ageppert/Core-64-Interactive-Core-Memory-Badge/Electronic Design/Core64 CB v0.4/Core64 CB V0.4 PCB Back.pdf

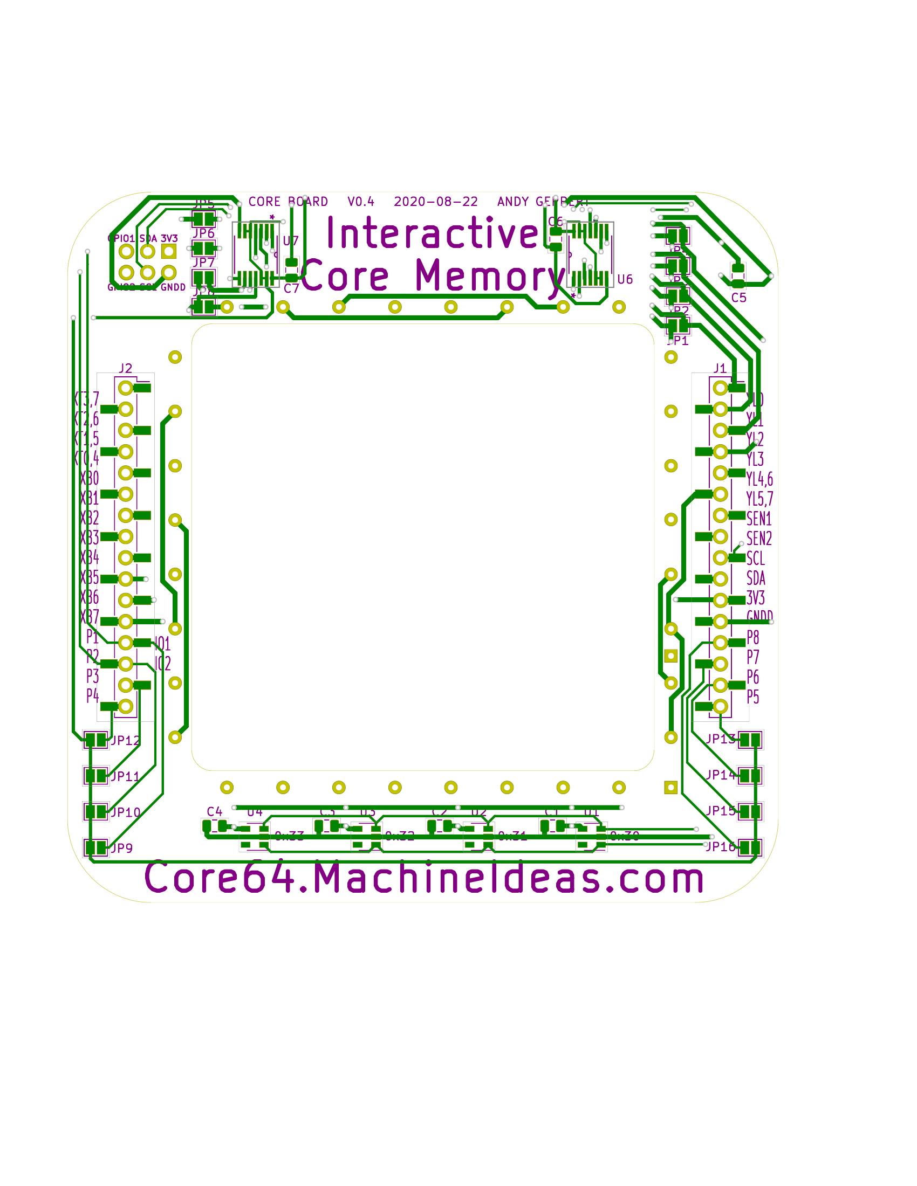
[picture p16: page 1]
