ageppert/Core-64-Interactive-Core-Memory-Badge/Datasheets/NPN to N-Channel pin compatible.png

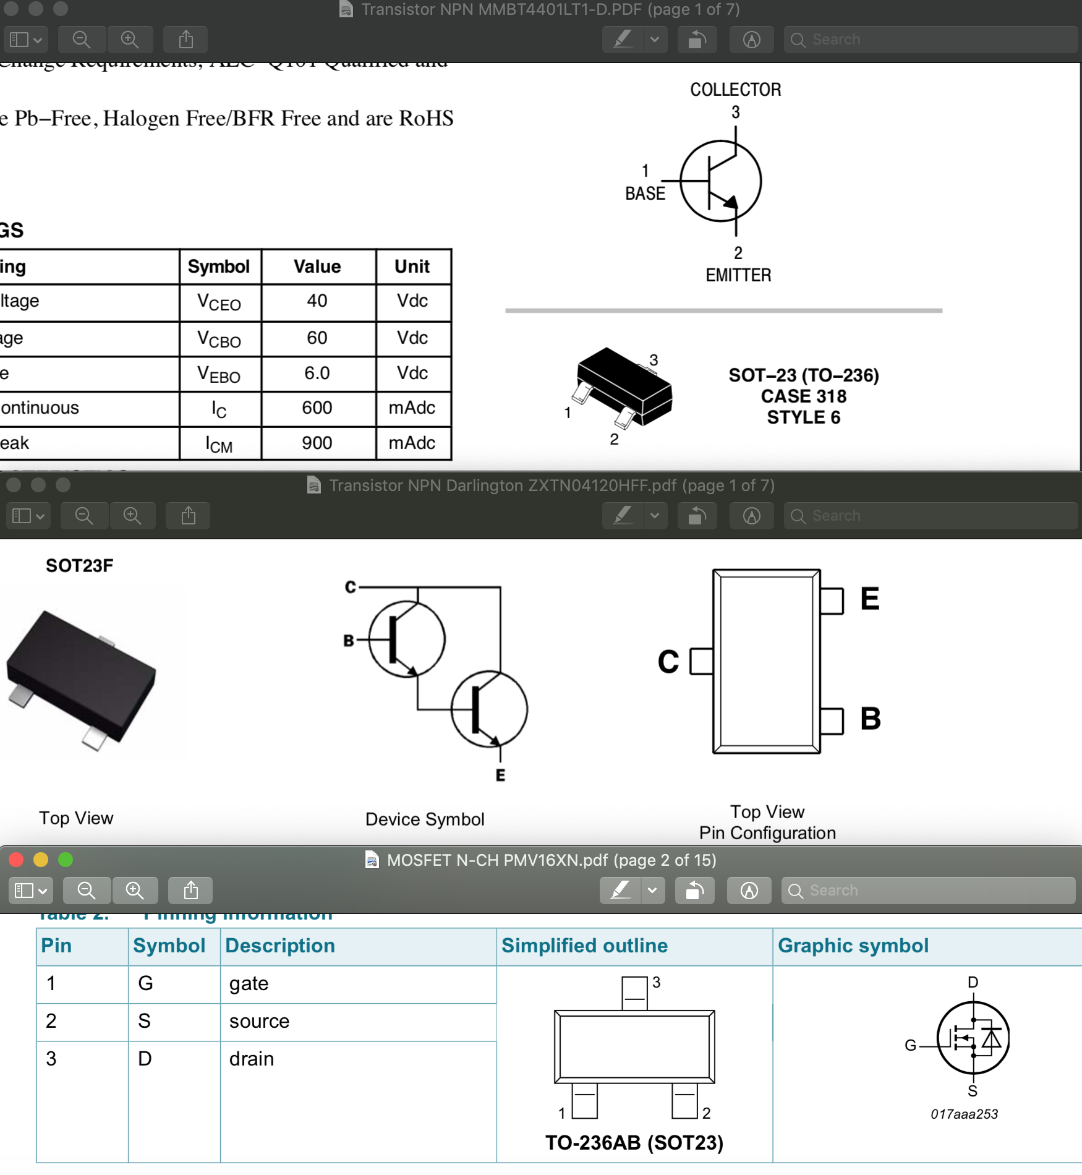
Datasheets/NPN to N-Channel pin compatible.png
