ageppert/Core-64-Interactive-Core-Memory-Badge/Datasheets/Pimoroni Board Layout Top View.png

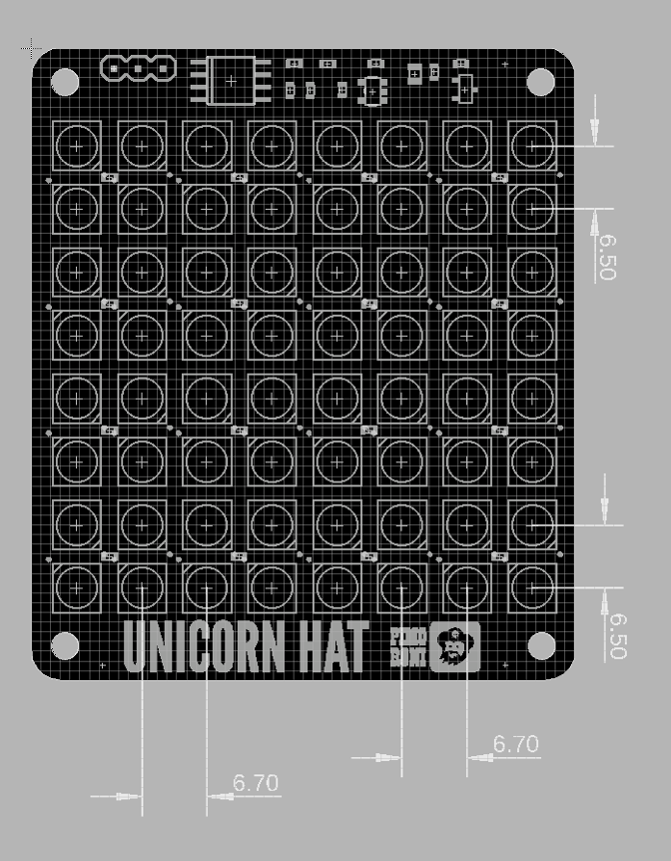
Datasheets/Pimoroni Board Layout Top View.png
