ageppert/Core-64-Interactive-Core-Memory-Badge/Datasheets/PNP to P-Channel pin compatible.png

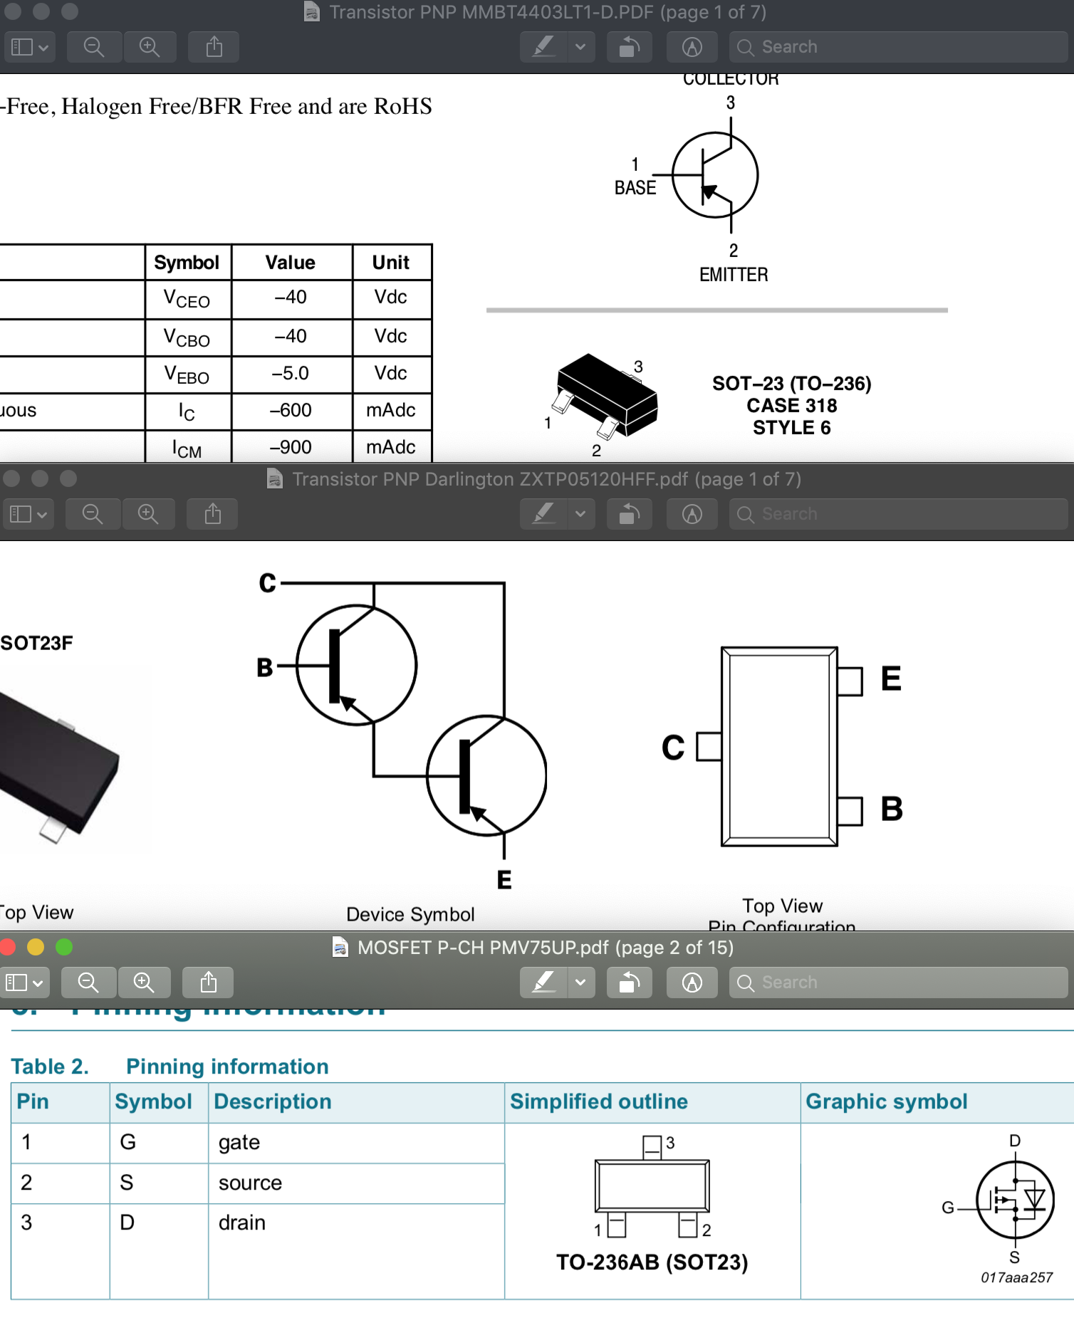
Datasheets/PNP to P-Channel pin compatible.png
