ageppert/Core-64-Interactive-Core-Memory-Badge/Datasheets/Reverse Voltage Protection with MOSFET.png

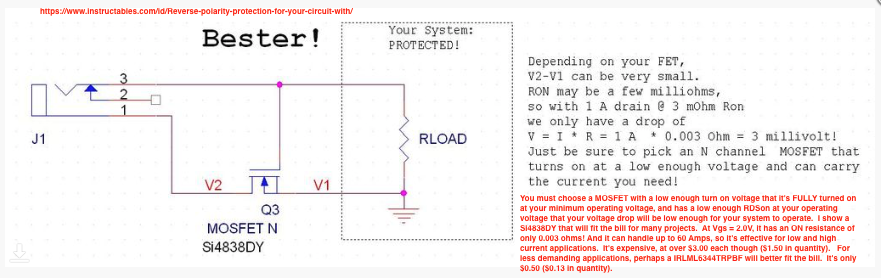
Datasheets/Reverse Voltage Protection with MOSFET.png
