ageppert/Core-64-Interactive-Core-Memory-Badge/Datasheets/Teensy 3.2 schematic.gif

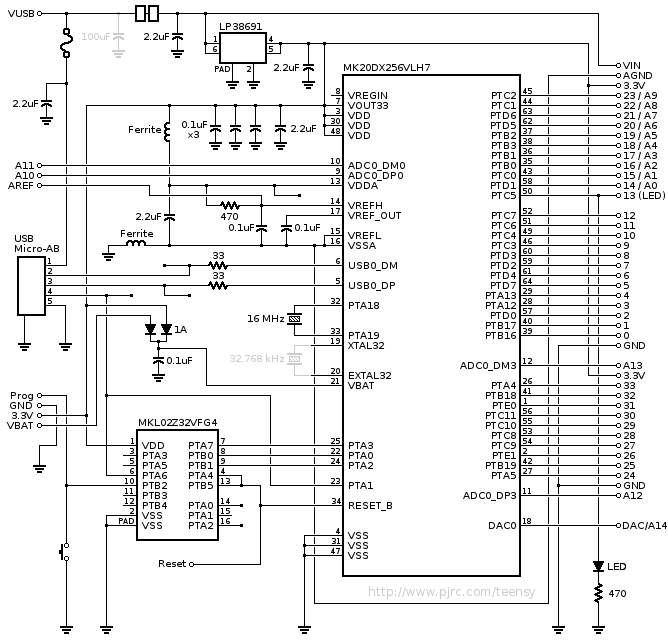
Datasheets/Teensy 3.2 schematic.gif
