ageppert/Core-64-Interactive-Core-Memory-Badge/Datasheets/Teensy LC Schematic.gif

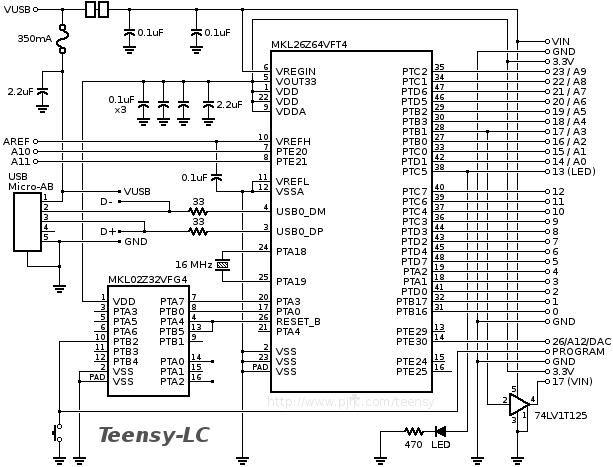
Datasheets/Teensy LC Schematic.gif
