ageppert/Core-64-Interactive-Core-Memory-Badge/Electronic Design/Core64 CB v0.4-NP/Core64 CB v0.4-NP render back.png

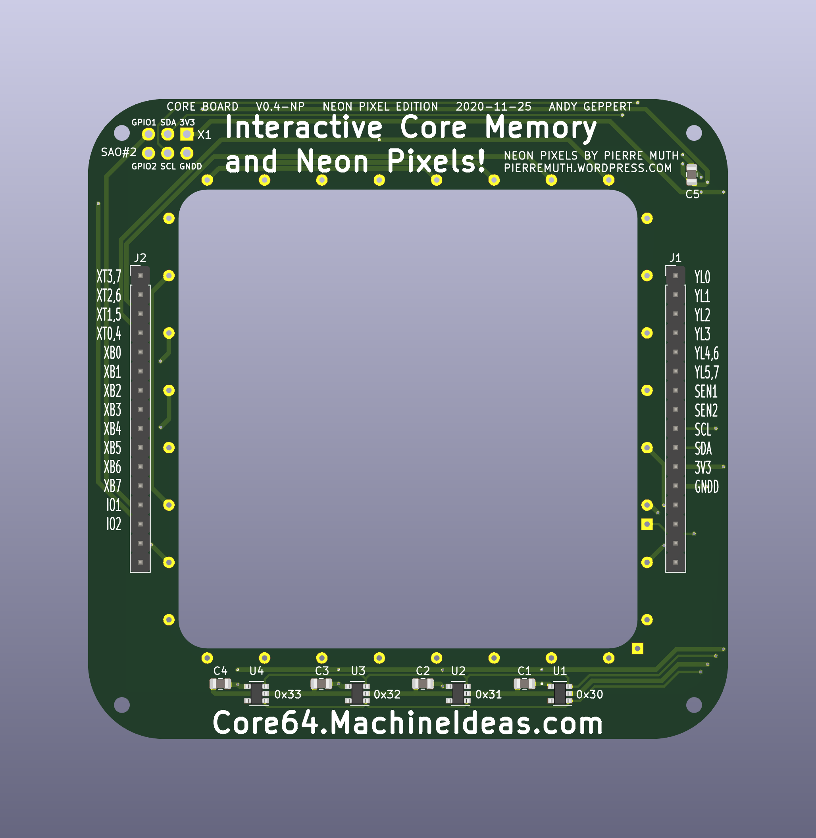
Electronic Design/Core64 CB v0.4-NP/Core64 CB v0.4-NP render back.png
