ageppert/Core-64-Interactive-Core-Memory-Badge/Electronic Design/Core64 HB v0.1/Core64_HB_Outputs/Hacker board V0.1 render front.png

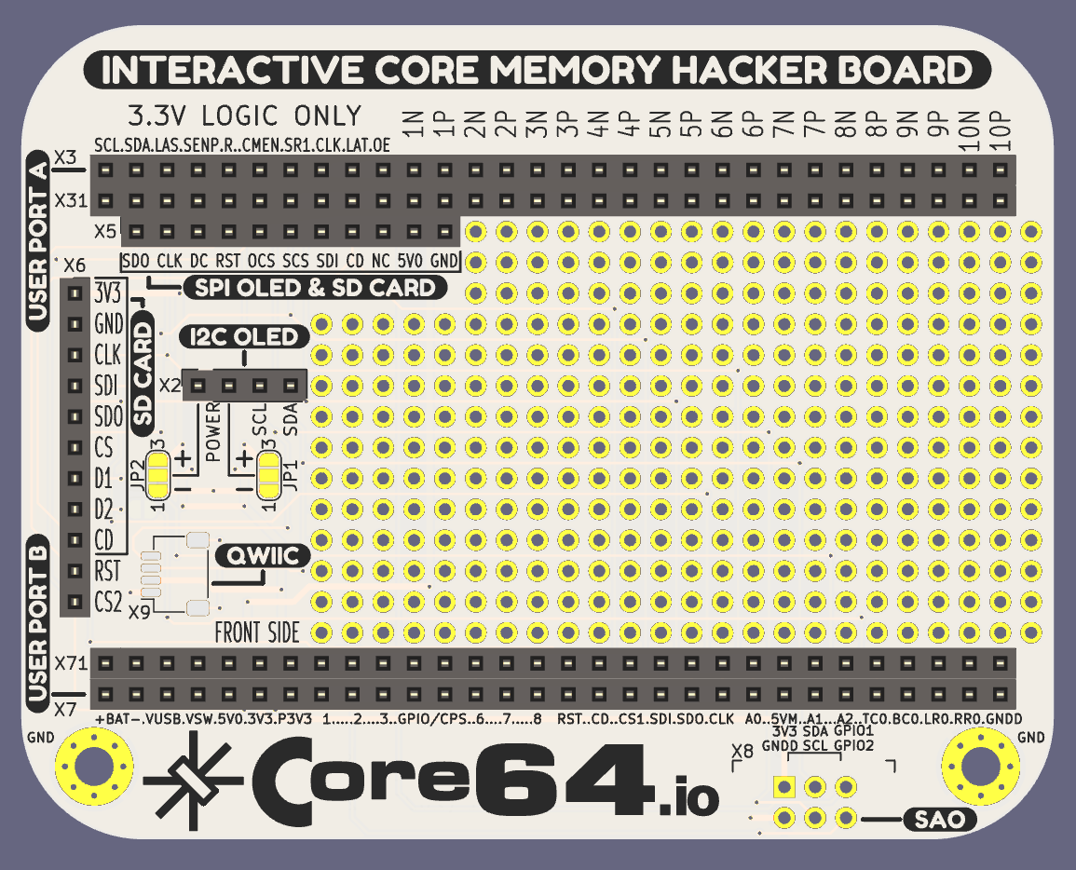
Electronic Design/Core64 HB v0.1/Core64_HB_Outputs/Hacker board V0.1 render front.png
