ageppert/Core-64-Interactive-Core-Memory-Badge/Electronic Design/Core64 LA v1.3 KiCAD 6/C64_LA_V1.3 Schematic and Renders/Core64 LED Array v1.3 Render Front.png

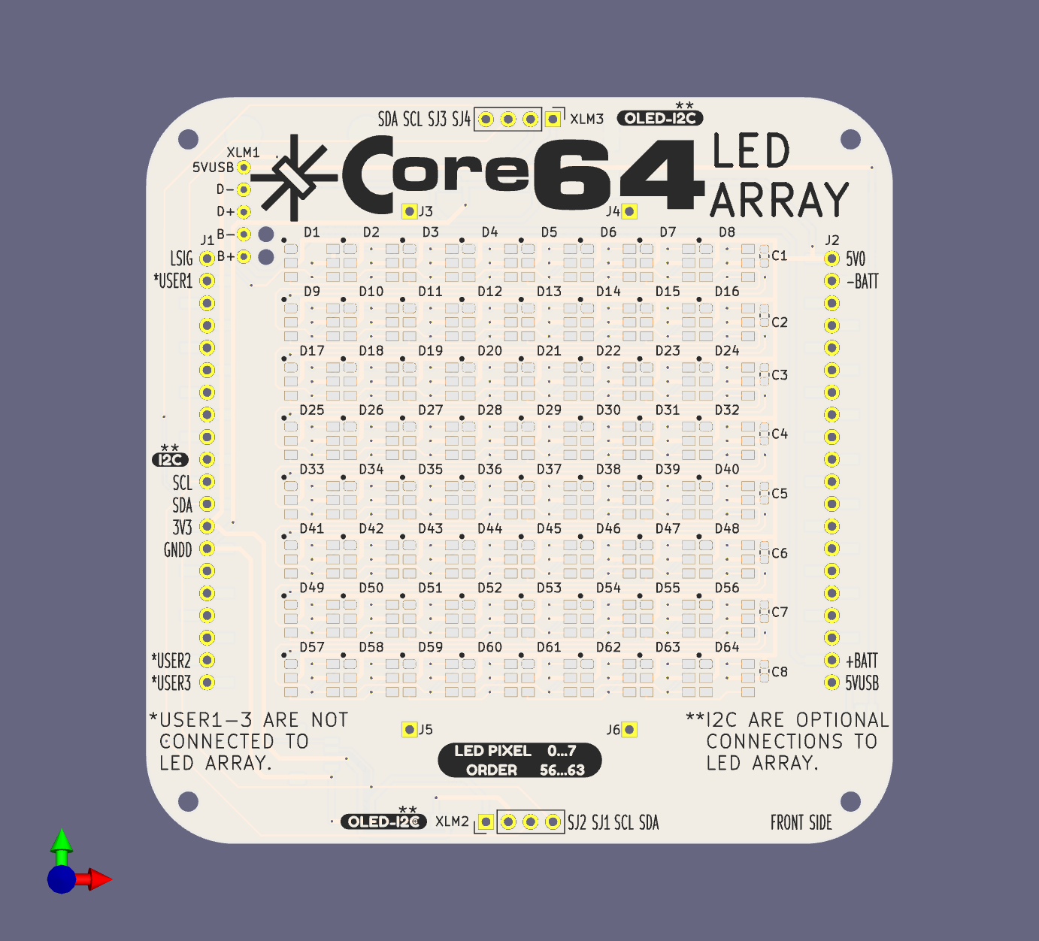
Electronic Design/Core64 LA v1.3 KiCAD 6/C64_LA_V1.3 Schematic and Renders/Core64 LED Array v1.3 Render Front.png
