ageppert/Core-64-Interactive-Core-Memory-Badge/Electronic Design/Core64 LB v0.6/Core64 LB v0.6 Render Top.png

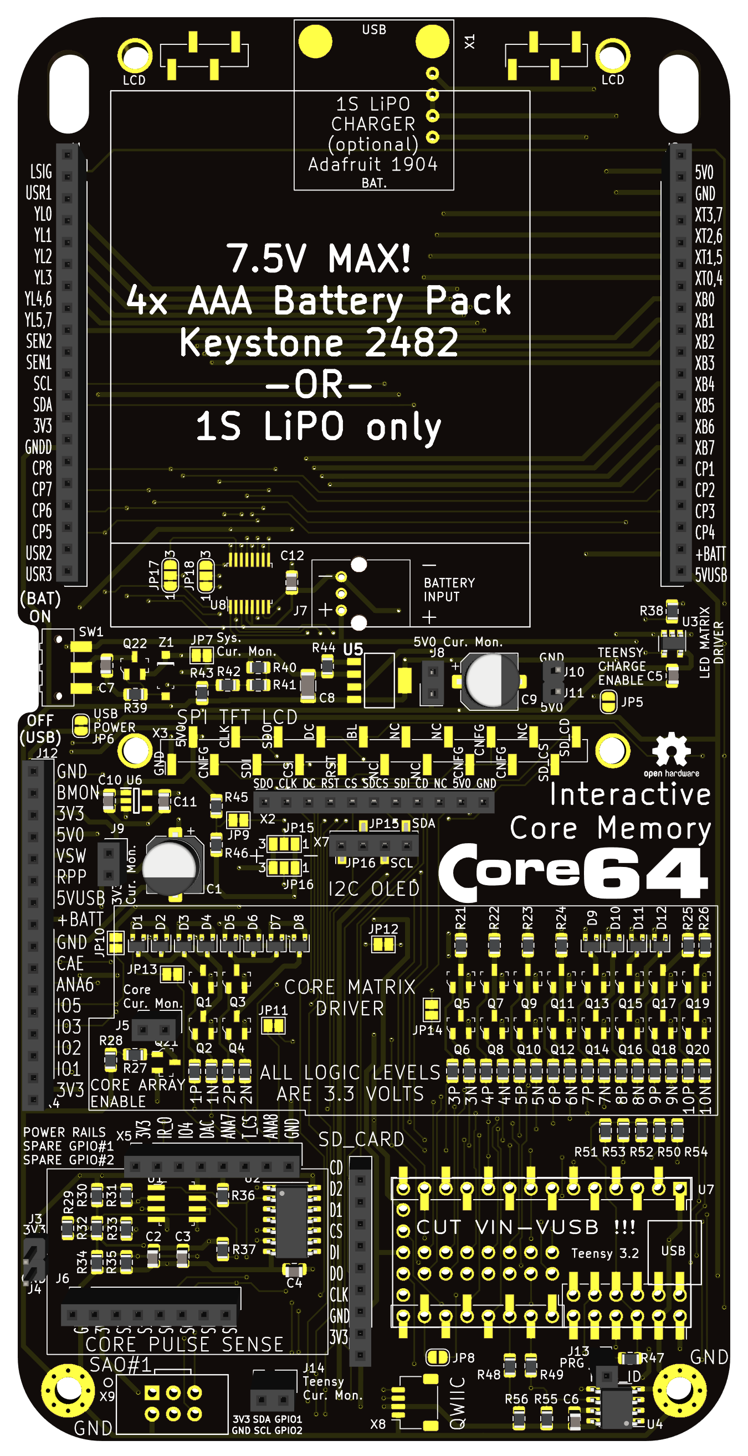
Electronic Design/Core64 LB v0.6/Core64 LB v0.6 Render Top.png
