ageppert/Core-64-Interactive-Core-Memory-Badge/Electronic Design/Core64 LB v0.8 KiCAD 6/Core64_LB_V0.8.5 2025-04-24 Qty 30/904882295554048-Produce_DanZhi.SMT_Snapshot.Top.2721632A_Y74.SMT025042462656.png

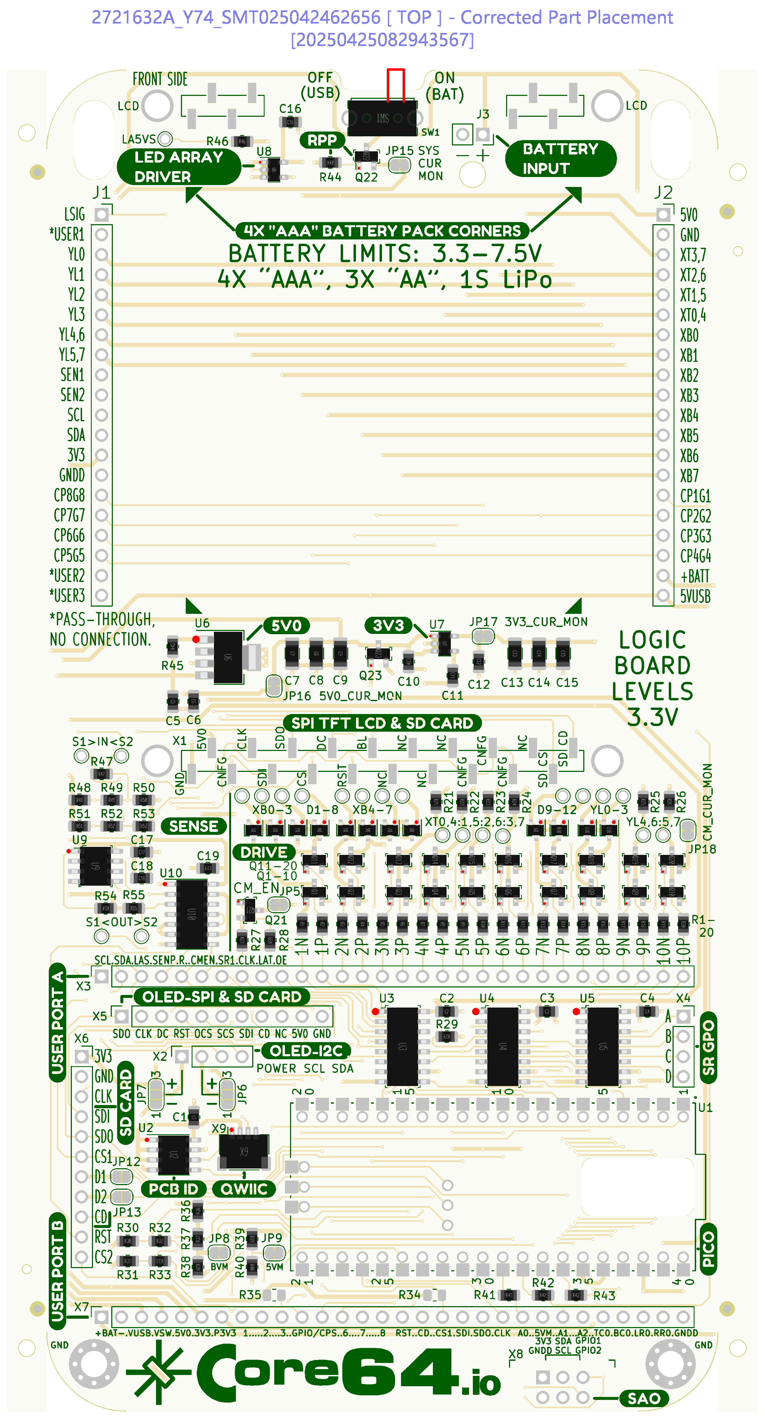
Electronic Design/Core64 LB v0.8 KiCAD 6/Core64_LB_V0.8.5 2025-04-24 Qty 30/904882295554048-Produce_DanZhi.SMT_Snapshot.Top.2721632A_Y74.SMT025042462656.png
