ageppert/Core-64-Interactive-Core-Memory-Badge/Electronic Design/Core64 LM v1.0/Core64 LM v1.0 Render Back.png

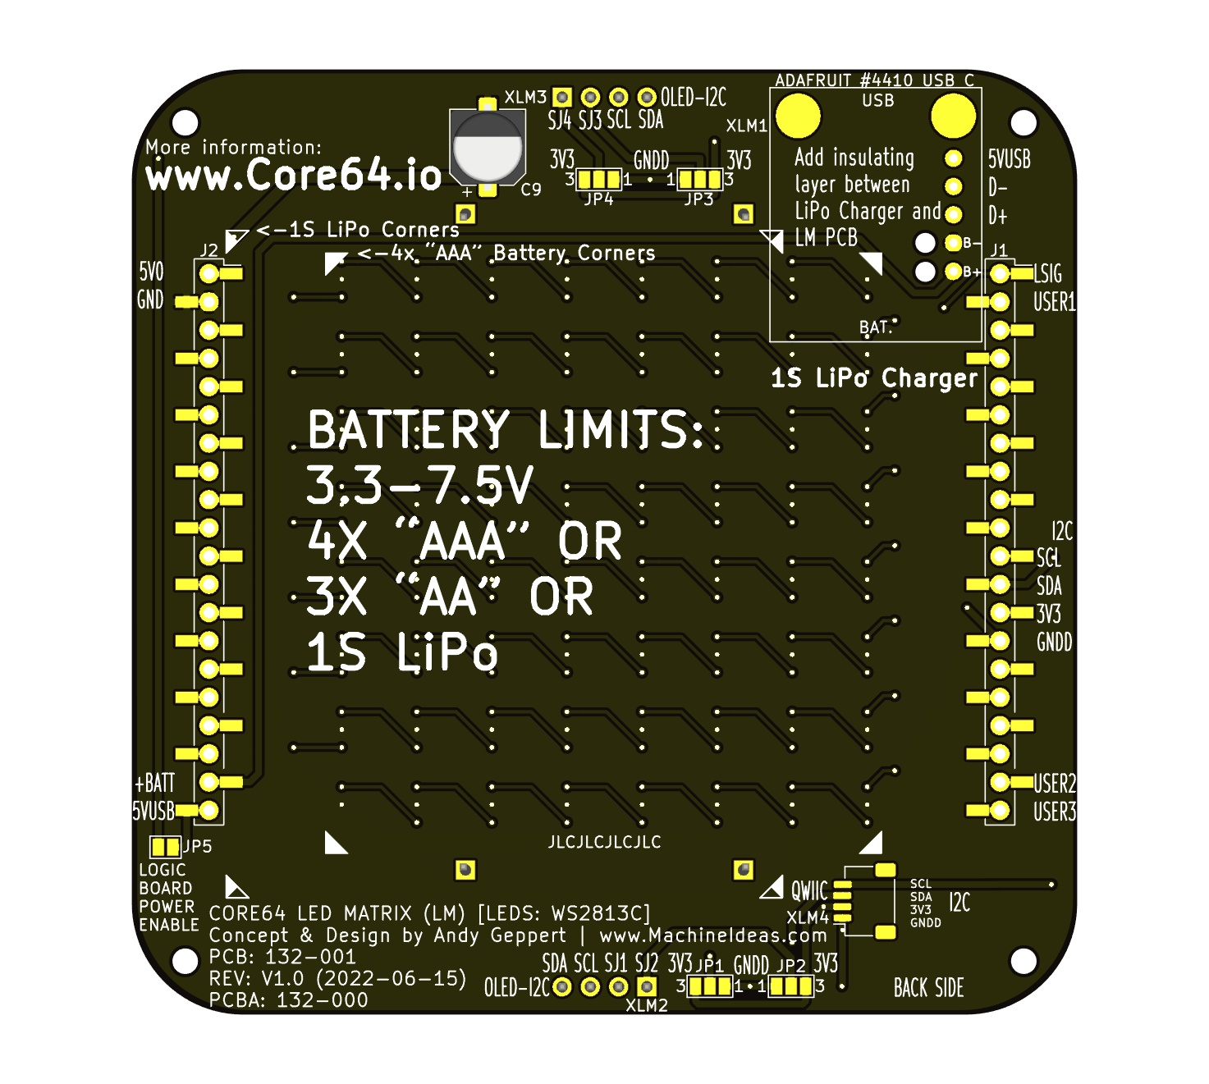
Electronic Design/Core64 LM v1.0/Core64 LM v1.0 Render Back.png
