ageppert/Core-64-Interactive-Core-Memory-Badge/Electronic Design/Core64 Stylus v0.5/Core64 Stylus Render Front.png

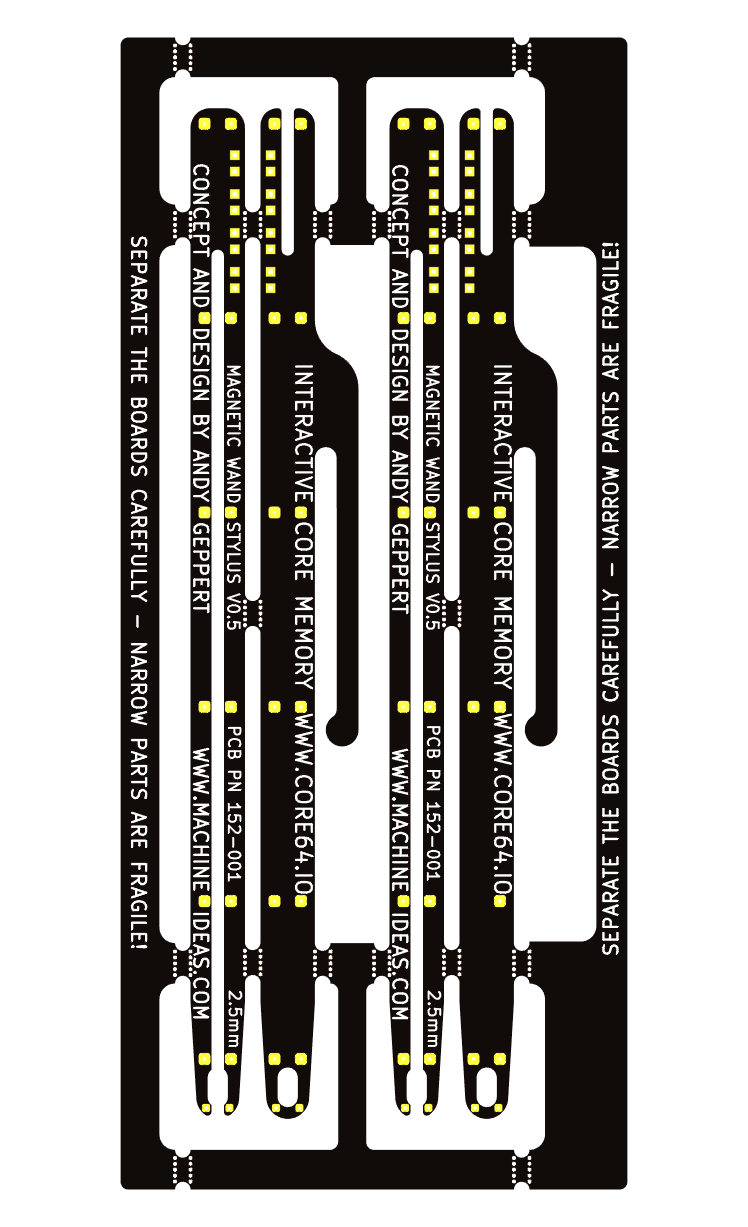
Electronic Design/Core64 Stylus v0.5/Core64 Stylus Render Front.png
