ageppert/Core-64-Interactive-Core-Memory-Badge/Electronic Design/Core64 Stylus v0.6 KiCAD 7/Outputs/Core64 Stylus v0.6 Render Front.png

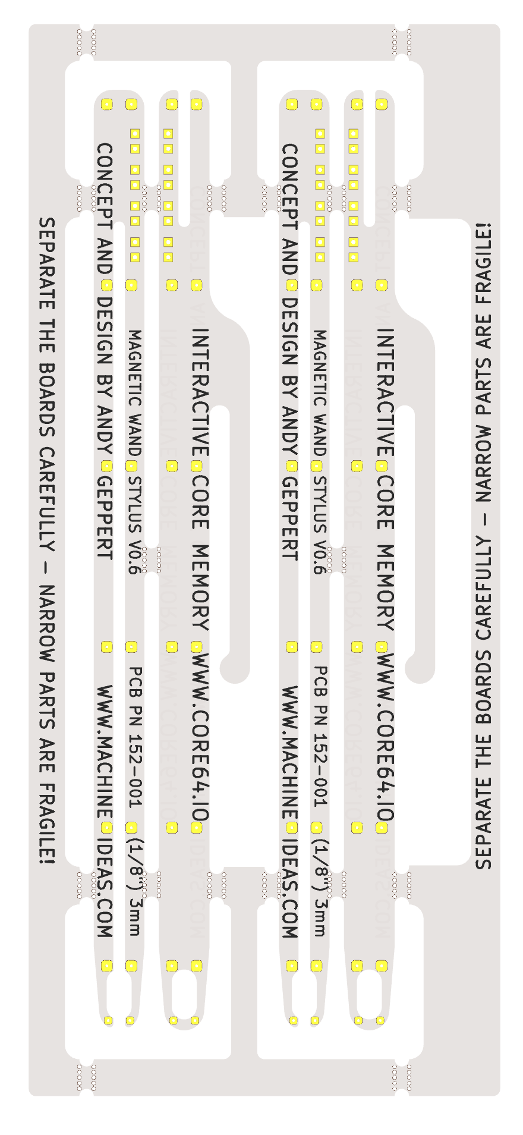
Electronic Design/Core64 Stylus v0.6 KiCAD 7/Outputs/Core64 Stylus v0.6 Render Front.png
