ageppert/Core-64-Interactive-Core-Memory-Badge/Electronic Design/Core64 Stylus v0.6 KiCAD 7/Photos/IMG_6821.jpeg

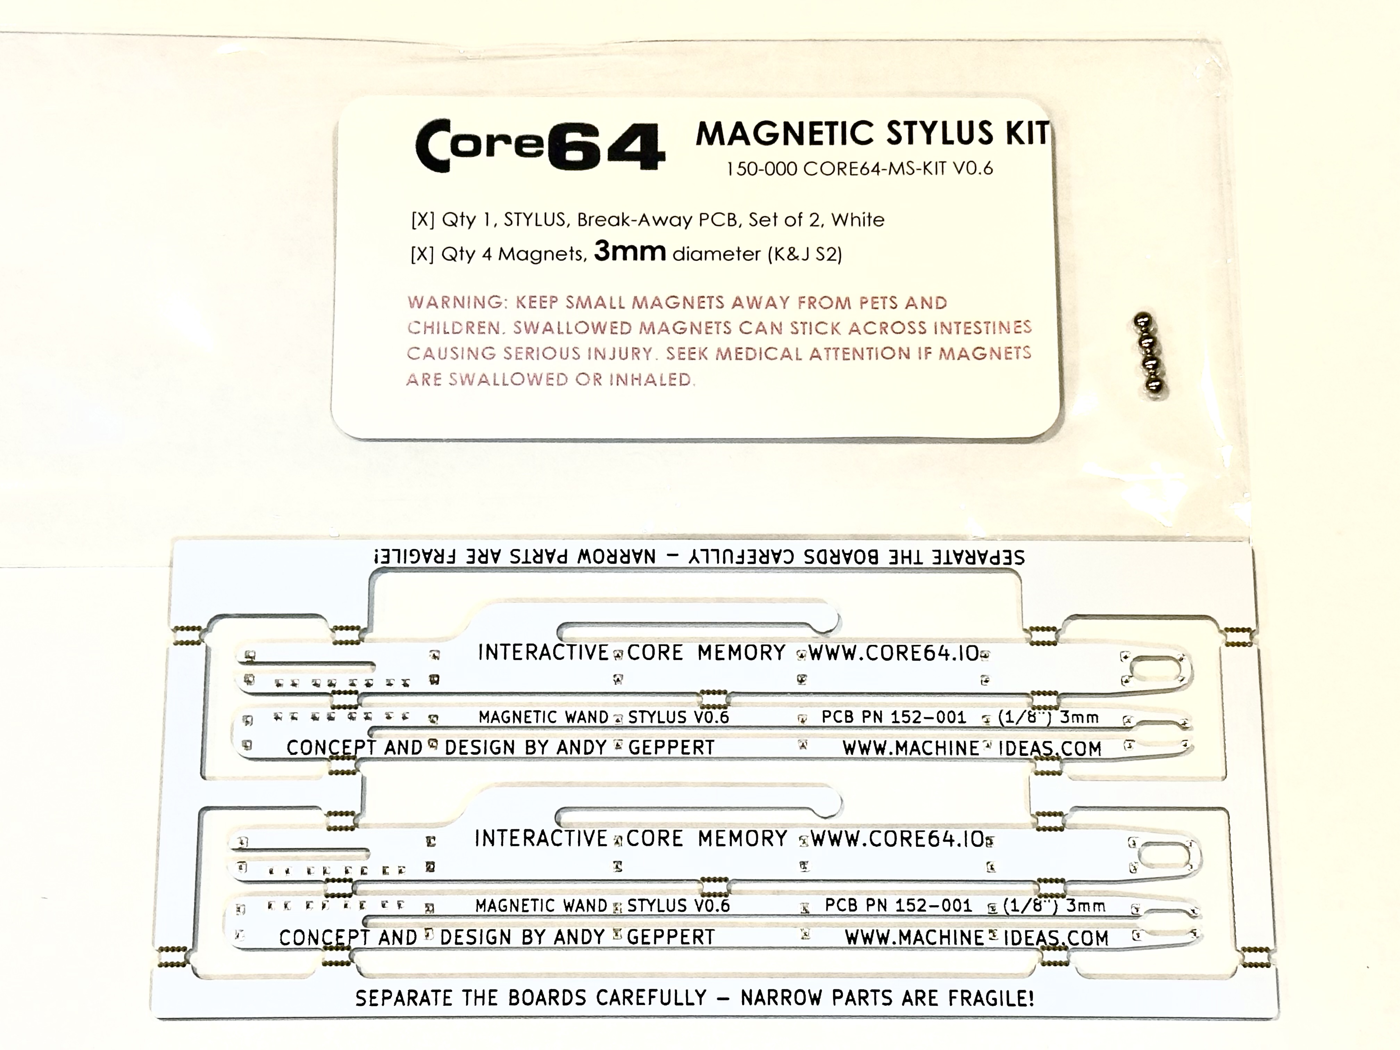
Electronic Design/Core64 Stylus v0.6 KiCAD 7/Photos/IMG_6821.jpeg
