ageppert/Core-64-Interactive-Core-Memory-Badge/Electronic Design/Neon PIxels/Backplane board dimensions.png

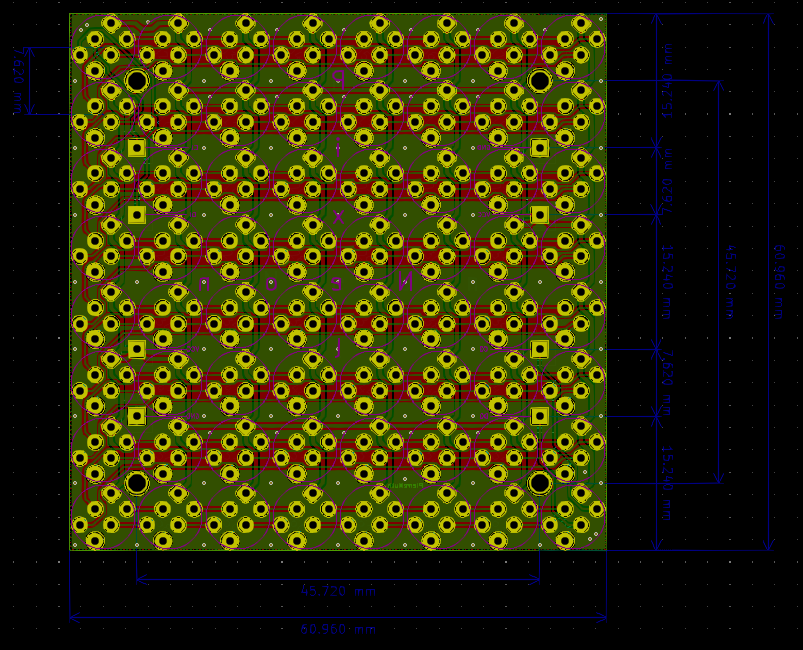
Electronic Design/Neon PIxels/Backplane board dimensions.png
