ageppert/Core-64-Interactive-Core-Memory-Badge/Images/Core64_v0.3_Dual_Red_Board_CAD.png

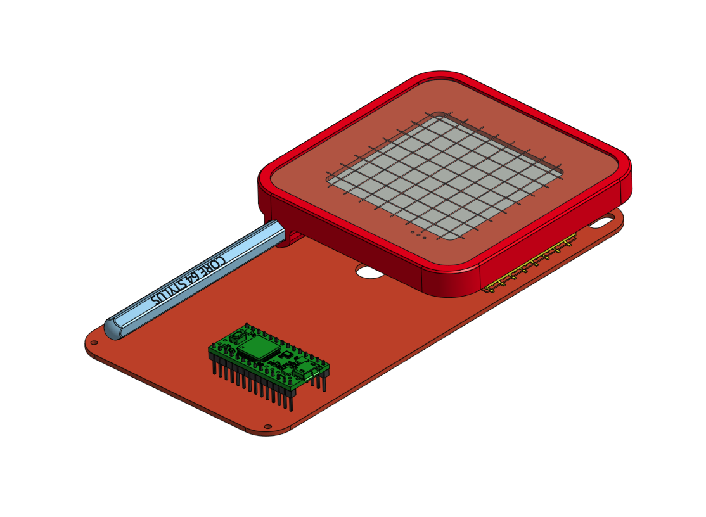
Images/Core64_v0.3_Dual_Red_Board_CAD.png
