ageppert/Core-64-Interactive-Core-Memory-Badge/Electronic Design/Core64 LA v1.3 KiCAD 6/C64_LA_V1.3 Manufacturing by ELECROW/Core64 LED Array Manufacturing Instructions (B).pdf

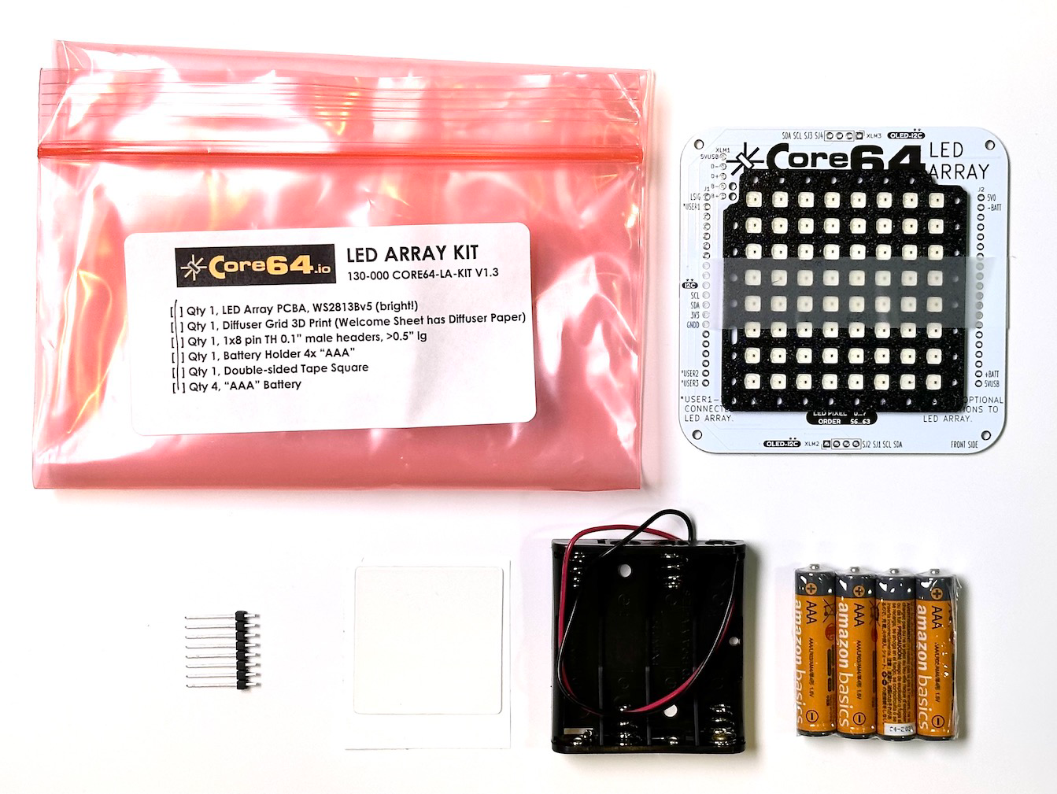
[picture p56: figure]

### Core64 LED Array Kit Instructions – Machine Ideas, LLC

# Core64 LED ARRAY KIT V1.3 Manufacturing Instruc?ons

Doc. Ver. | Descrip-on | Date | Author
A | First dra6. | 2023-05-22 | Andrew Geppert
B | Update details and add complete sub-kiDng details. | 2025-01-01 | Andrew Geppert

## TABLE OF CONTENTS

TABLE OF CONTENTS

TABLE OF CONTENTS | 2
INTRODUCTION | 3
MANUFACTURING FILES | 3
PCB FABRICATION | 4
PCBA SMD AUTOMATICALLY ASSEMBLED COMPONENTS | 5
PCBA TEST | 6
PCBA MARKING | 8
PCBA KIT COMPONENTS | 9
PCBA KIT ASSEMBLY | 10
APPENDIX A: EXAMPLES OF GOOD LEDS | 11
APPENDIX B: EXAMPLES OF BAD LEDS | 11
APPENDIX C: LED REFERENCE NOTES | 12

## INTRODUCTION

This document explains the informa-on required to:
- Manufacture the PCB
- Assemble the SMD components
- Test the PCB Assembly
- Create the sub-kit by adding the user assembled items into a labeled bag

## MANUFACTURING FILES

Available in the sub-folders here:
hQps://github.com/ageppert/Core-64-Interac-ve-Core-Memory-Badge/tree/master/Electronic%20Design/Core64%20LA%20v1.3%20KiCAD%206/C64_LA_V1.3%20Man ufacturing%20by%20ELECROW

This Instruc-on document: Core64 LED Array Manufacturing Instruc-ons (B).pdf

PCB Gerber and drill files: Core64_LA_v1.3_Gerbers (removed JLC text).zip

PCBA BOM file: Core64 LA v1.3_BOM_SMD_Assembly.xlsx

Placement CPL file: Core64 LA v1.3_CPL_SMD_Assembly.xlsx

PCBA S-cker file: Core64 LA v1.3_PCBA_S-cker.docx

Sub-Kit BOM file: Core64 LA v1.3_BOM_sub-kit_Assembly.xlsx

Sub-Kit Label file: Core64 LED Array V1.3 Sub-Kit Label.docx

Diffuser Grid file: Core64 LA Diffuser Grid V11 Square 6.75mm centers.zip

## PCB FABRICATION

Standard materials:
Material: FR4
Board Thickness: 1/16” inch Copper Weight: 1 oz.
Solder Mask: White
Silkscreen: Black
Finish: HASL
Leadfree: Not required
Rails and paneliza-on: manufacture’s choice, but please do not add tooling holes to the main PCB.
Remove manufacturing ID number.

## PCBA SMD AUTOMATICALLY ASSEMBLED COMPONENTS

Serially Addressable RGB LED World Semi P/N WS2813C

1. The most challenging part of this assembly process is ensuring high quality LEDs are used to avoid rework a6er assembly and tes-ng is completed. See Appendix A and B to iden-fy GOOD and BAD LED types which have been observed. As of this wri-ng, the quality seems to vary from different suppliers.
2. Observe moisture and component manufacturer baking recommenda-ons for the LEDs in this assembly.
3. As of this wri-ng, the only component allowed is WS2813C. A possible subs-tu-on may be WS2913B (much brighter with increased current draw) but must be approved by the author of this document.
4. LED orienta-on. Pin 1 in upper le6 with DOT on silkscreen and NOTCH on LED.

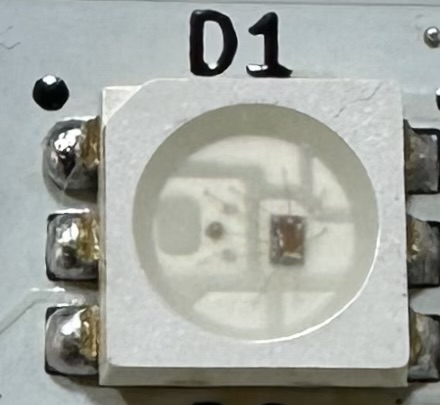
[picture p57: figure]

Capacitors
Subs-tu-ons are allowed. Please inform the author of this document prior to procurement to confirm the subs-tu-on details are acceptable.

Cleaning
If flux is not visible to the unaided eye around the solder joints, cleaning is not required. If there is flux visible, cleaning is necessary.

## PCBA TEST

Ensure all LEDs are func-onal with similar brightness. Each color (Red, Green, Blue) shall be tested in each LED.

Connec-ons to the board for tes-ng:

Label | DescripFon
-BATT | Ground
5V0 | 3.3 or 5 VDC (must match the logic signal)
LSIG | LED Serial Data Signal (3.3 or 5 logic signal)

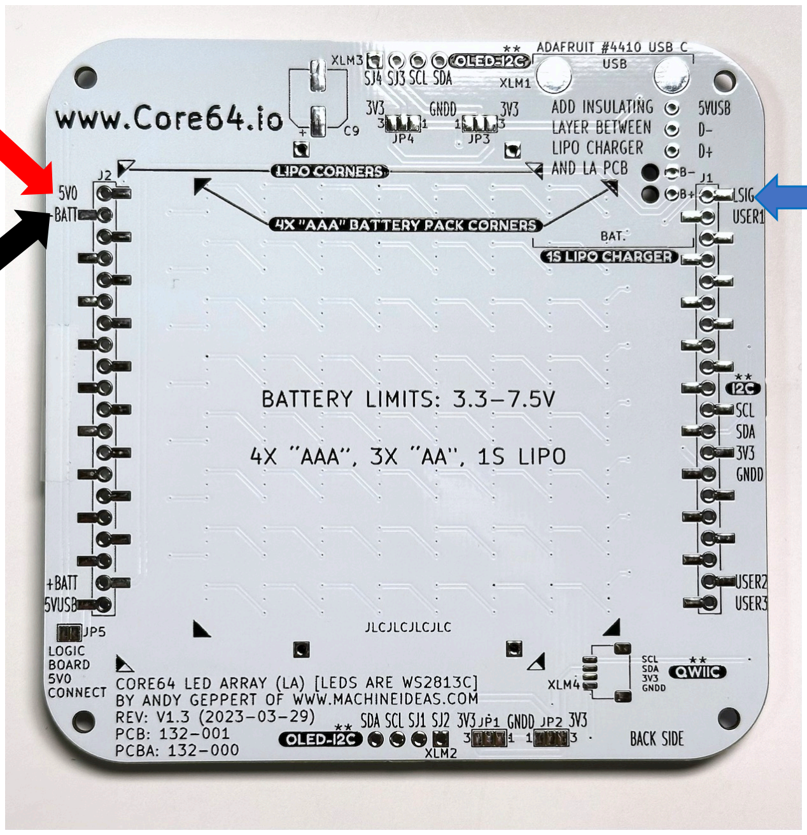
[picture p58: figure]

Tes-ng may be accomplished with any Arduino compa-ble MCU board, or similar. The serially addressable LEDs require a library such as: hQps://github.com/adafruit/Adafruit_NeoPixel

All of the Core64 / Core64c / Core16 kits use a Raspberry Pi Pico W so that is a good choice for the test fixtures. This helps standardize all of the test firmware onto a common MCU planorm.

A sample program is “Core64_LED_ARRAY_Test_RP2040_V1.ino.uf2”
Located: hQps://github.com/ageppert/Core-64-Interac-ve-Core-Memory-Badge/tree/master/Firmware%20Source%20Code/Core64_LED_ARRAY_Test

The file can be installed directly on the Pico by drag-n-drop with a USB cable connec-on. No IDE is needed. Boot the Pico with the boot buQon held down, and the Pico will show up on the desktop as a USB drive. Drag and drop the file “Core64_LED_ARRAY_Test_RP2040_V1.ino.uf2” onto the USB drive.

IMPORTANT: Make the power and signal wire connec-ons to the LED Array PCBA without power ON. A6er the connec-ons are made, power on the test fixture. A6er the test is completed, power OFF. Then remove the electrical connec-ons from the PCBA.

When the Pico is powered on, the test program begins automa-cally. It cycles through these steps repeatedly with a 50% brightness level.
1) All LEDS RED
2) All LEDS GREEN
3) All LEDS BLUE

If each LED shows every color, then the test is passed.

If the test does not pass, rework the PCBA to replace all failed LEDs. Then retest.

## PCBA MARKING

A6er the test is successfully completed, a s-cker or laser etching is applied to the boQom side of the LED ARRAY Board.

Size: 1-3mm tall leQering
S-cker Zone Loca-on: near the boQom, above the “PCBA: 132-000” field

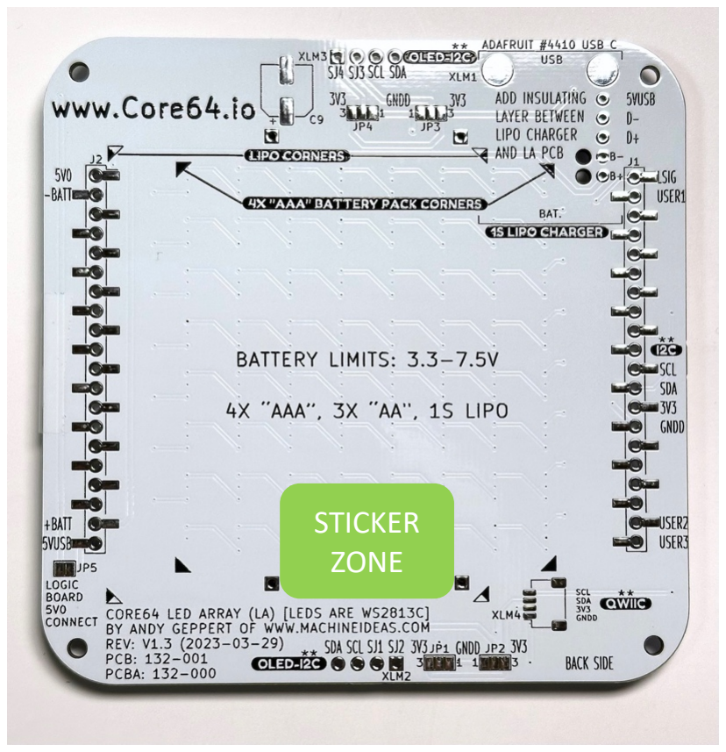
[picture p59: figure]
STICKER ZONE

Suggested Contents from “Core64 LA v1.3_PCBA_S-cker.docx”

QC: Passed
MFR: Elecrow YYWW
PCBA VER: 1.3
LED: WS2813C

QC is Quality Check
Elecrow is manufacturer
YY is the last two digits of the year of assembly.
WW is the week number of assembly.
V1.3 denotes the version of the PCB Assembly. It will be updated if alternate components are used.
LED WS2813C is the LED used. If an alternate LED is used, the associated P/N will be subs-tuted on the s-cker.

## PCBA KIT COMPONENTS

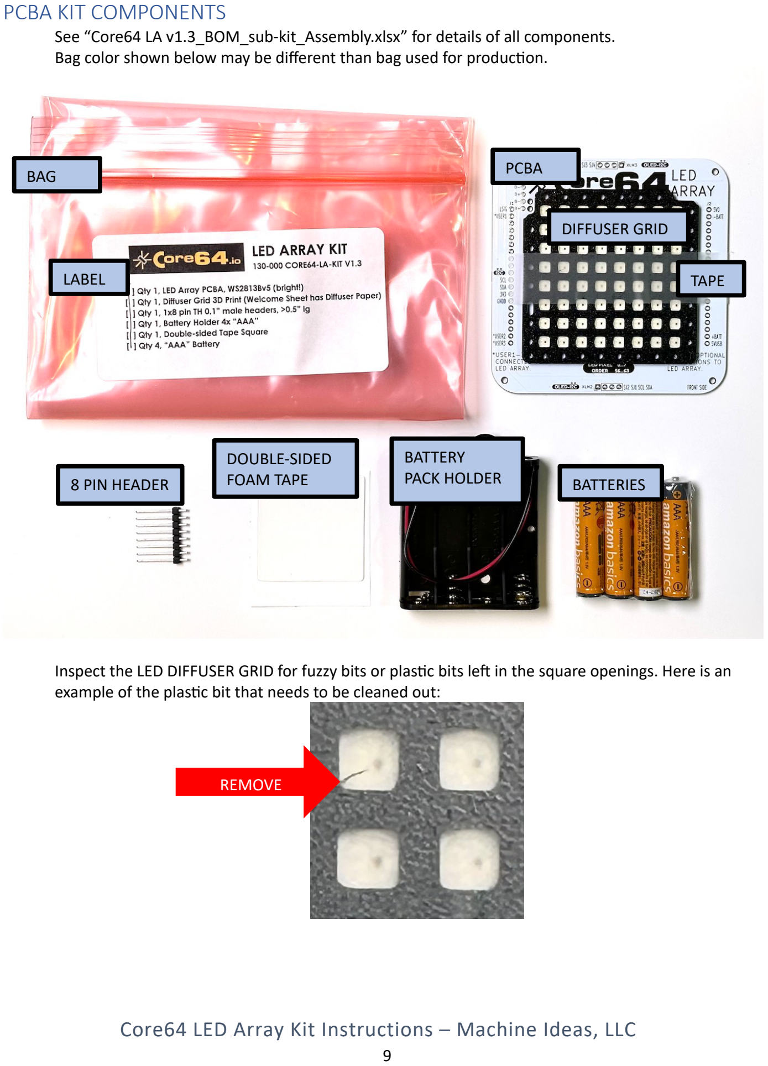
[picture p60: page 9]

See “Core64 LA v1.3_BOM_sub-kit_Assembly.xlsx” for details of all components. Bag color shown below may be different than bag used for produc-on.

Inspect the LED DIFFUSER GRID for fuzzy bits or plas-c bits le6 in the square openings. Here is an example of the plas-c bit that needs to be cleaned out:

BAG

LABEL

PCBA

DIFFUSER GRID

TAPE

BATTERIES

BATTERY
PACK HOLDER

DOUBLE-SIDED
FOAM TAPE 8 PIN HEADER

REMOVE

## PCBA KIT ASSEMBLY

1. Gather the components.
2. Place sub-kit label on the bag.
3. Place LED diffuser over the LEDs and secure it in place with tape. This protects the LEDs during shipping. Place the tape in the green boxed zone:

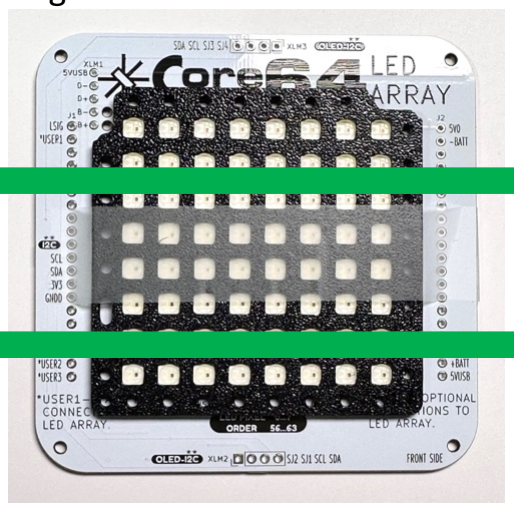
[picture p61: figure]

4. Insert all components into the bag.

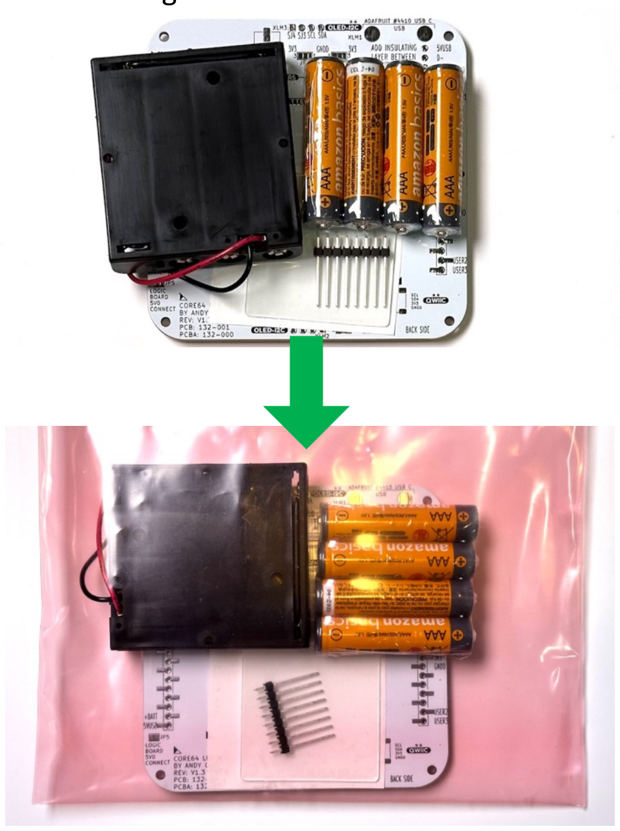
[picture p62: figure]

5. Ensure the loose components are placed behind the LED board, on the side with the LEDs.

## APPENDIX A: EXAMPLES OF GOOD LEDS

This LED package resulted in LED Arrays with 100% yield. Ini-ally purchased as LCSC P/N ________ in 2022.

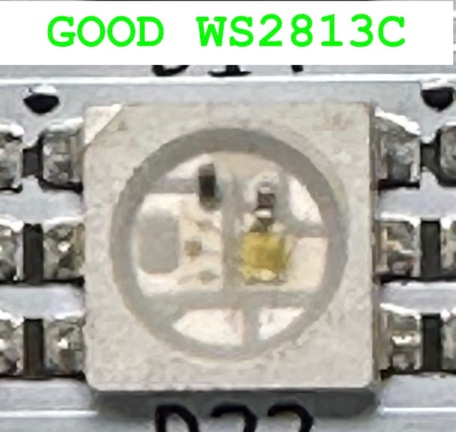
[picture p63: figure]

This LED sampled May 2023 and test assembled by the author, 64 of 64 worked first -me.
DIGIKEY P/N 1597-1594
hQps://www.digikey.com/en/products/detail/seeed-technology-co-ltd/601000200/8120706 Supplied from SEEED Technology Co., Ltd
U-lizing Worldsemi WS2813B (5050) Ver. No. 5

## APPENDIX B: EXAMPLES OF BAD LEDS

This version of the WS2813C provided low yields.

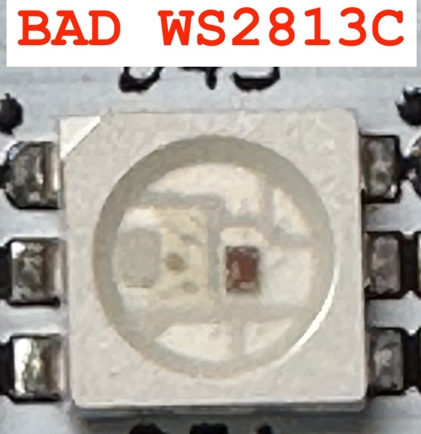
[picture p64: figure]

## APPENDIX C: LED REFERENCE NOTES

Firmware Libraries for LED Control (WS2812 and WS2813 libraries are compa-ble): hQps://github.com/adafruit/Adafruit_NeoPixel hQps://learn.adafruit.com/adafruit-neopixel-uberguide

QUALITY CONCERNS
A test method for LED epoxy poDng quality:
hQps://youtu.be/SWh7Watb_LE
from
hQps://wp.josh.com/2016/10/29/a-quick-test-for-crappy-ws2812b-neopixels/

Alterna-ve to WS2812 is SK6812 hQps://cpldcpu.wordpress.com/2016/03/09/the-sk6812-another-intelligent-rgb-led/

More stories:
hQps://talk.vanhack.ca/t/psa-ws2812b-leds-may-not-be-what-you-think-they-are/5626
