ageppert/Core-64-Interactive-Core-Memory-Badge/Electronic Design/Core64 LB v0.8 KiCAD 6/Core64_LB_V0.8 2023-03 Build of 25/Produce_DanZhi.SMT_Snapshot.Top.2721632A_Y38.SMT02303201172832.png

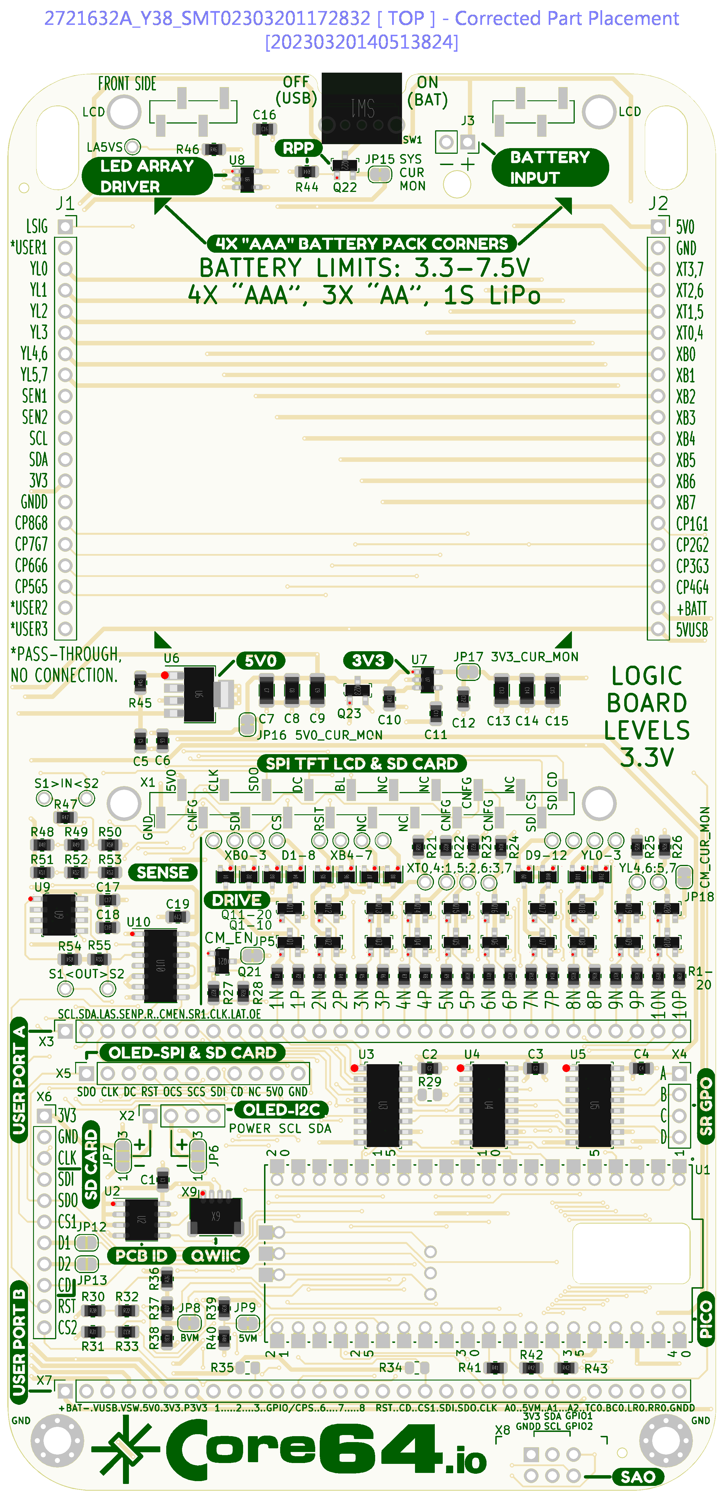
Electronic Design/Core64 LB v0.8 KiCAD 6/Core64_LB_V0.8 2023-03 Build of 25/Produce_DanZhi.SMT_Snapshot.Top.2721632A_Y38.SMT02303201172832.png
