ageppert/Core-64-Interactive-Core-Memory-Badge/Electronic Design/Core64 LB v0.8 KiCAD 6/Core64_LB_V0.8 2024-03 Build of 25/Screenshot 2024-03-10 at 10.28.37 PM.png

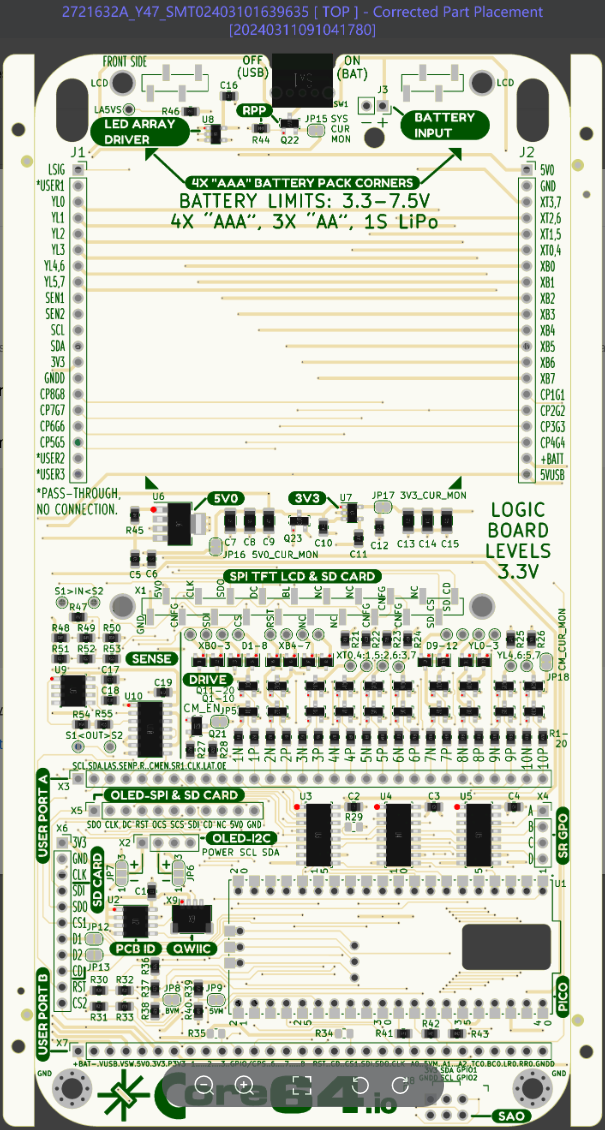
Electronic Design/Core64 LB v0.8 KiCAD 6/Core64_LB_V0.8 2024-03 Build of 25/Screenshot 2024-03-10 at 10.28.37 PM.png
