ageppert/Core-64-Interactive-Core-Memory-Badge/Manufacturing/Elecrow Led Array Boards/DHL Shipping size and weight.png

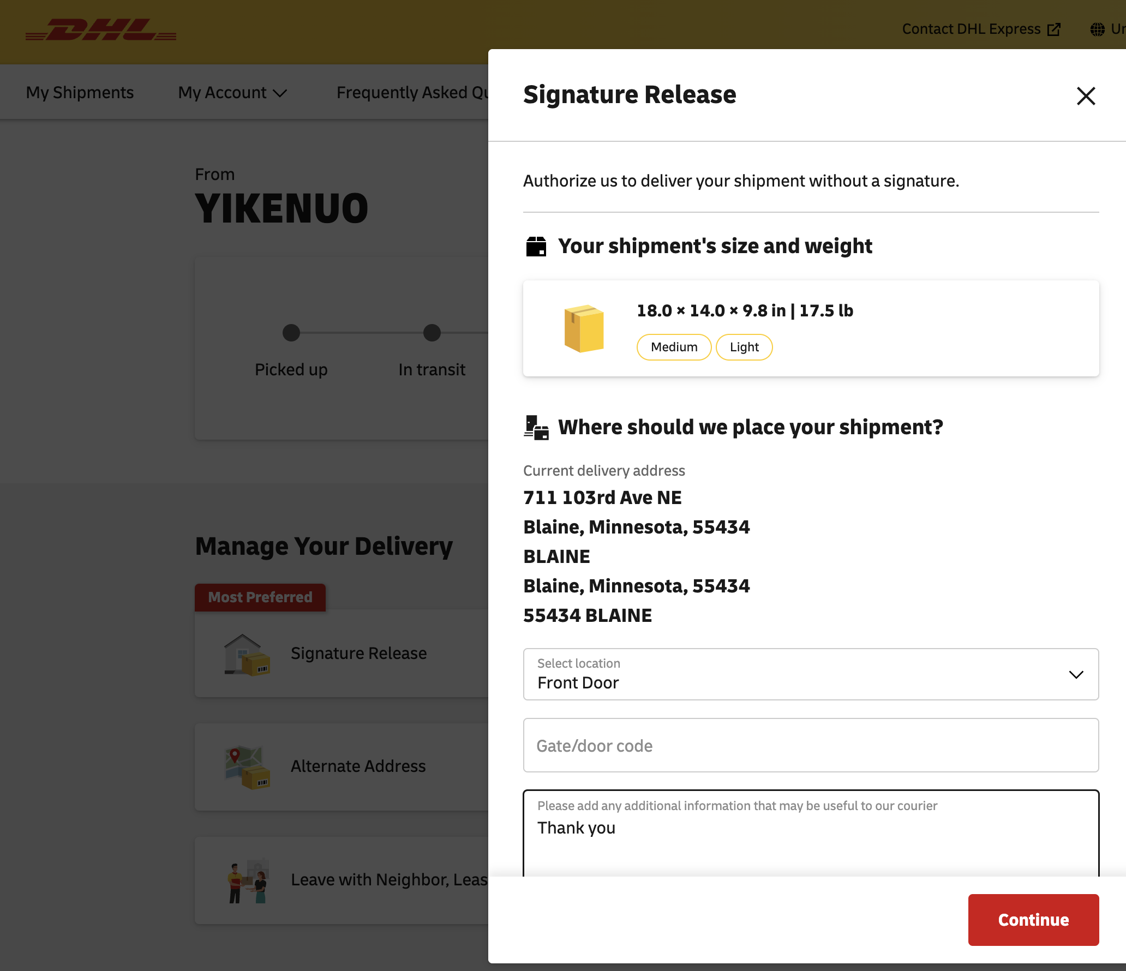
Manufacturing/Elecrow Led Array Boards/DHL Shipping size and weight.png
