ageppert/Core-64-Interactive-Core-Memory-Badge/Testing/V0.4 Battery Calibration and Runtime Test.xlsx

Sheet: Summary
V0.4 Battery Calibration and Runtime Test.xlsx
future date
TEST LOADING | Core Refresh Rate | LED Brightness
 | Hz | 0-255
Mode 0, Scrolling Text , SD Card logging | 30 | 55 | Dark
Mode 0, Scrolling Text | 30 | 155 | Indoor
Mode 0, Scrolling Text | 30 | 255 | Outside
Battery Pack Config: direct to battery header on board.
Current, scanning cores, LEDs off |  | 0.165 A | Minimum +BATT 2.9 V shows 0.13 A
Current, scanning cores, LEDs on, low brightness |  | 0.215 A | Minimum +BATT 2.9 V shows 0.15 A. 5V0 is at 2.85 and 3V3 is at 2.81.
Current, scanning cores, LEDs on, high brightness |  | 0.900 A | Minimum +BATT 2.9 V shows 0.33 A
RUN TIME |  | Battery |  |  | RPP FET |  | 5V0 REG LP3875 |  | 3V3 REG NCP176AMX330TCG
 | RUNTIME | OPEN CIRCUIT | STARTING w/load | END w/load | STARTING w/load | END w/load | STARTING w/load | END w/load | STARTING w/load | END w/load
 | Hours | V | V | V | V | V | V | V | V | V
1S 3.7 700mAh LiPo - Tenergy 2.35 (cut-off)
1S 3.7 1200 mAh LiPo - Adafruit
1S 3.7 2500 mAh LiPo - Adafruit
1S 18650 LiPo
1S 22650 LiPo
1S LiFe
ALKALINE 3x "AA" - cheap |  | 4.5
ALKALINE 4x "AAA" - cheap |  | 6.0
ALKALINE 4x "AAA" - Amazon Basics |  | 6.0
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
