ageppert/Core-64-Interactive-Core-Memory-Badge/Testing/core flip sense voltage threshold.xlsx

Calculating core sense wire threshold voltage for comparators to sense a core polarity flip.
 | Jussi Kilpelainen's shield design values |  |  |  | Andy's design values |  |  |  |  |  |  |  | Rolfe Bozier's shield design values
 |  | Ohms | Volts |  |  | Ohms | Volts |  | Volts |  | Volts |  |  | Ohms | Volts
 | V+ |  | 3.300 |  | V+ |  | 3.300 |  | 4.500 |  | 5.000 |  | V+ |  | 5.000
 | R top | 1800 |  |  | R top | 1800 |  |  |  |  |  |  | R top | 3300
 |  |  | 1.512 |  |  |  | 1.506 |  | 2.062 |  | 2.291 |  |  |  | 1.646
 | R mid | 22 | 0.022 | <- Delta V | R mid | 11 | 0.011 | <- Delta V | 0.030 | <- Delta V | 0.033 | <- Delta V | R mid | 20 | 0.020 | <- Delta V
 |  |  | 1.490 |  |  |  | 1.495 |  | 2.032 |  | 2.258 |  |  |  | 1.626
 | R bot | 1500 |  |  | R bot | 1500 |  |  |  |  |  |  | R bot | 1600
 | Gnd |  | 0.000 |  | Gnd |  | 0.000 |  | 0.000 |  | 0.000 |  | Gnd |  | 0.000
 | R total | 3322 |  |  | R total | 3311 |  |  |  |  |  |  | R total | 4920
