ageppert/Core-64-Interactive-Core-Memory-Badge/Testing/V0.2 Battery Calibration and Runtime Test.xlsx

Sheet: Summary
V0.2 Battery Calibration and Runtime Test.xlsx
2020-03-09
Mode 0, Scrolling Text, OLED on, heartbeat LED on 90%
Battery Pack Config: Long wires, spring clip case, ammeter in series
Current is 95-110 mA
MAX VOLTAGE | 4.13
MIN VOLTAGE | 3
ALKALINE 3x "AAA"
RUN TIME (hrs) | 6
MAX | 4.2 | First few minutes shows misbehaving pixels, but it quickly settles to 4.125 V and works well from there.
MIN | 3.2
ALKALINE 3x "AA"
RUN TIME (hrs) | 14
MAX | 4.16
MIN | 3.08
1S LiPo 700 mAh Tenergy
RUN TIME (hrs) | 4.5
MAX | 4.09
MIN | 3 | Falls off the bottom voltage QUICKLY

Sheet: Calibration
Calibration
2020-03-09
During Mode 0, scrolling text
Firmware: 200331 (this was entered wrong in the firmware, should have been 20020303)
Radio Shack Multimeter across Bat- and VSW
Adjustable Power Supply
Actual (V) | OLED Displayed (V) | Error Delta | Error % | Notes
4.130 | 4.309 | 0.179 | 4.3% | Highest operating voltage before pixels get spastic
4.000 | 4.142 | 0.142 | 3.6%
4.010 | 4.209 | 0.199 | 5.0%
3.990 | 4.162 | 0.172 | 4.3%
3.715 |  |  |  | Half way between max voltage and minimum accurate voltage
3.600 | 3.763 | 0.163 | 4.5%
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
