ageppert/Core-64-Interactive-Core-Memory-Badge/Testing/V0.3 Battery Calibration and Runtime Test.xlsx

Sheet: Summary
V0.3 Battery Calibration and Runtime Test.xlsx
2020-08-13
Mode 0, Scrolling Text (SLOWLY! Because I2C IO Expanders are slow), OLED on, heartbeat LED, logging voltage to SD Card every ~3s, auto brightness relatively low
Battery Pack Config: direct to battery header on board.
Current is probably ABOUT 95-110 mA
MAX VOLTAGE | 4.13
MIN VOLTAGE | 3
ALKALINE 3x "AAA"
RUN TIME (hrs)
MAX
MIN
ALKALINE 3x "AA"
RUN TIME (hrs)
MAX
MIN
1S LiPo 700 mAh Tenergy
RUN TIME (hrs) | 5
MAX | 4
MIN | 2.35 | Falls off the bottom voltage QUICKLY, and cut-off is at 2.35 V internal to the cell.

Sheet: Calibration
Calibration
USING SAME SCALAR FROM V0.2 | 6.366 | New scalar to be. CONFIRMED.
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
