ageppert/Core-64-Interactive-Core-Memory-Badge/Documentation/Software Block Diagram.pdf

# Core 64: Software Block Diagram

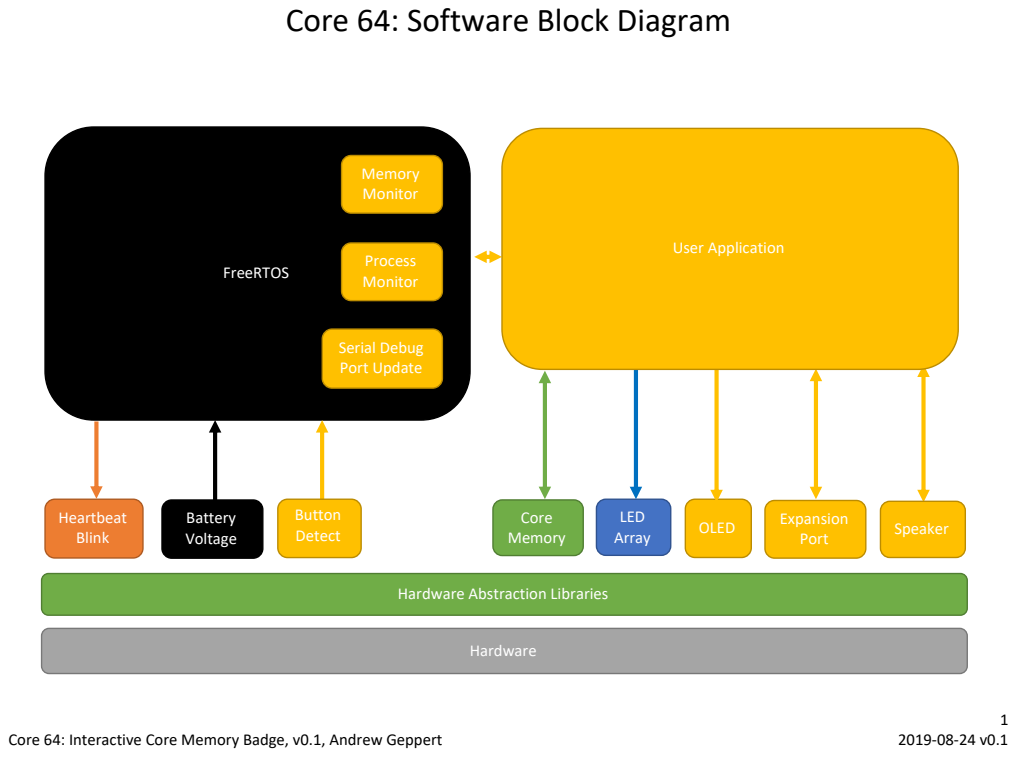
[picture p75: page 1]
Core 64: Interactive Core Memory Badge, v0.1, Andrew Geppert; LED Array; FreeRTOS; Core; Memory; OLED; Expansion; Port; Heartbeat Blink; Serial Debug Port Update; Hardware; Process Monitor; Memory Monitor; Speaker Battery Voltage; Button Detect; User Application

Hardware Abstraction Libraries
