ageppert/Core-64-Interactive-Core-Memory-Badge/Documentation/Electrical Block Diagram.pdf

# Electrical Block Diagram

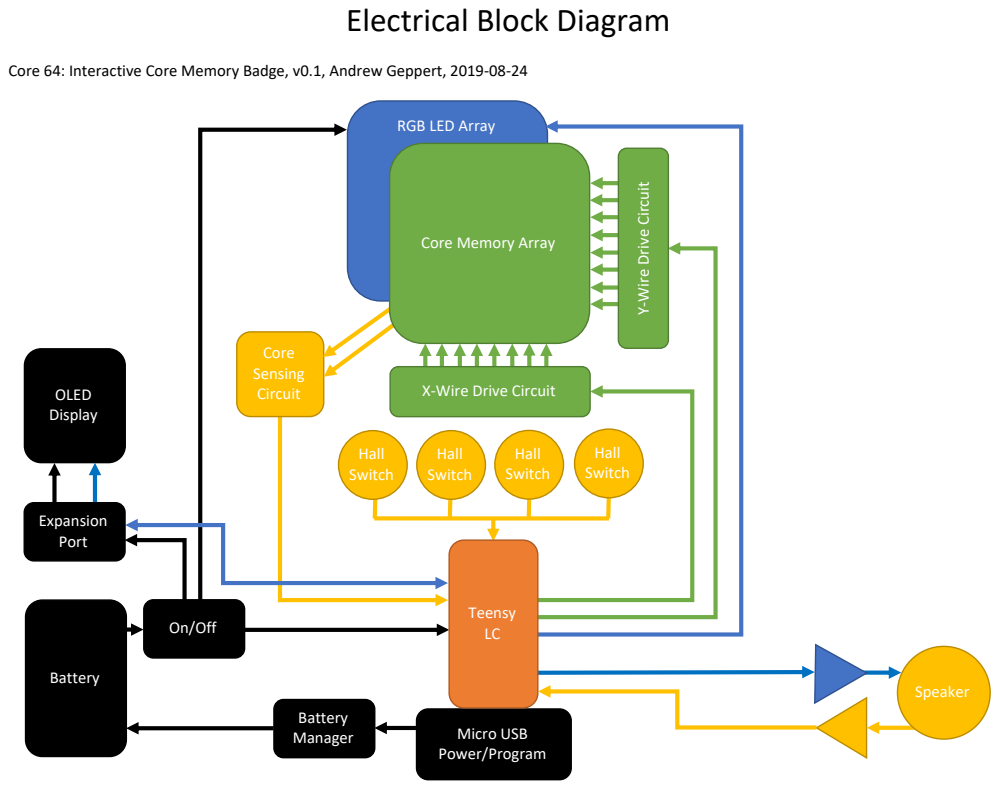
[picture p76: page 1]
Hall Switch; Battery; Manager; Micro USB; Power/Program; Core Sensing Circuit; OLED Display; Expansion Port; Speaker; Teensy; On/Off

Core 64: Interactive Core Memory Badge, v0.1, Andrew Geppert, 2019-08-24

RGB LED Array

Y-Wire Drive Circuit

Core Memory Array

X-Wire Drive Circuit
