ageppert/Core-64-Interactive-Core-Memory-Badge/Electronic Design/Interactive Core Memory Badge (Logic) v0.3/Core 64 v0.3 Logic PCB Front.pdf

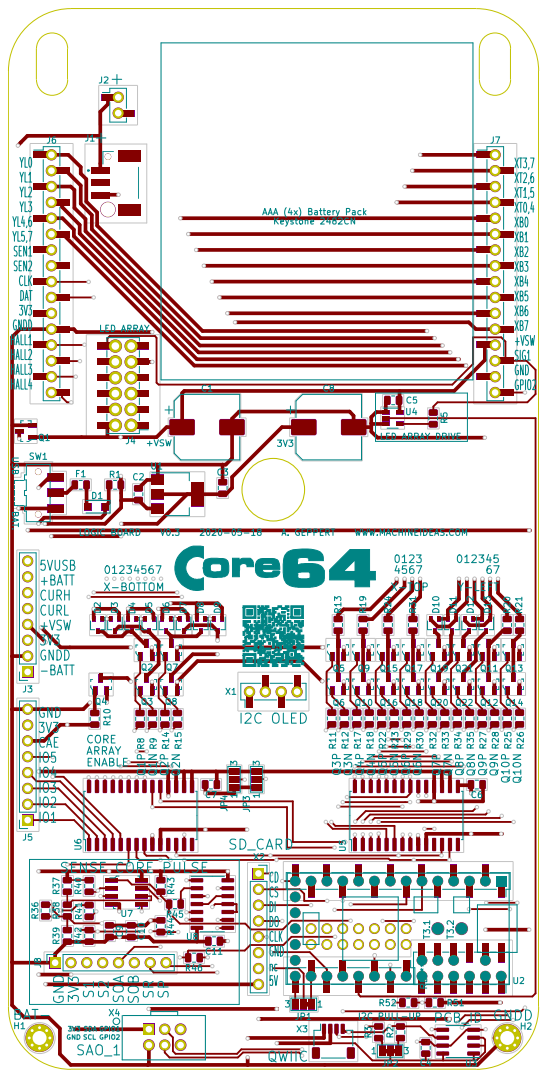
[picture p93: page 1]
