ageppert/Core-64-Interactive-Core-Memory-Badge/Electronic Design/Interactive Core Memory Badge (Cores) v0.3/Core 64 v0.3 Core PCB FRONT.pdf

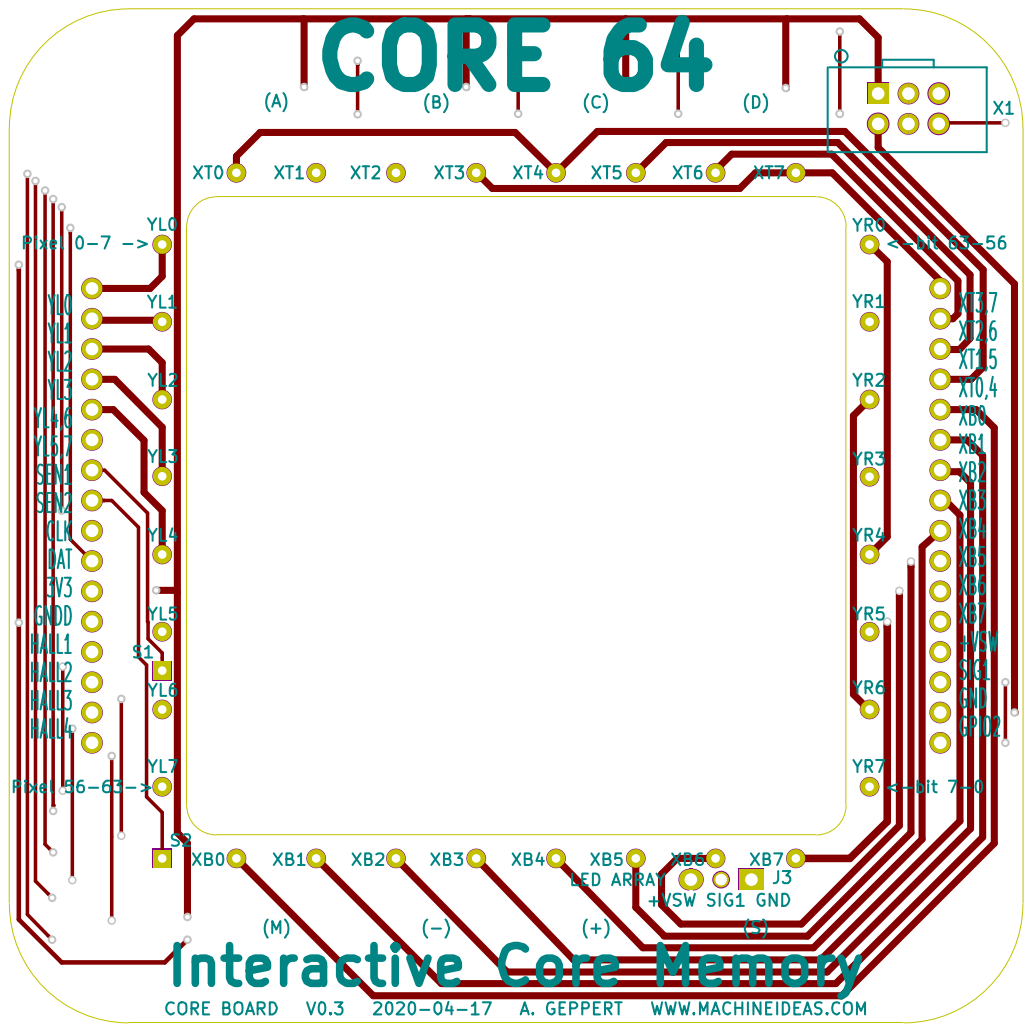
[picture p95: page 1]
