ageppert/Core-64-Interactive-Core-Memory-Badge/Electronic Design/Interactive Core Memory Badge (Cores) v0.3/Core Board V0.3 Schematic as prototyped.pdf

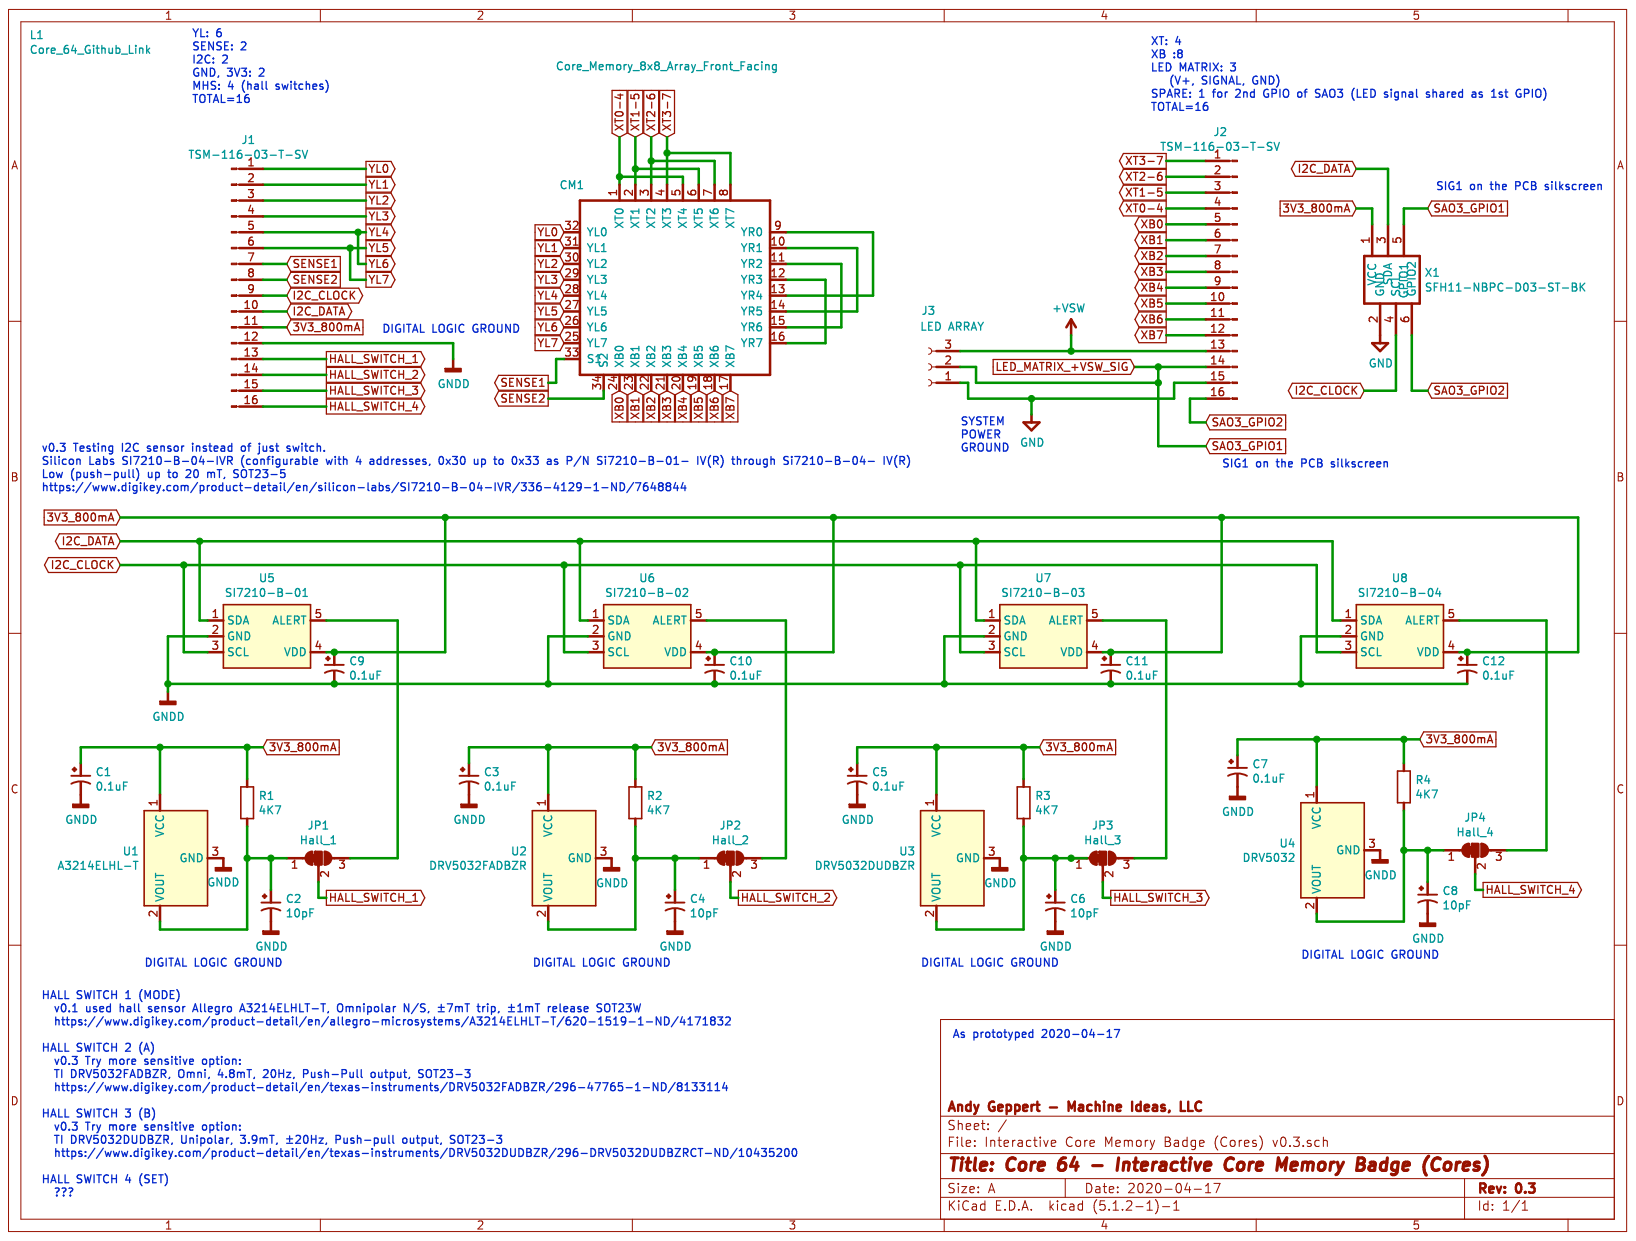
[picture p96: page 1]
