ageppert/Core-64-Interactive-Core-Memory-Badge/Electronic Design/Interactive Core Memory Badge (Cores) v0.3/Interactive Core Memory Badge (Cores) v0.3 PCB.pdf

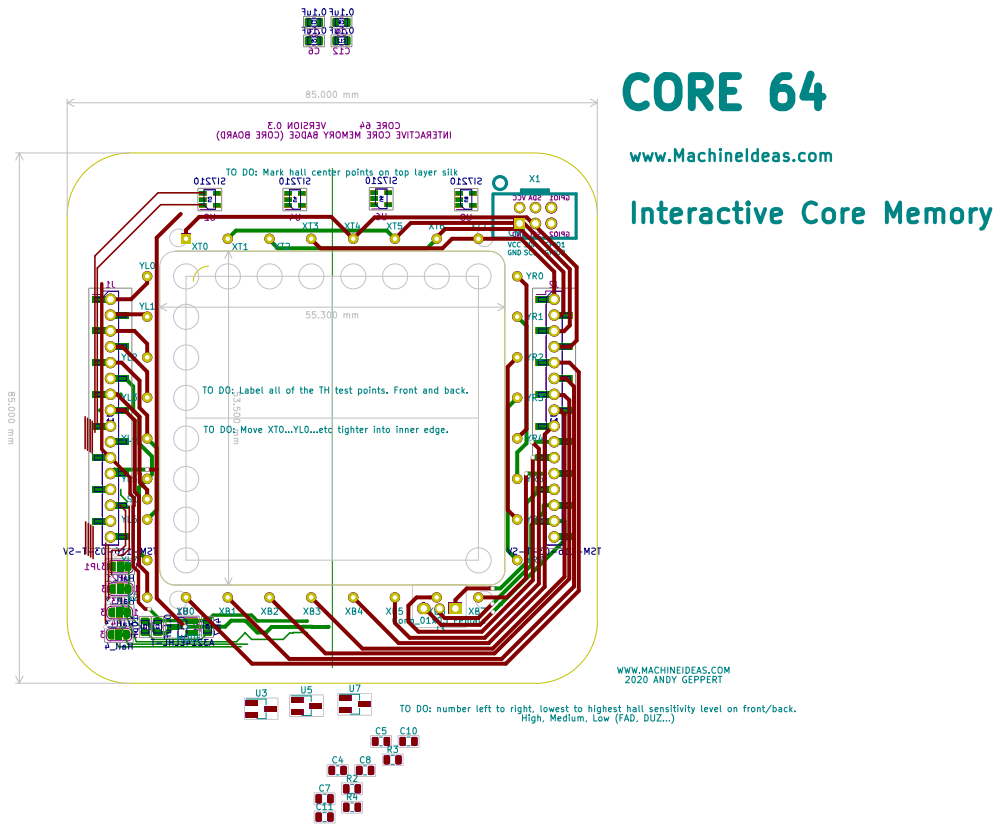
[picture p97: page 1]
