ageppert/Core-64-Interactive-Core-Memory-Badge/Electronic Design/Core64 CB v1.0/Core64 CB V1.0 Schematic Production Release 2022-06-02.pdf

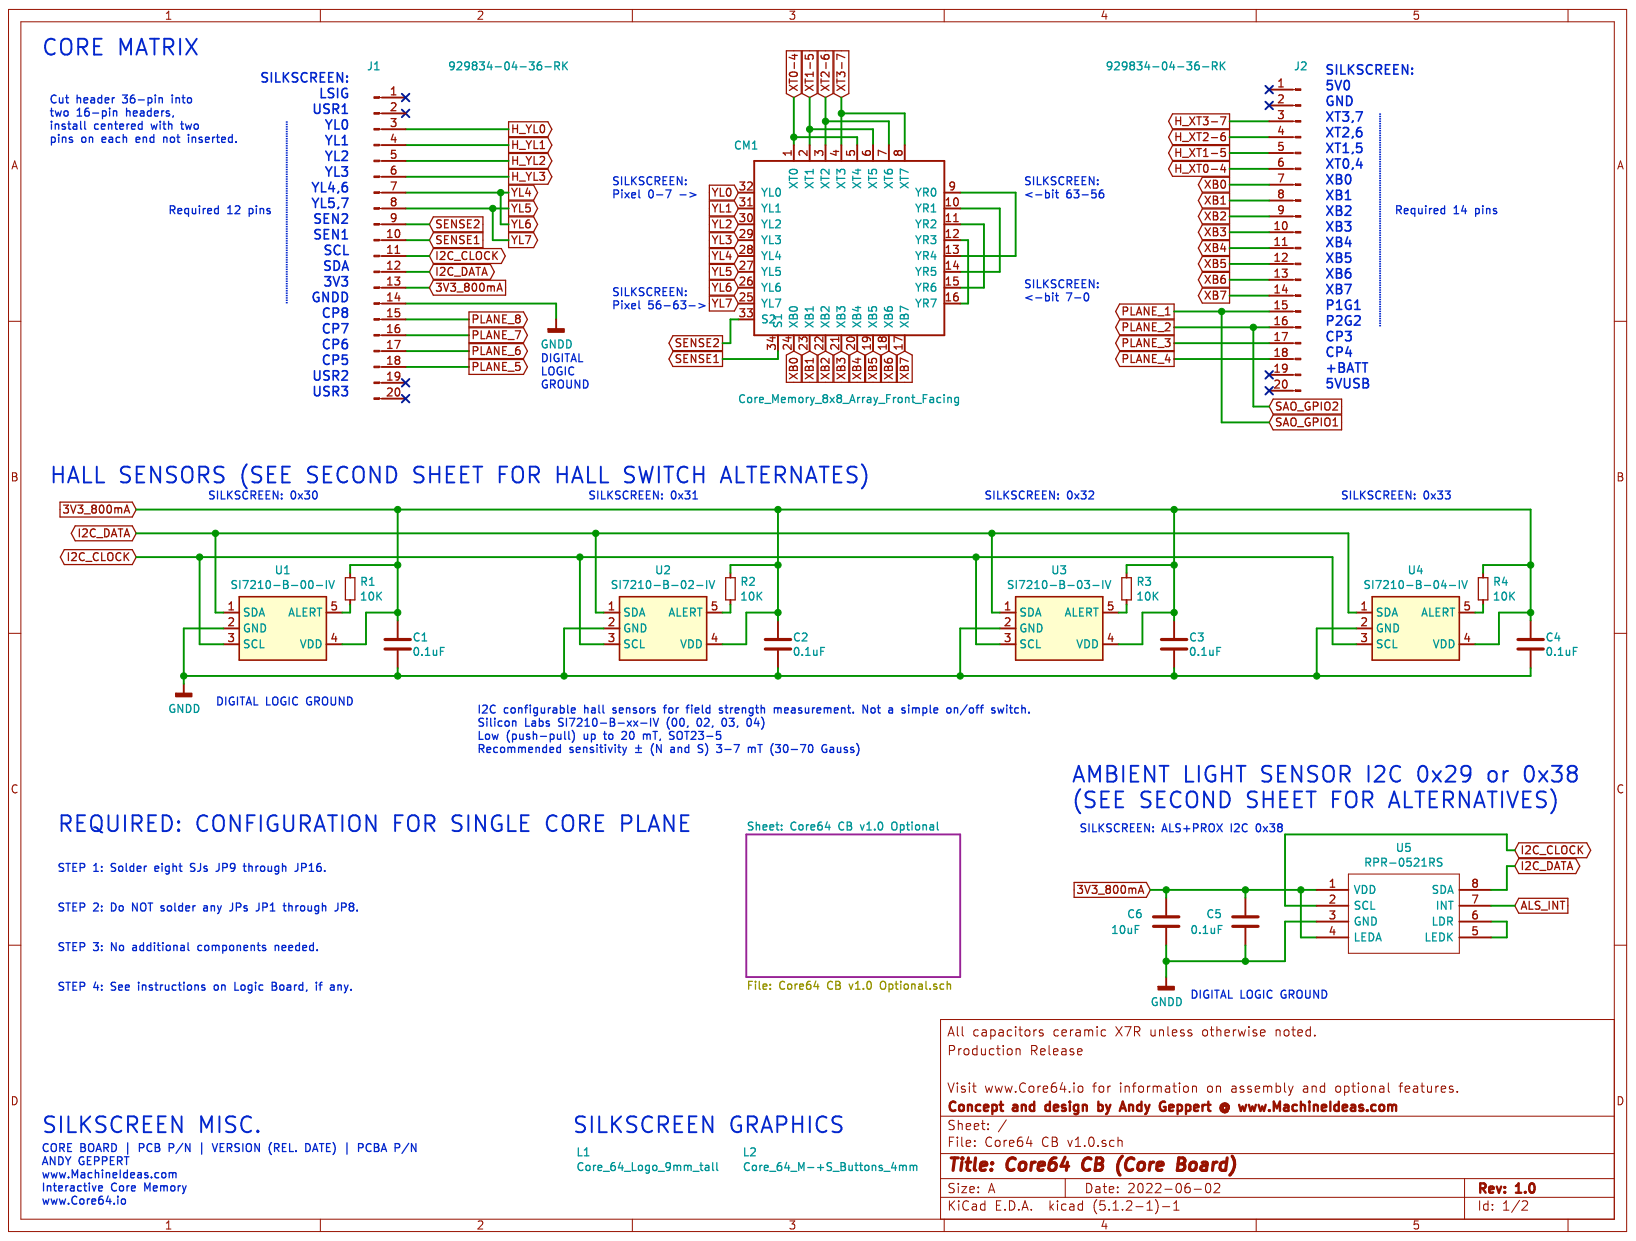
[picture p99: page 1]

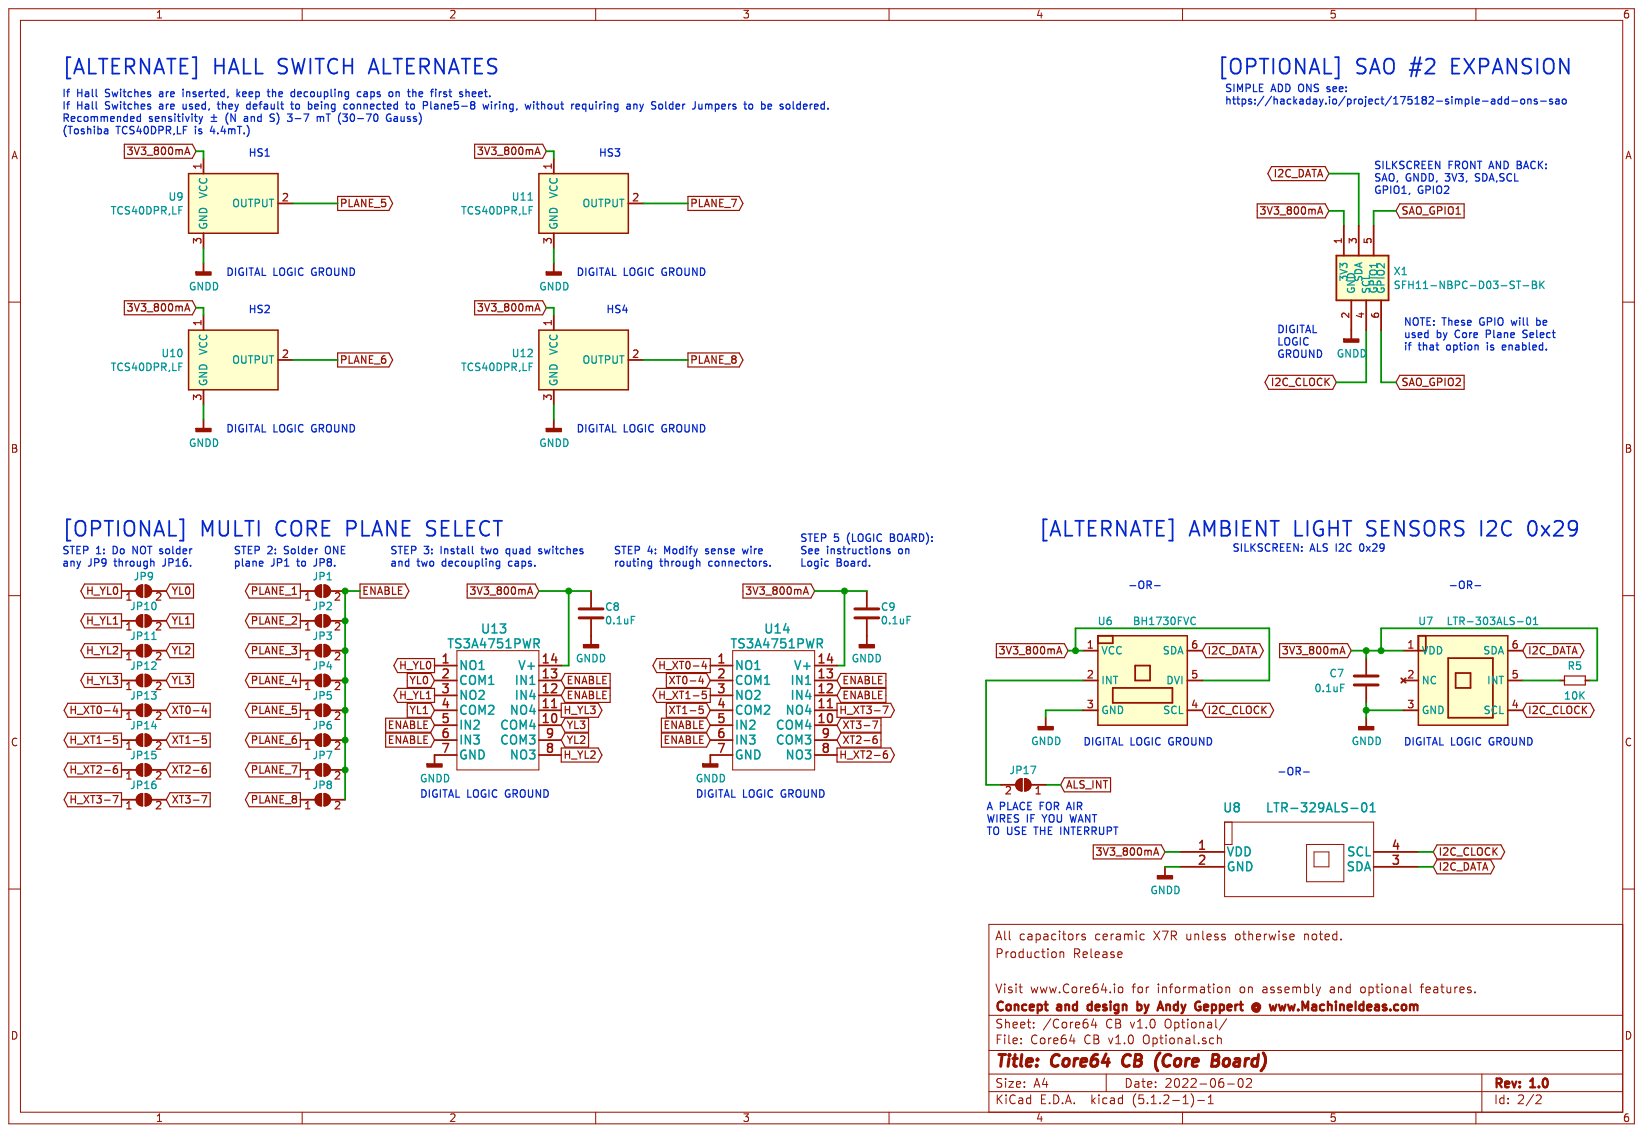
[picture p100: page 2]
