ageppert/Core-64-Interactive-Core-Memory-Badge/Electronic Design/Core64 CB v0.6/Core64 CB v0.6 Schematic.pdf

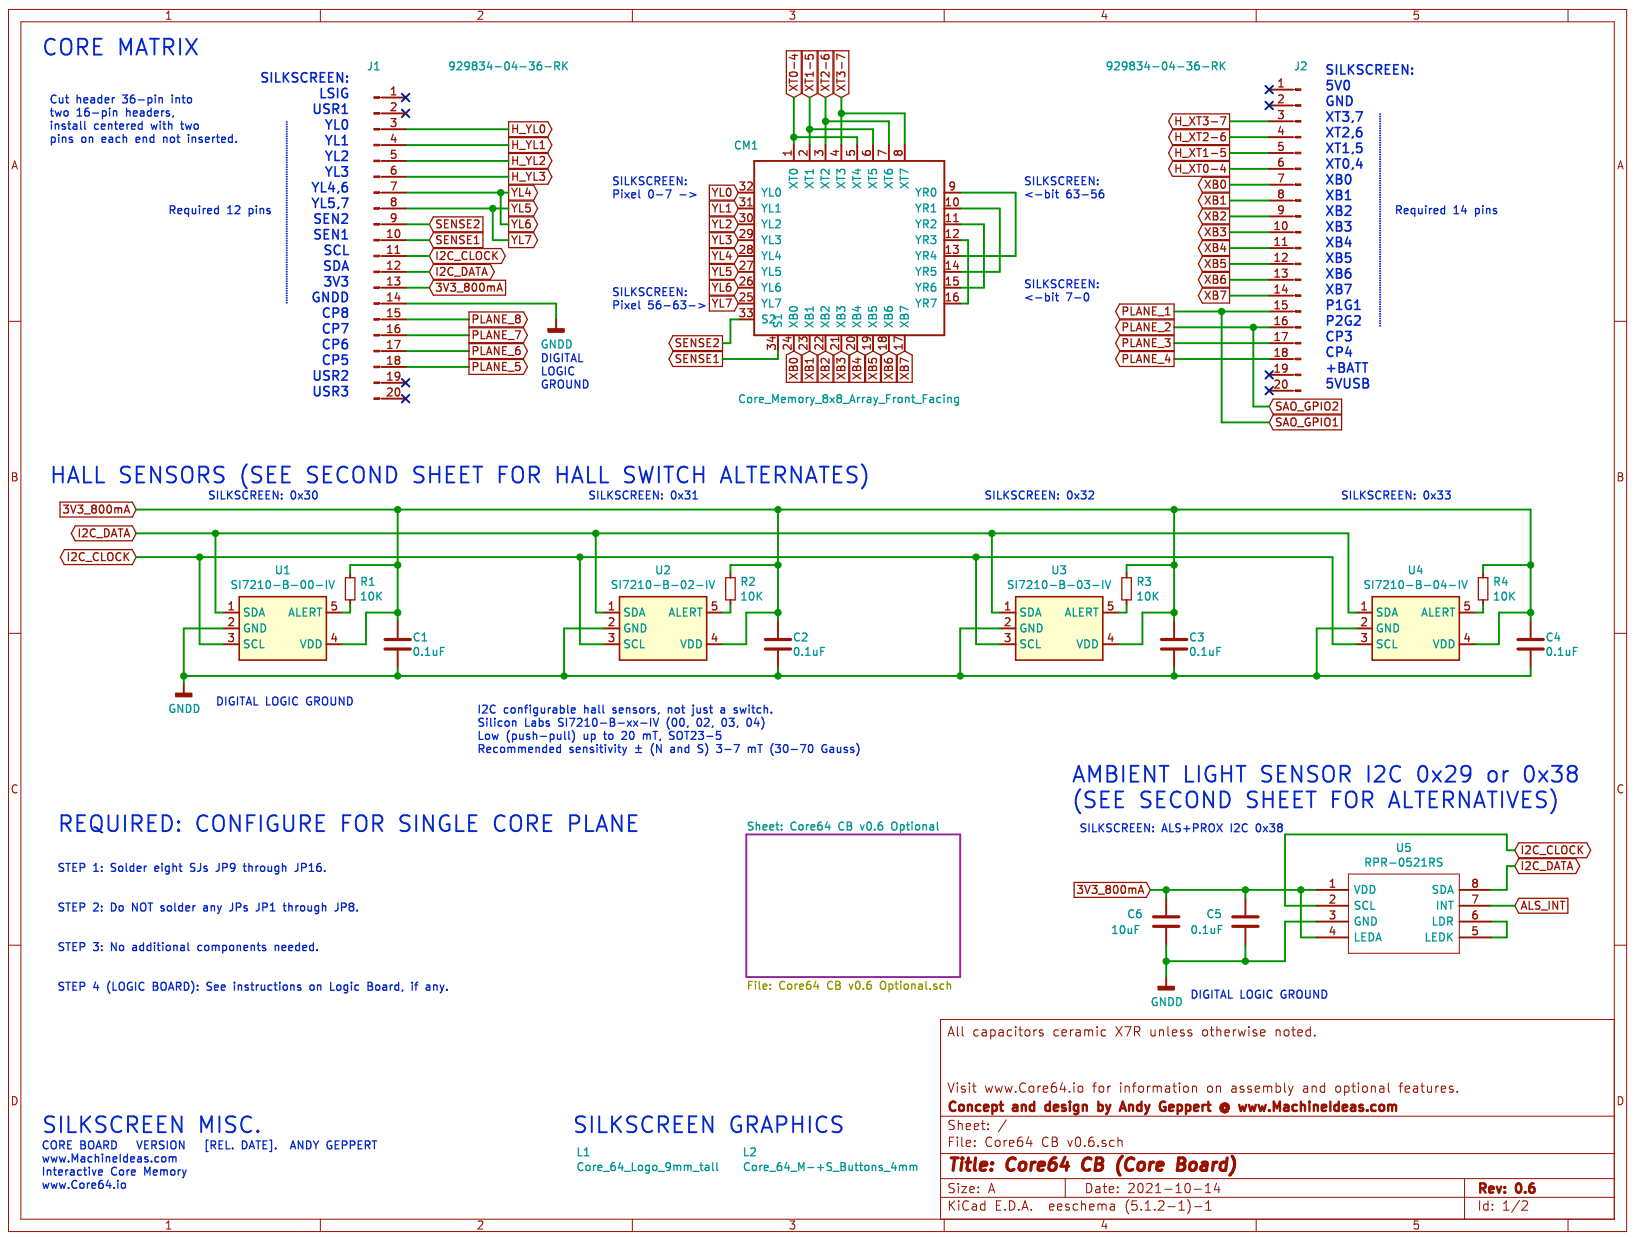
[picture p101: page 1]

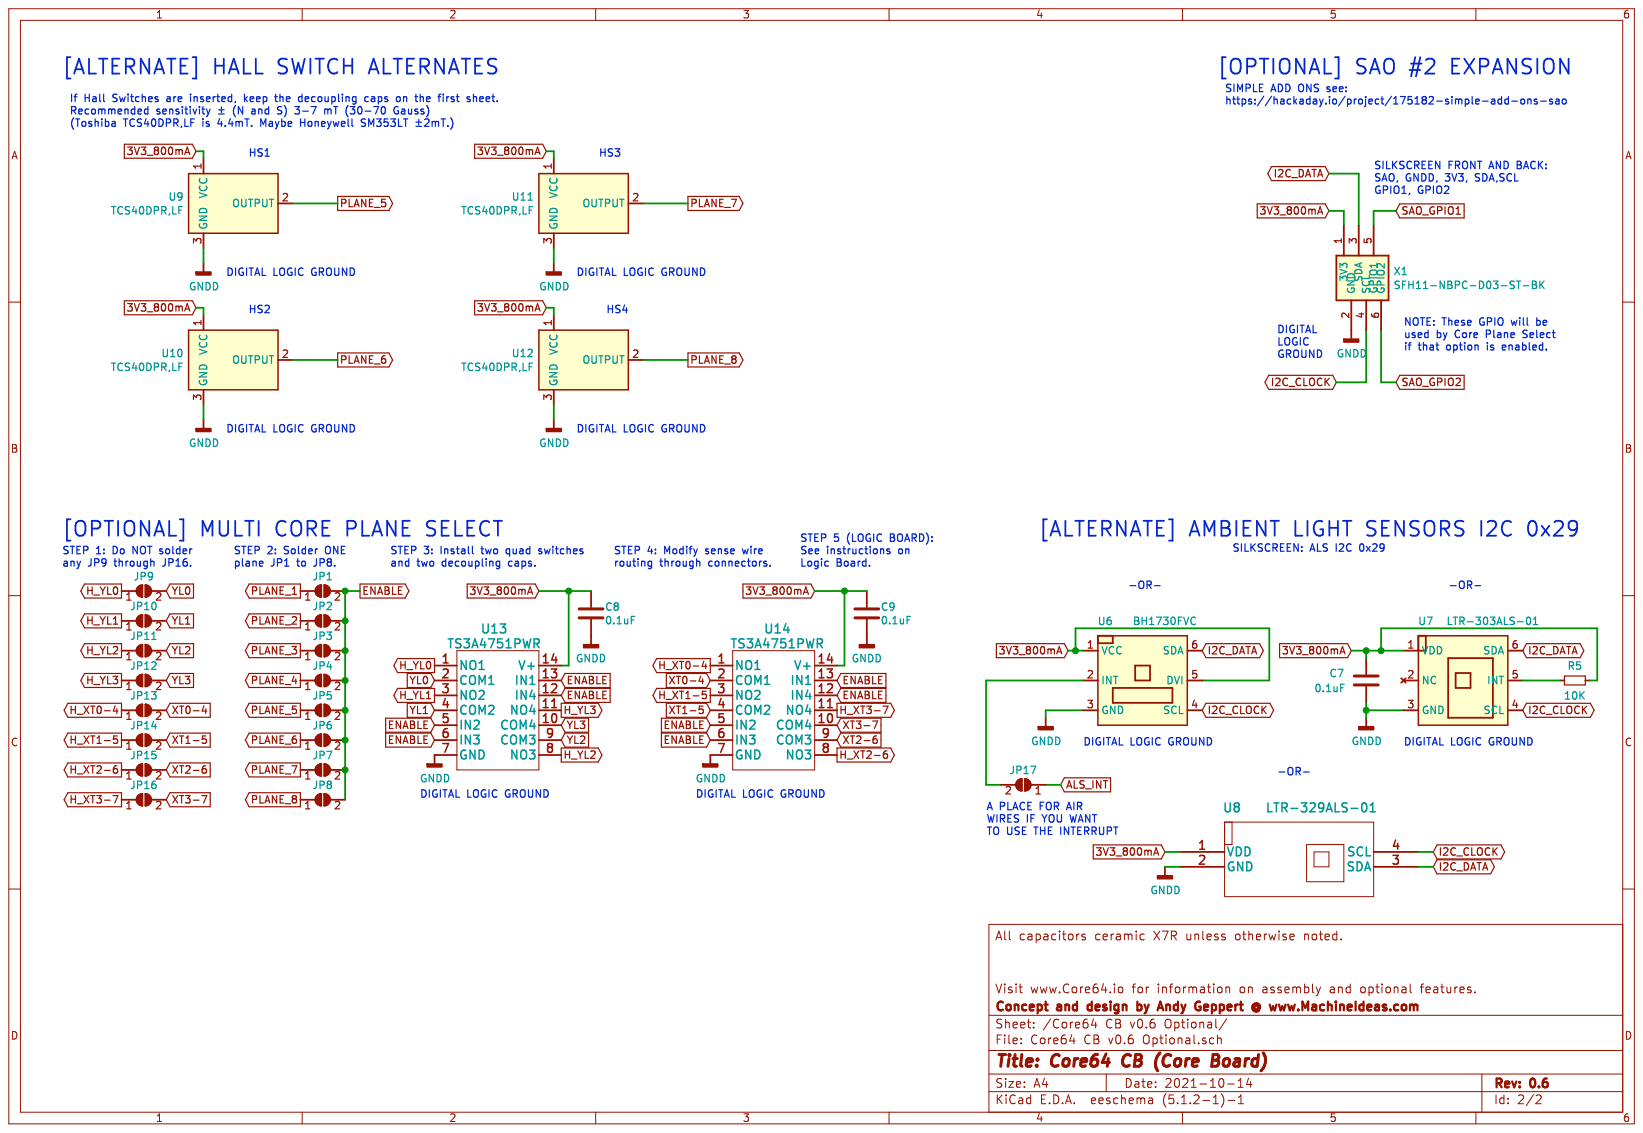
[picture p102: page 2]
