ageppert/Core-64-Interactive-Core-Memory-Badge/Electronic Design/Core64 LM v0.3/Core64 LM v0.3 Schematic (As Fabricated).pdf

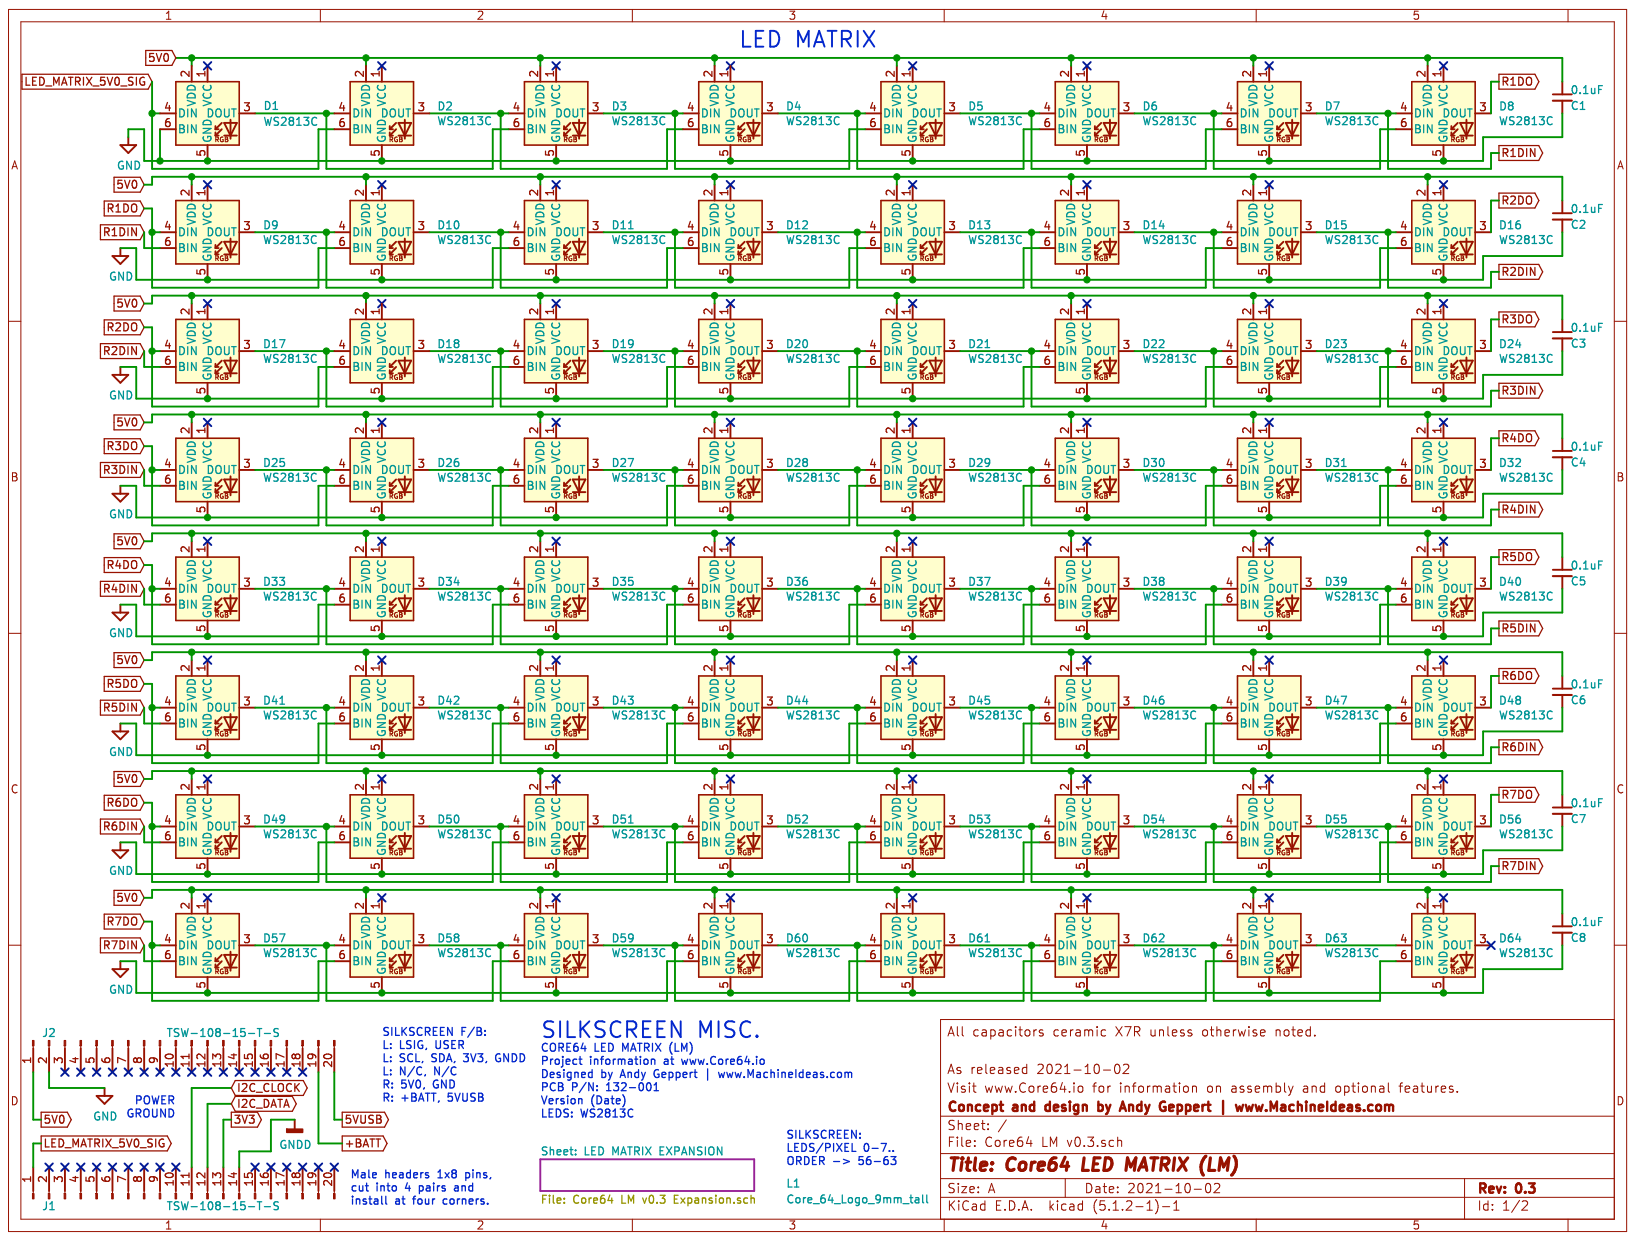
[picture p103: page 1]

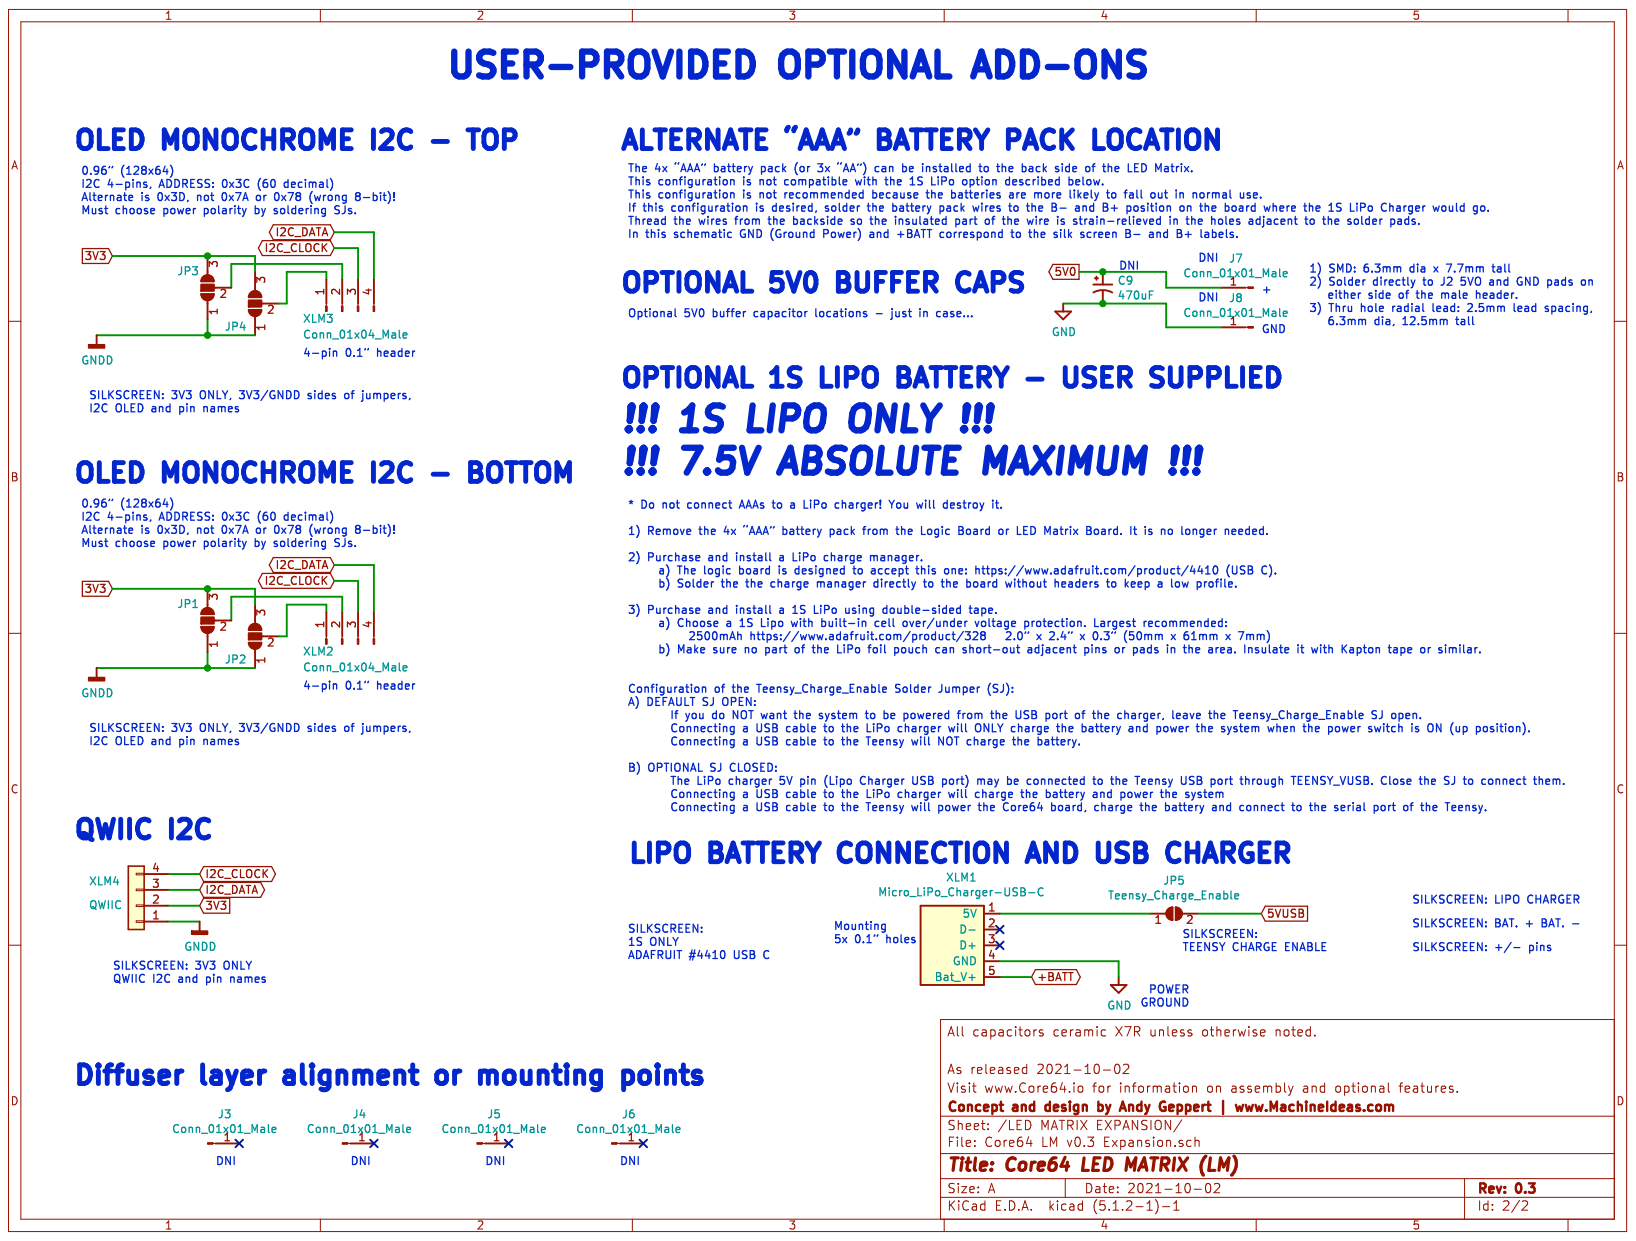
[picture p104: page 2]
