ageppert/Core-64-Interactive-Core-Memory-Badge/Electronic Design/Core64 LM v0.2/Core64 LM v0.2 Schematic as prototyped 2021-03-21.pdf

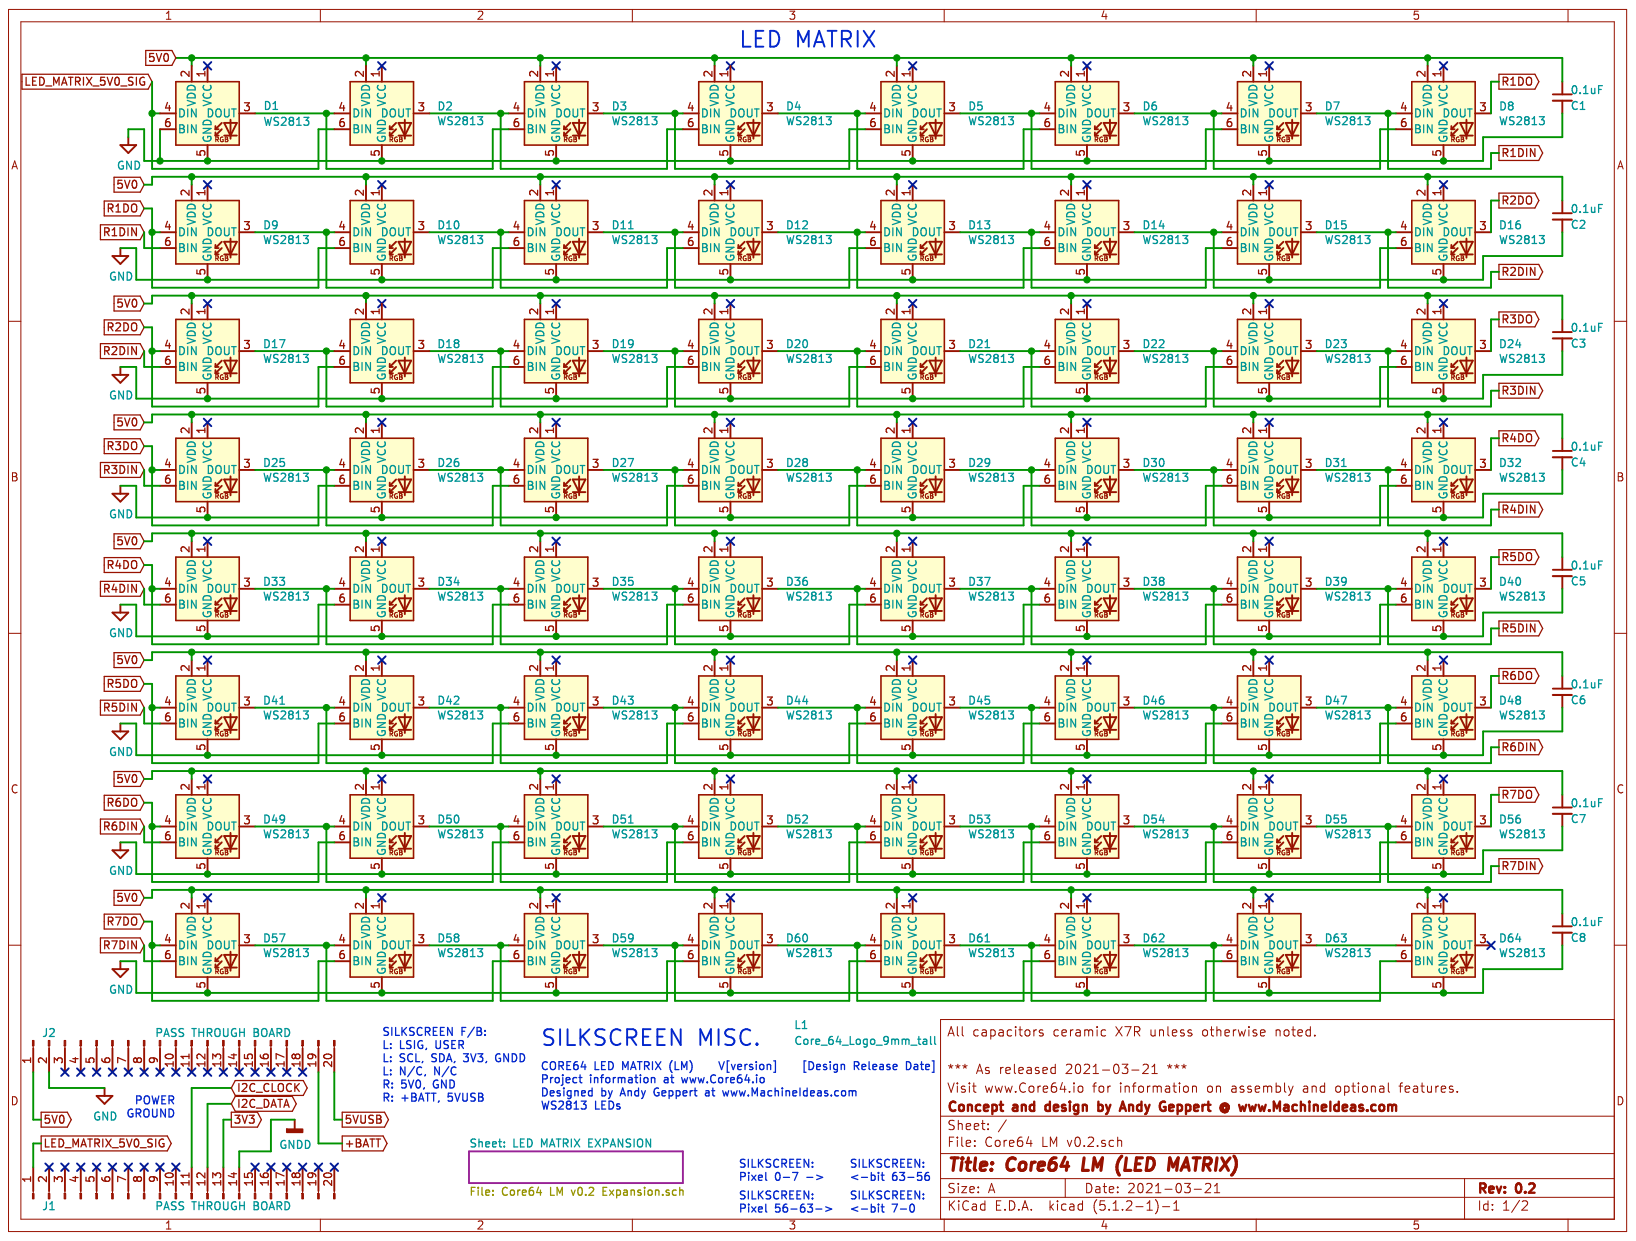
[picture p105: page 1]

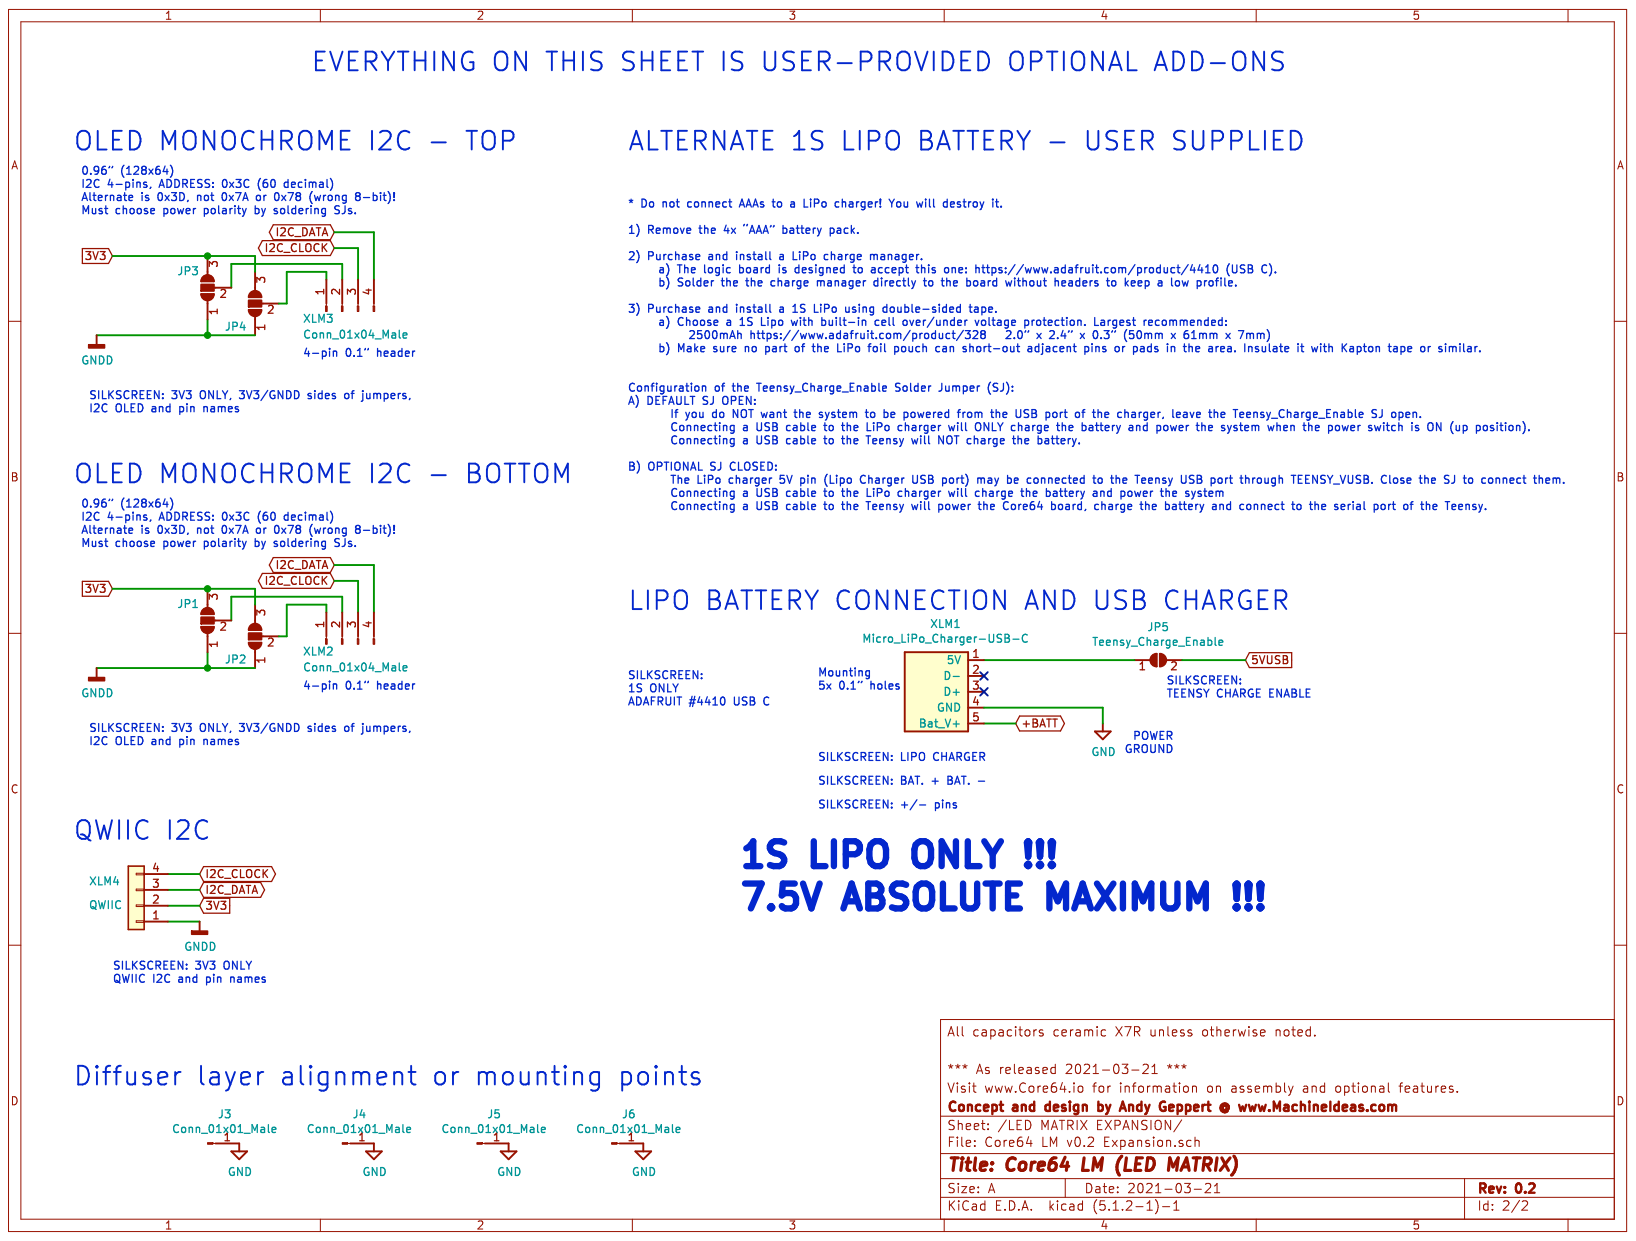
[picture p106: page 2]
