ageppert/Core-64-Interactive-Core-Memory-Badge/Electronic Design/Core64 CB v0.5/Core64 CB v0.5 Schematic 2021-02-28 as prototyped.pdf

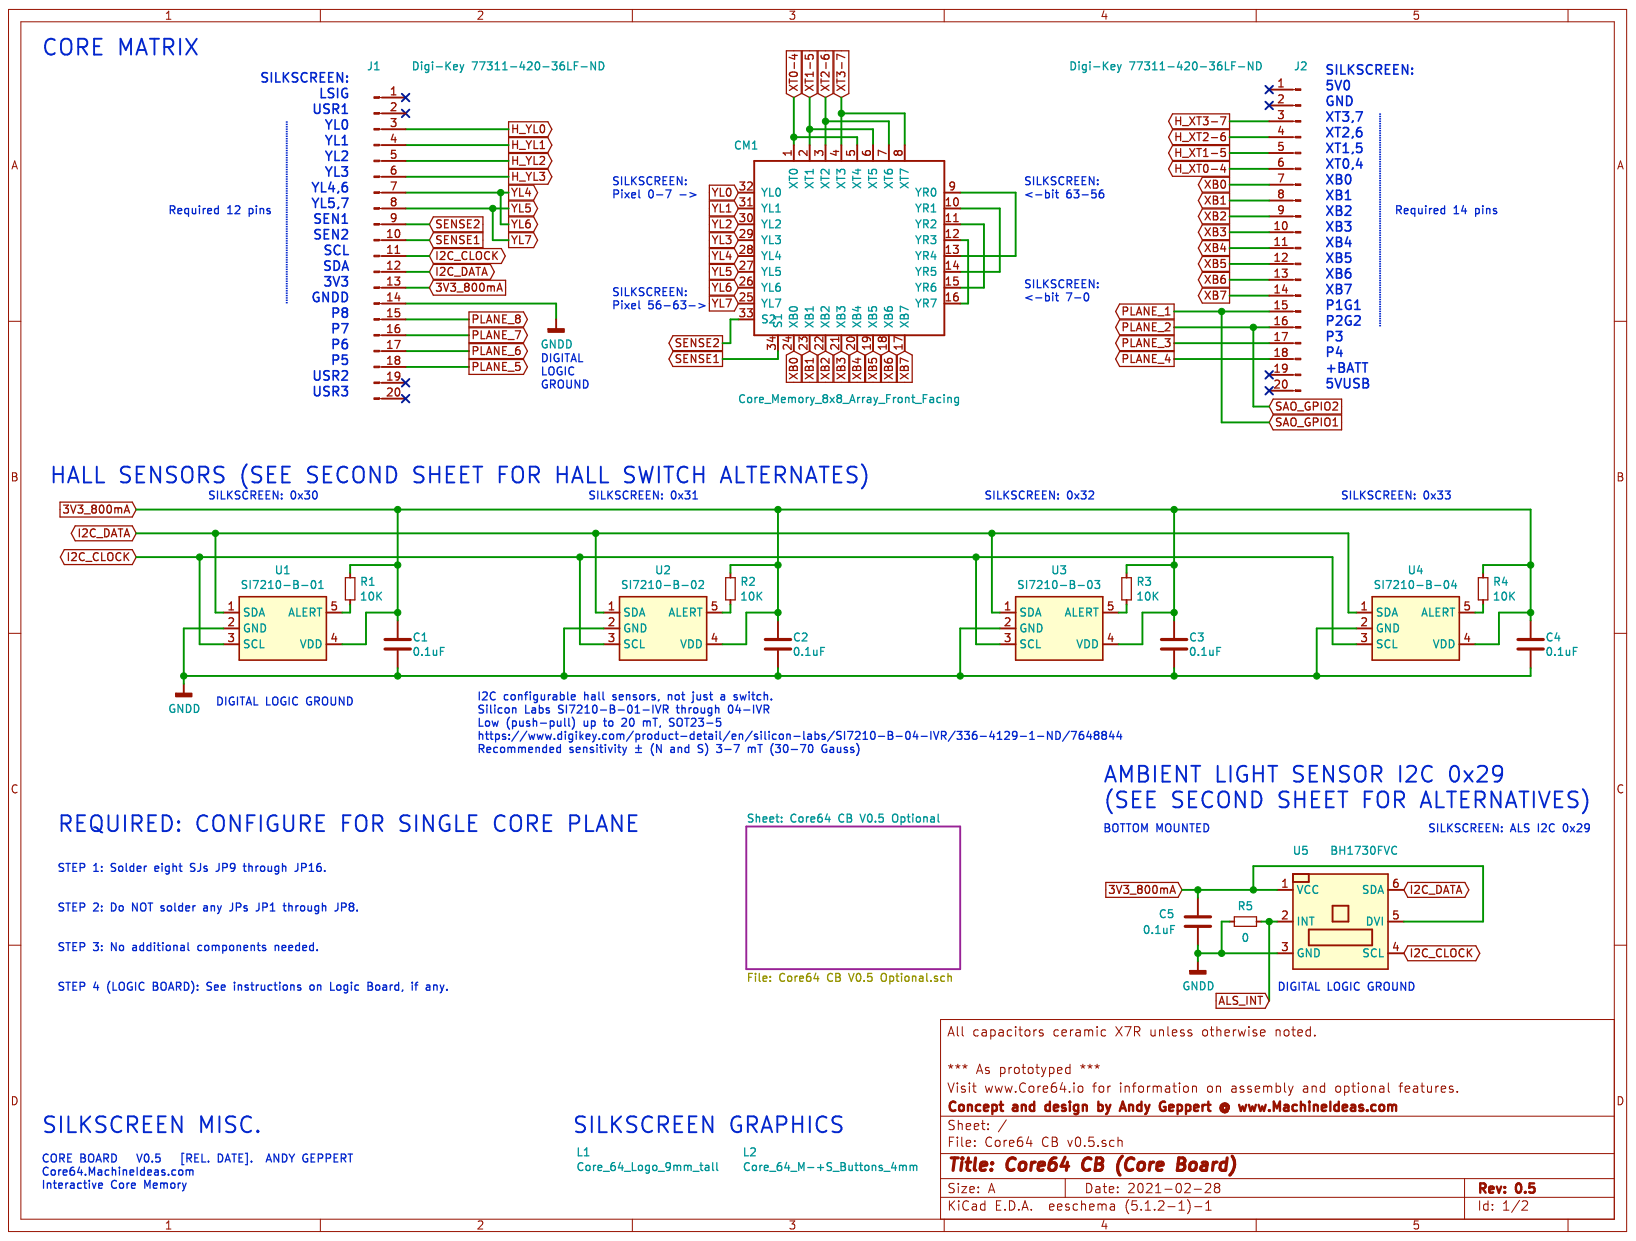
[picture p107: page 1]

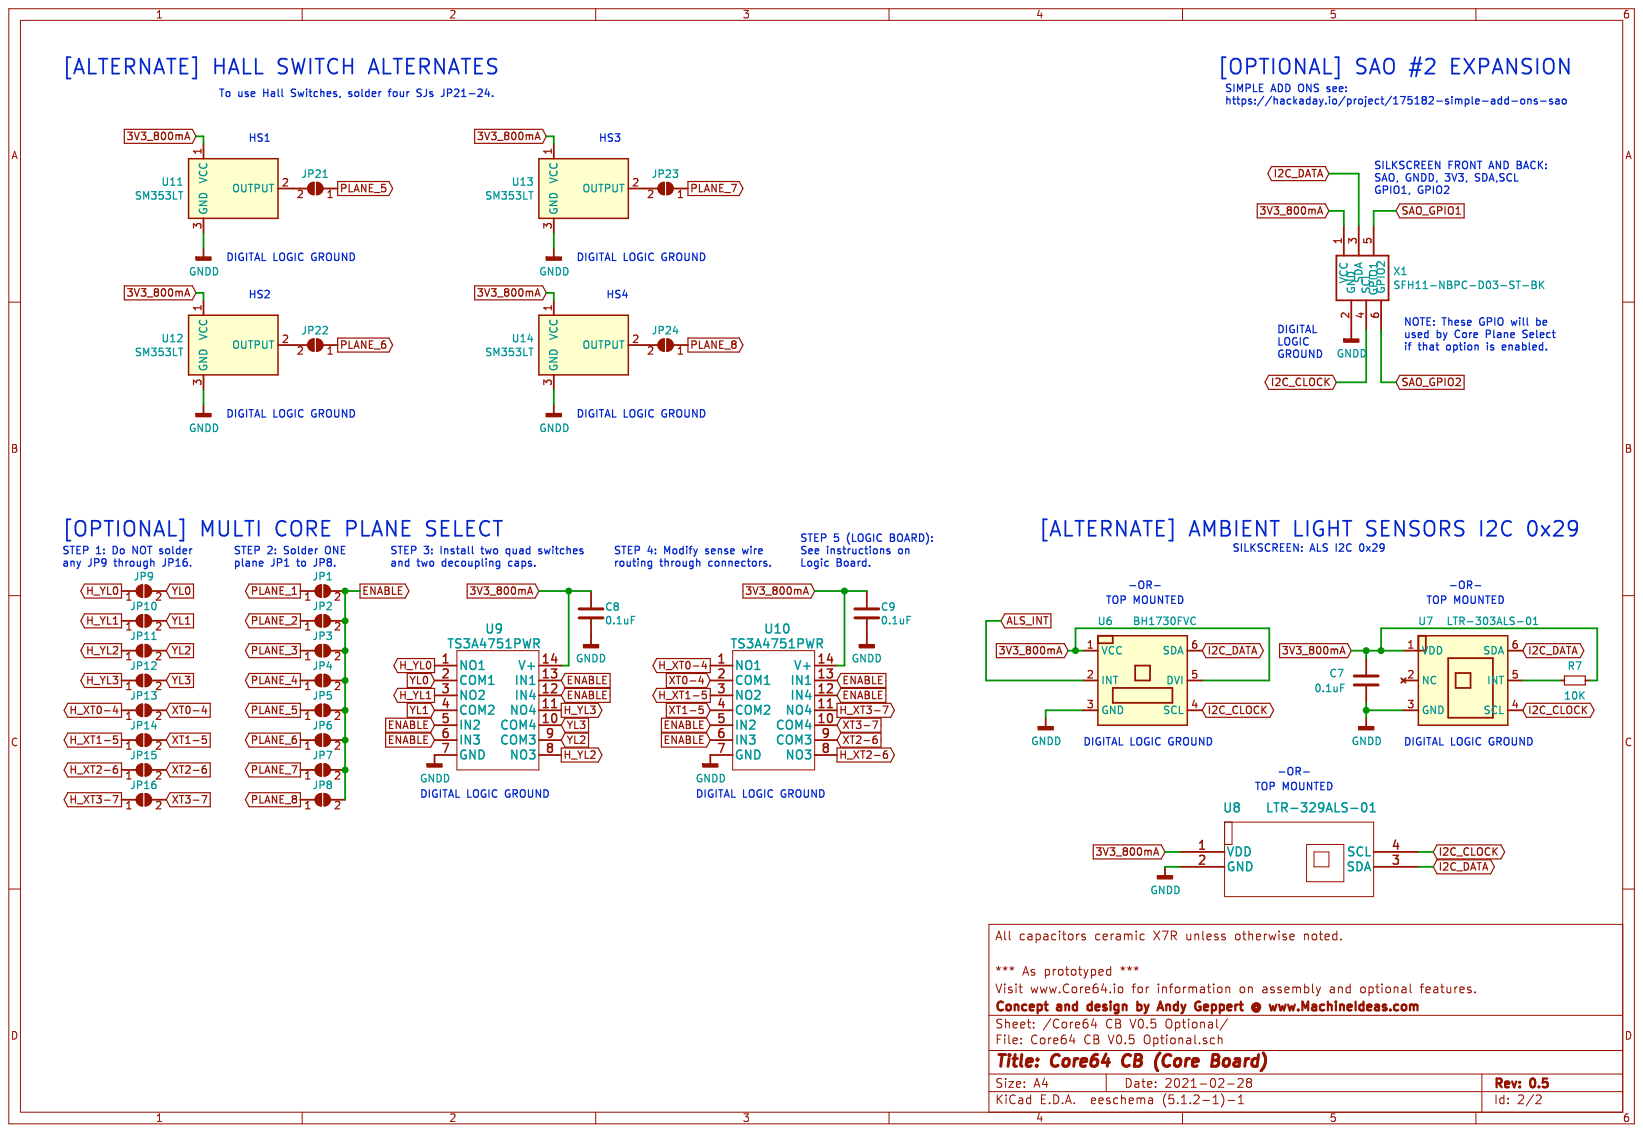
[picture p108: page 2]
