ageppert/Core-64-Interactive-Core-Memory-Badge/Electronic Design/Core64 LB v0.5/Core64 LB v0.5 Schematic 2021-02-27 as prototyped.pdf

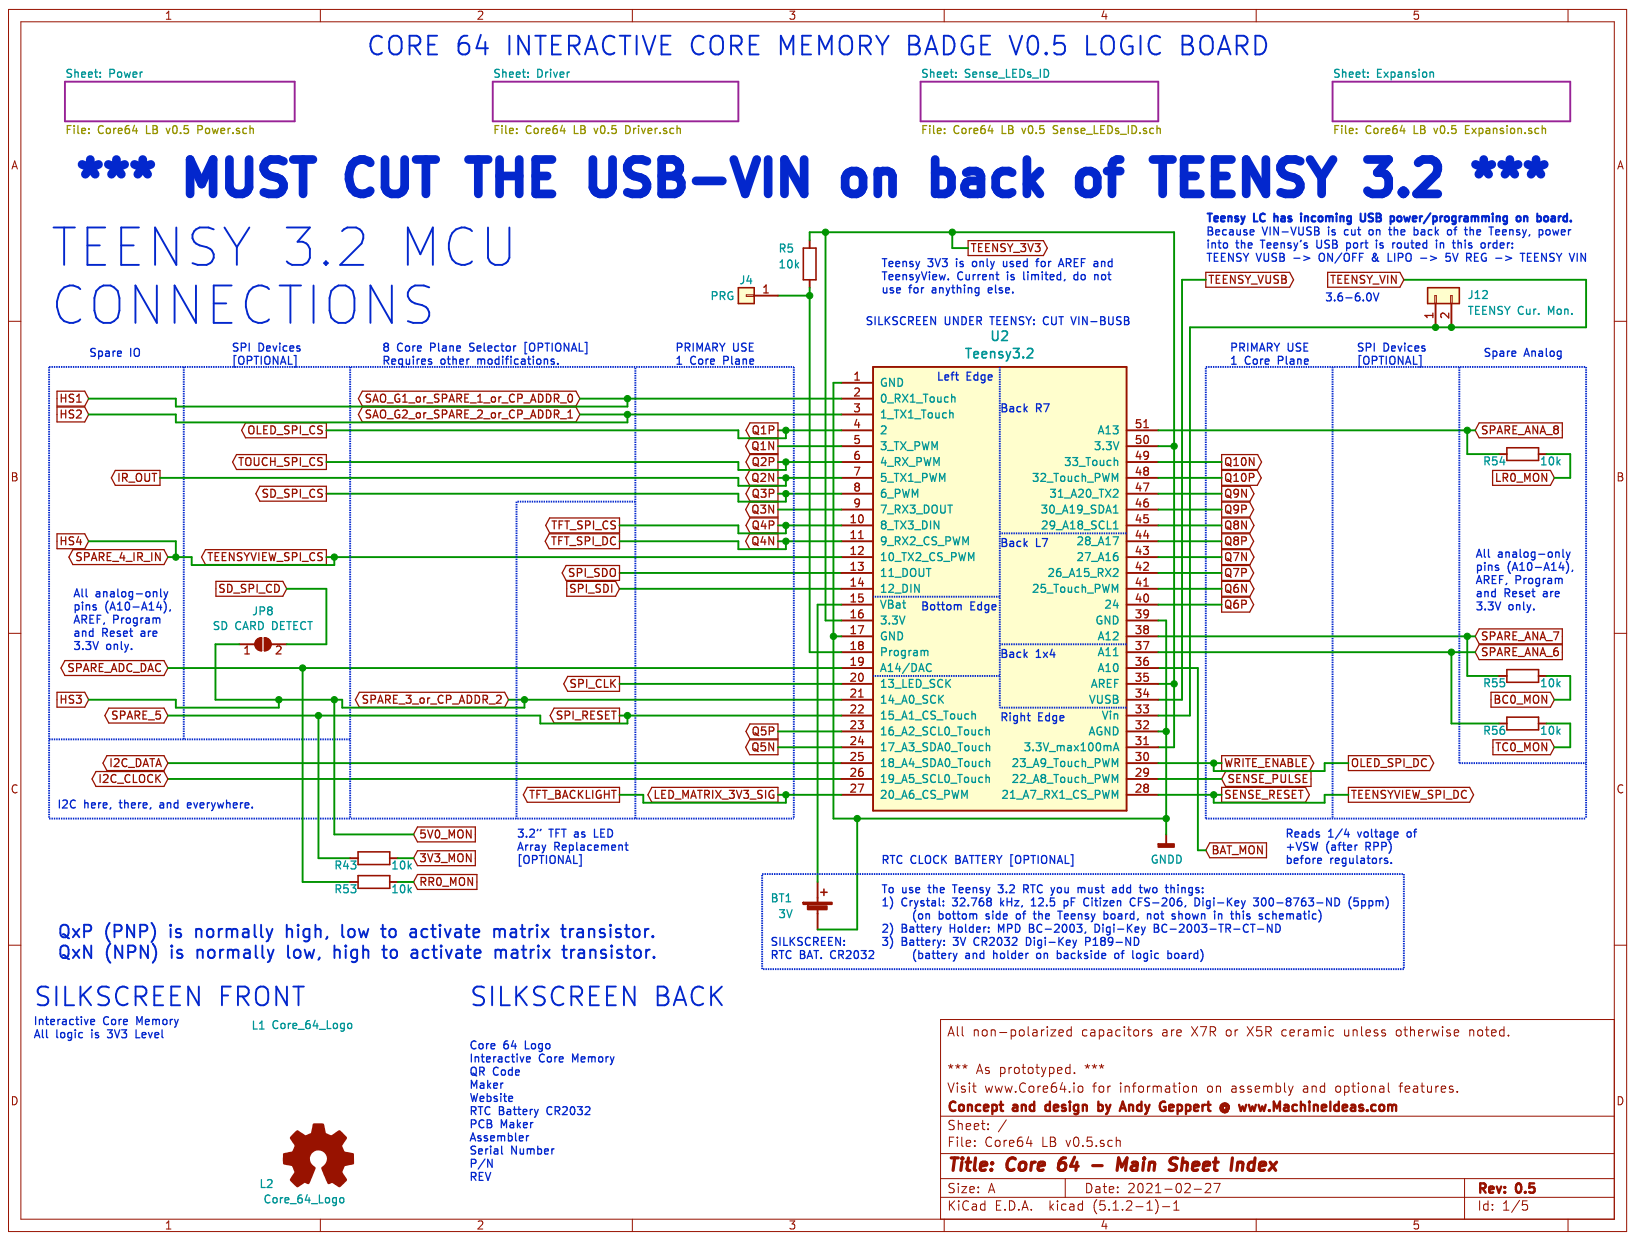
[picture p109: page 1]

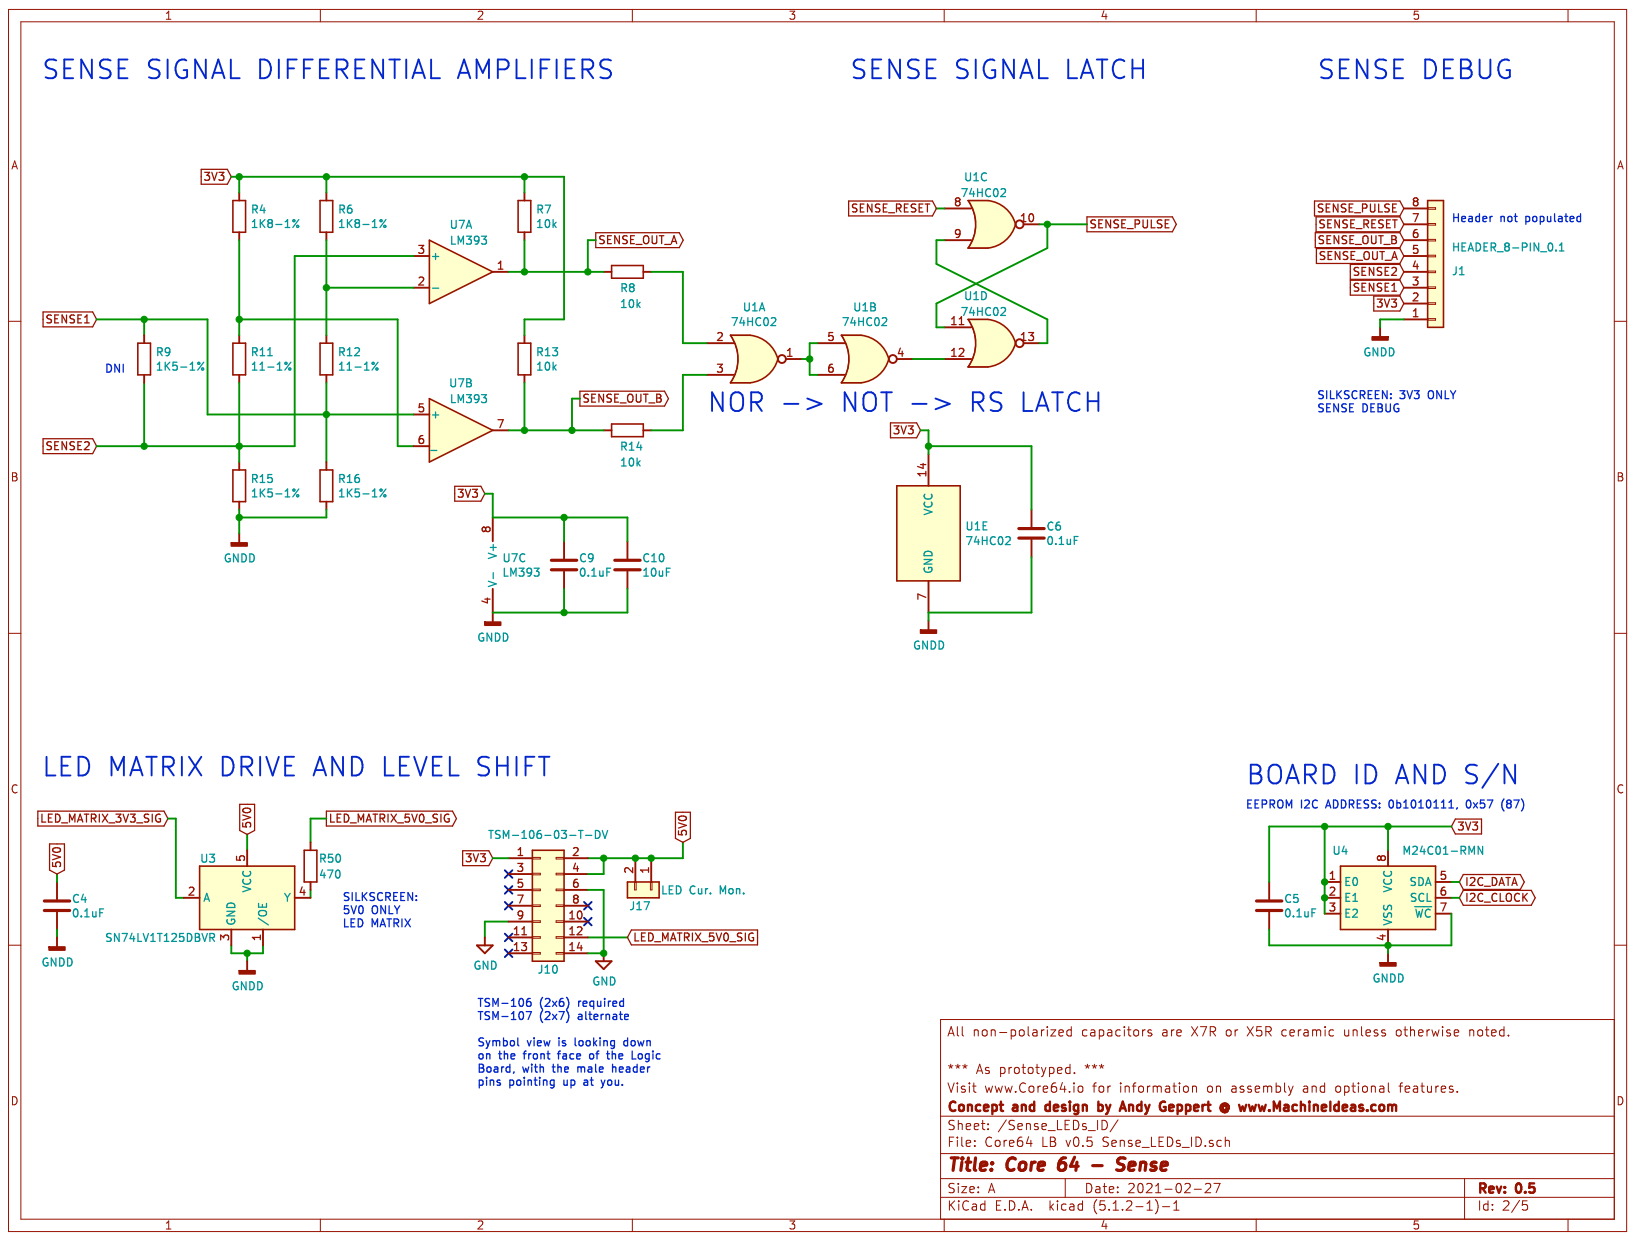
[picture p110: page 2]

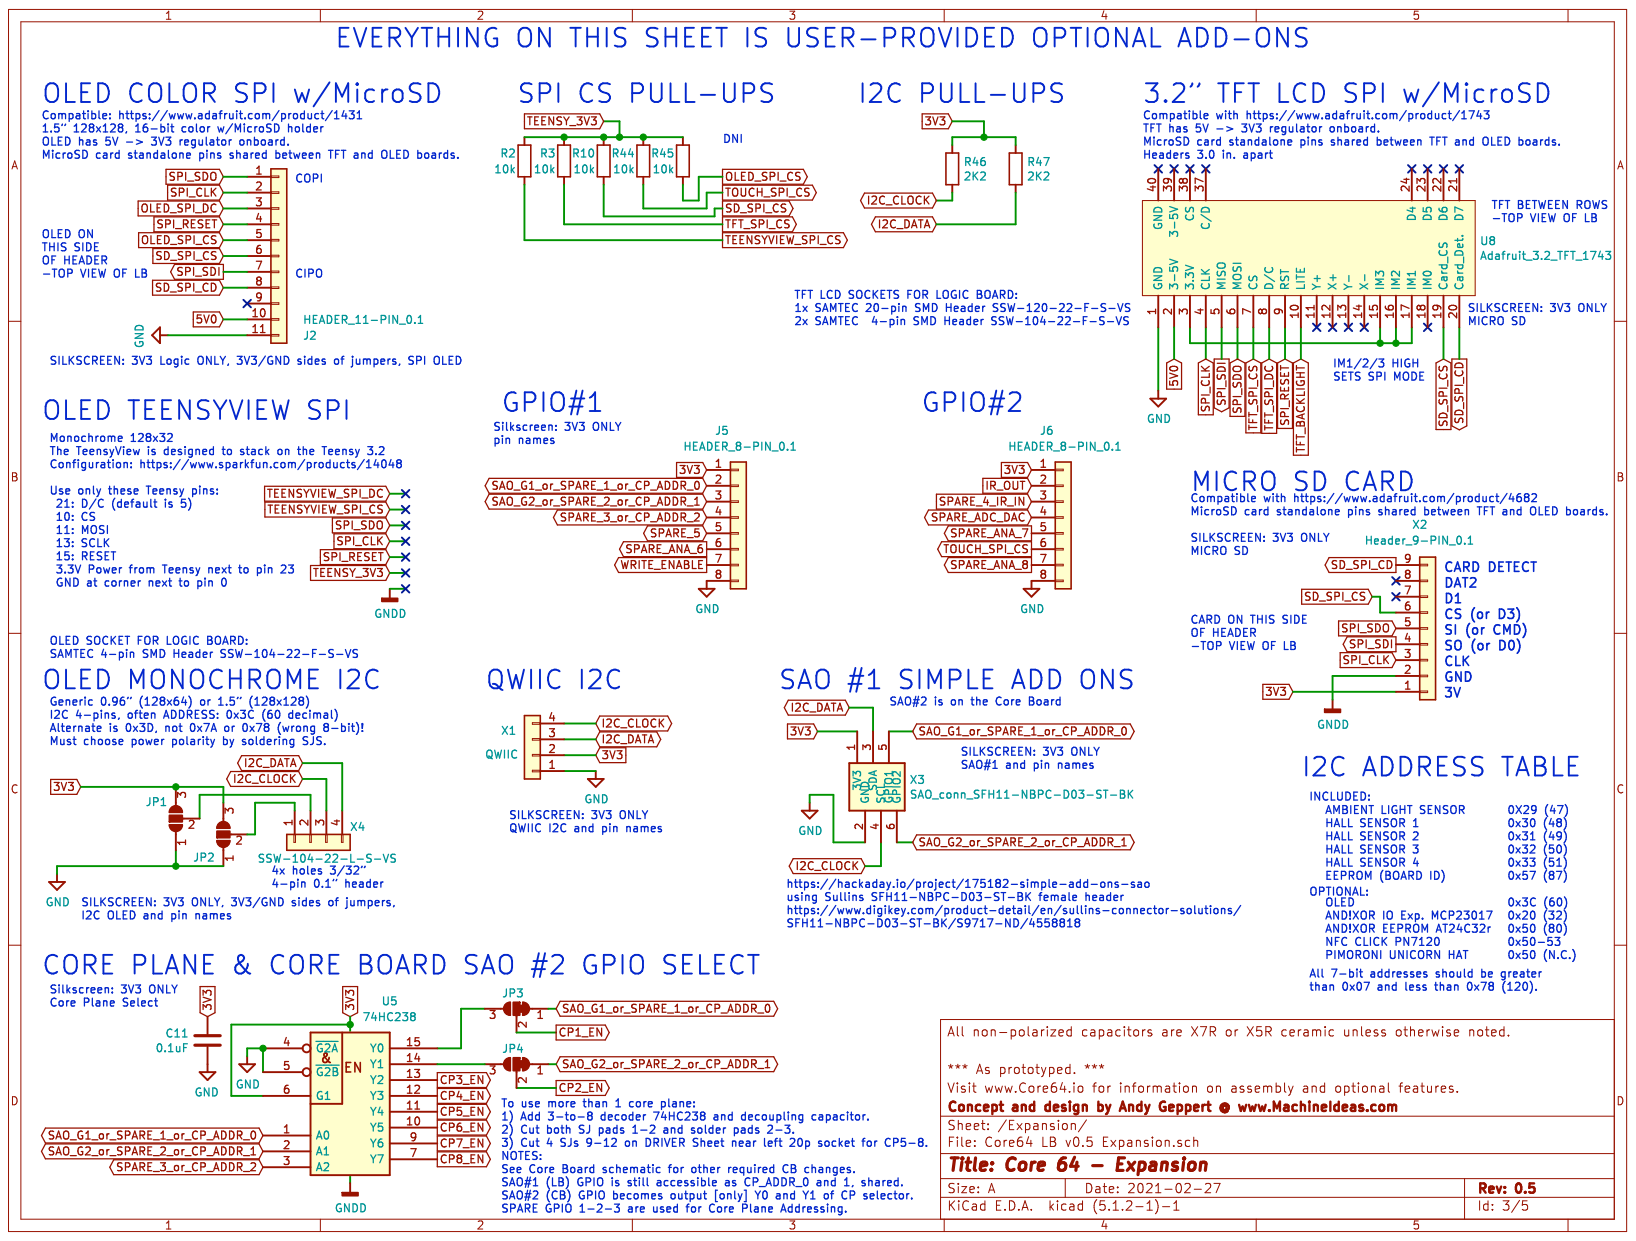
[picture p111: page 3]

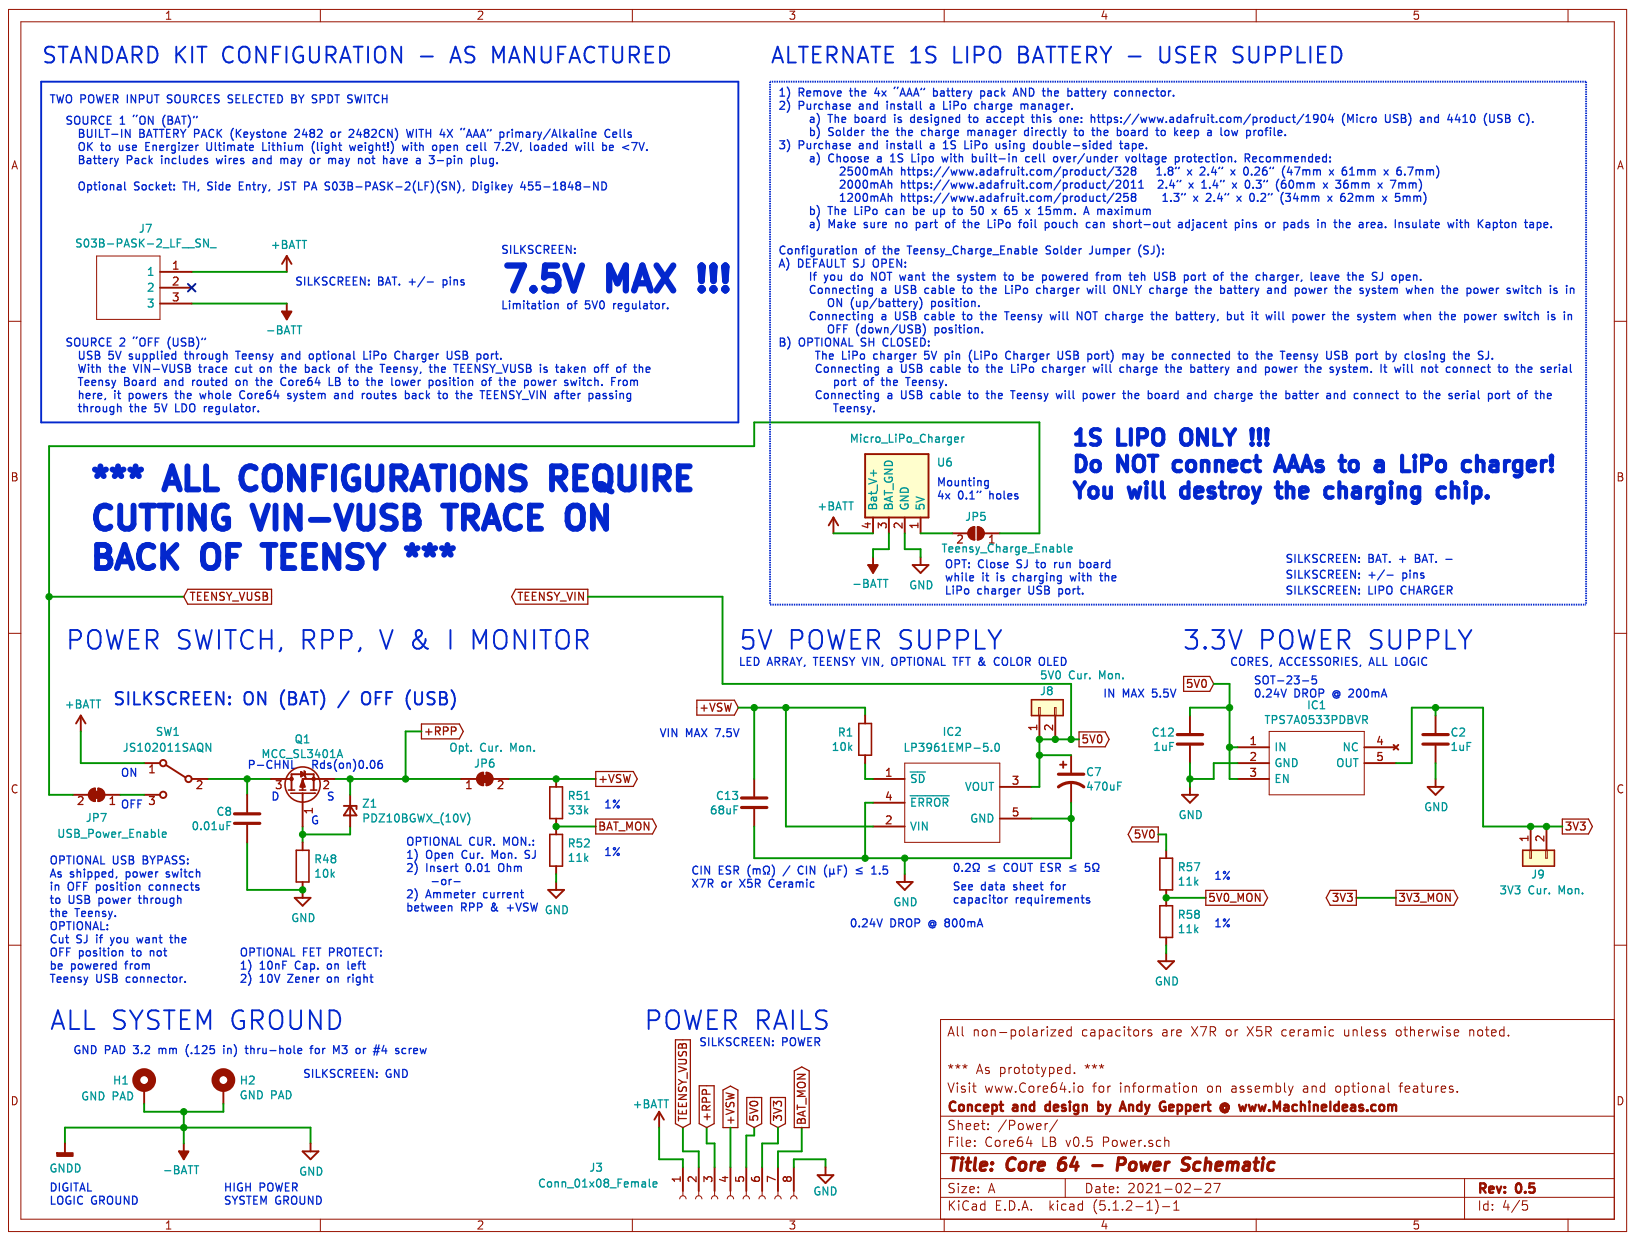
[picture p112: page 4]

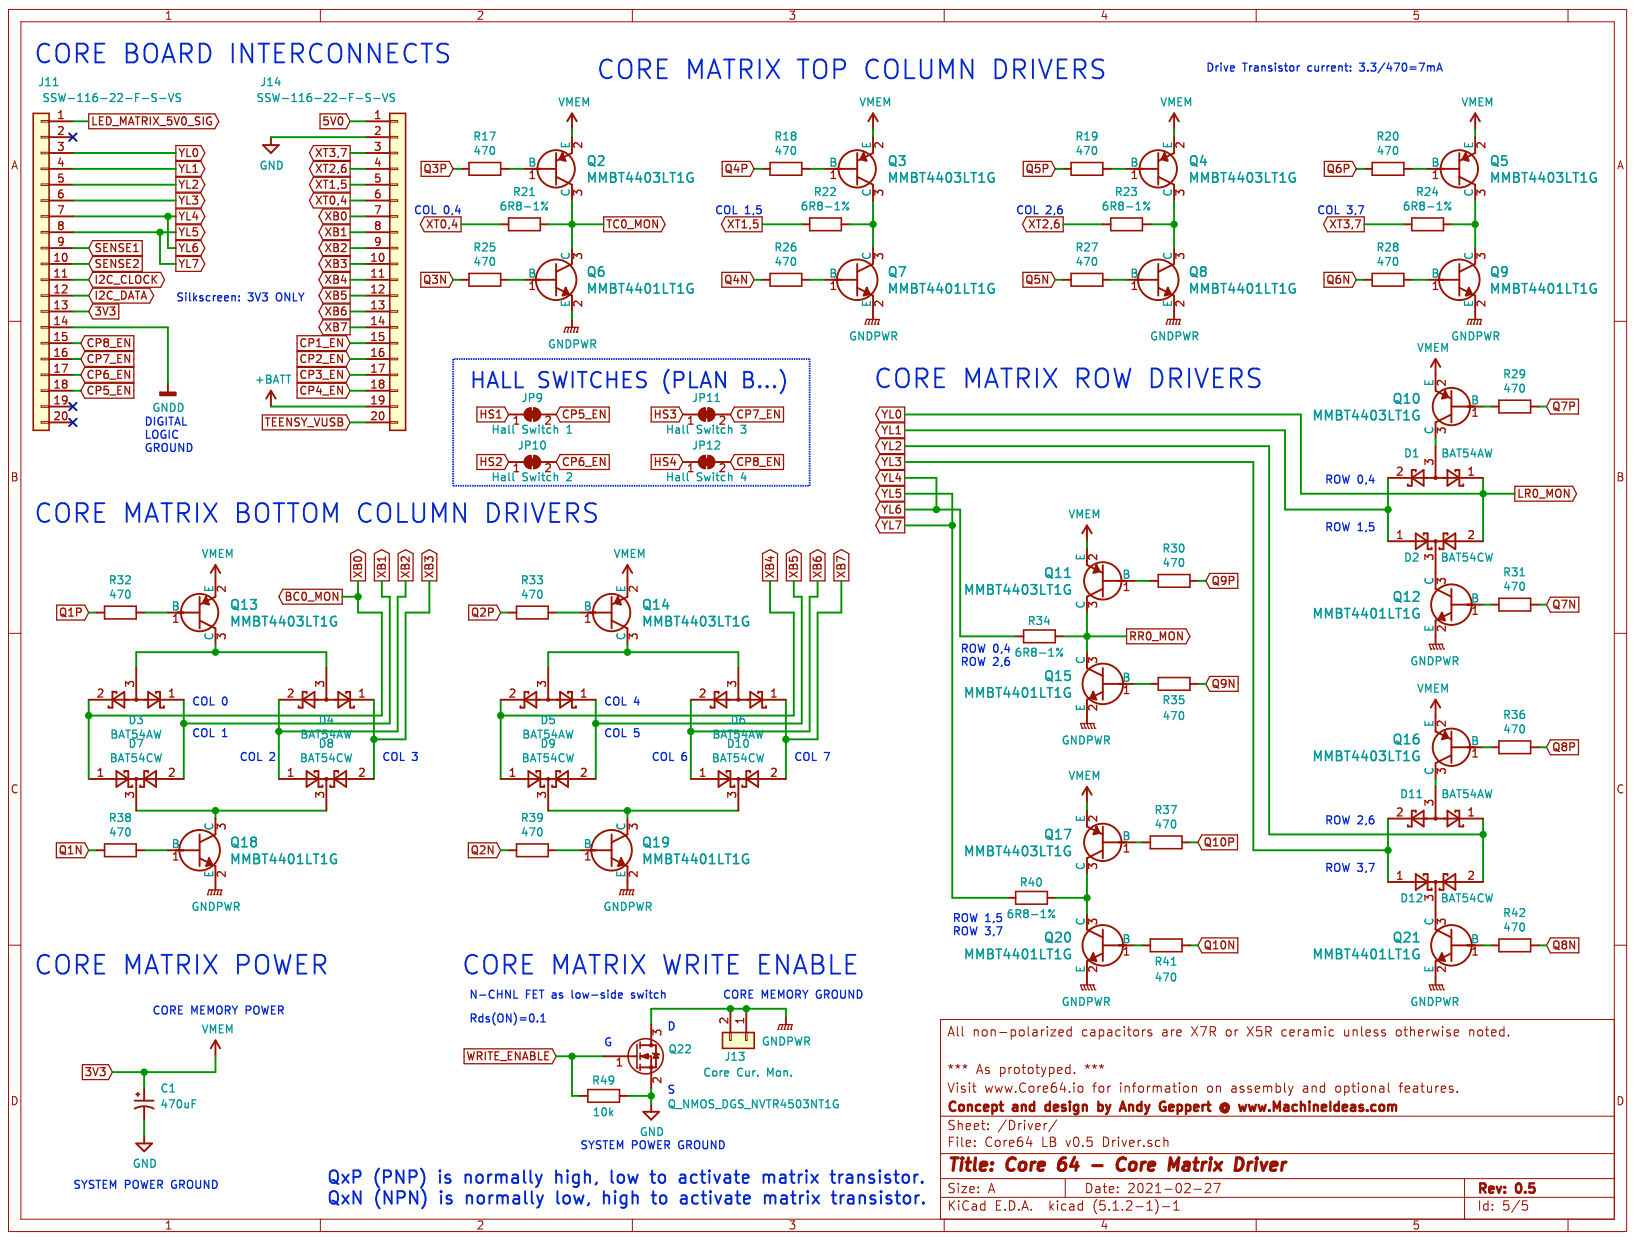
[picture p113: page 5]
