ageppert/Core-64-Interactive-Core-Memory-Badge/Electronic Design/Core64 LM v0.1/Core64 LM v0.1 Schematic as prototyped 2021-02-17.pdf

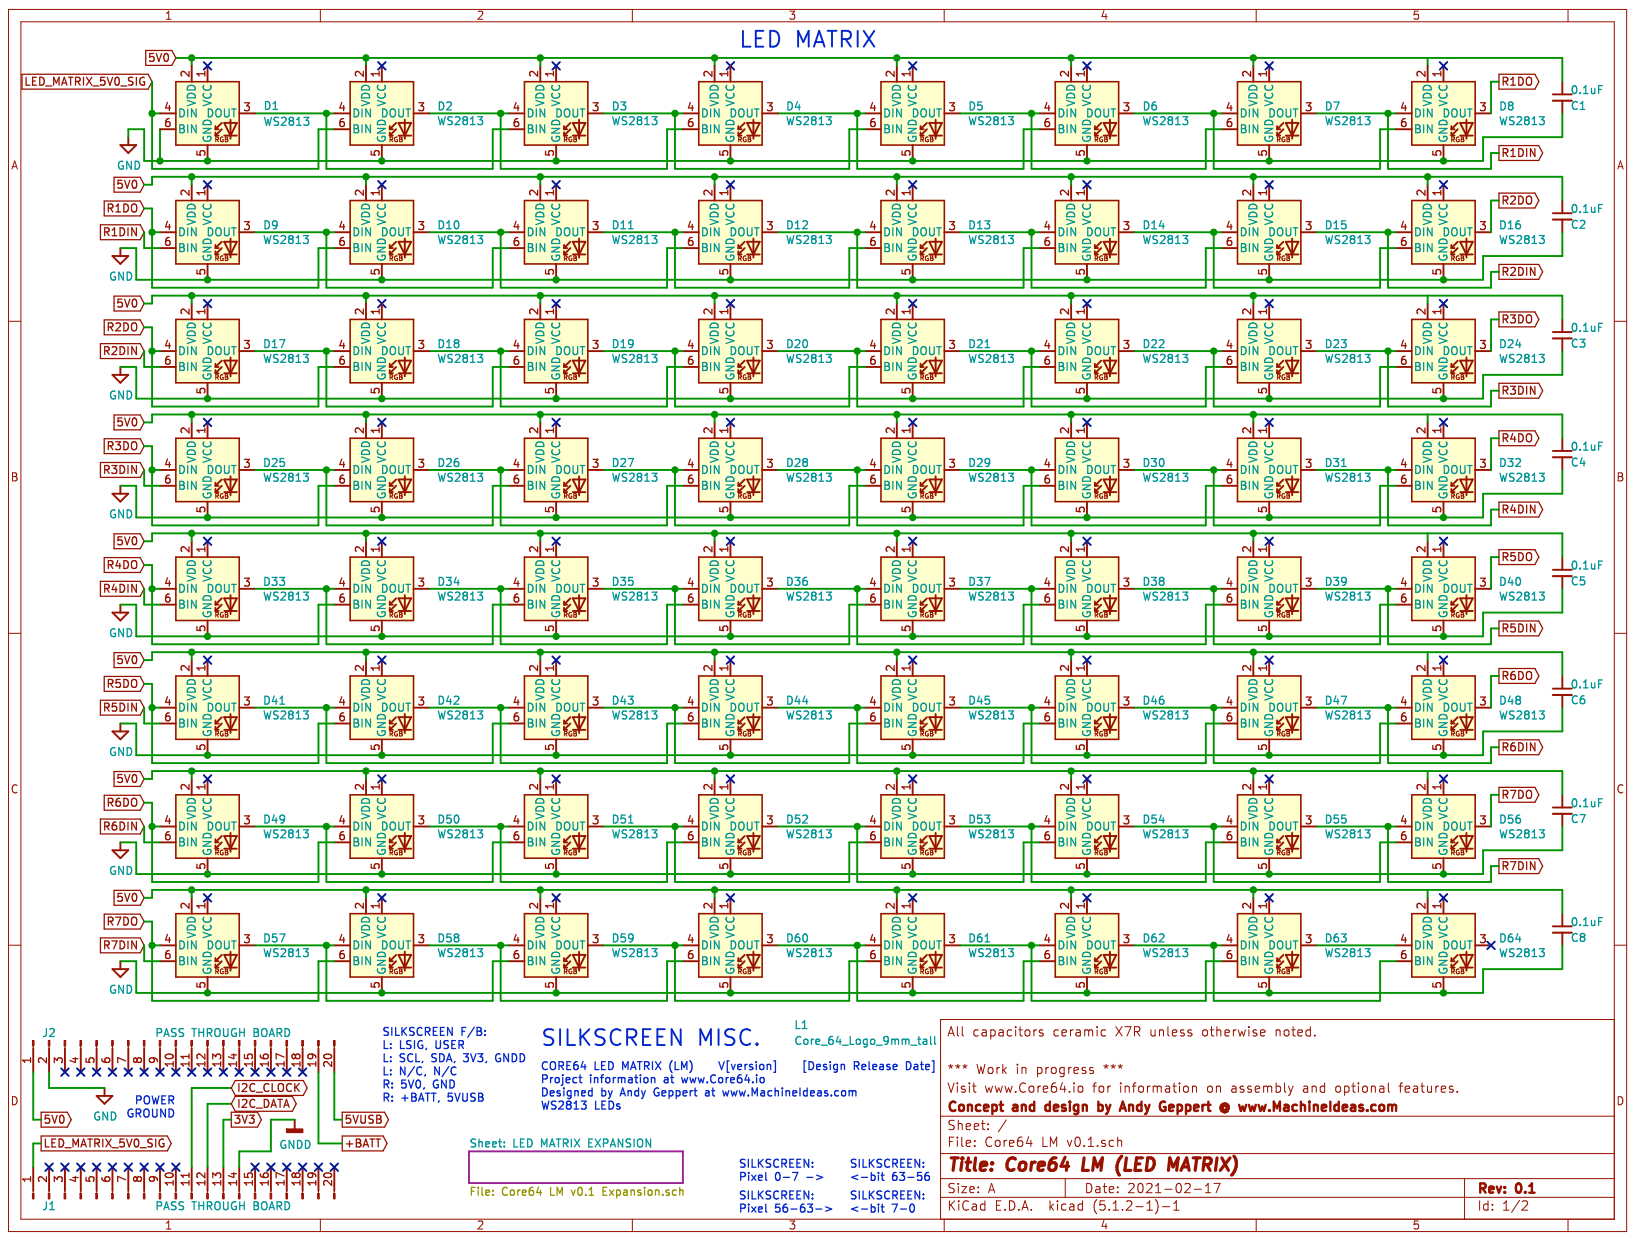
[picture p114: page 1]

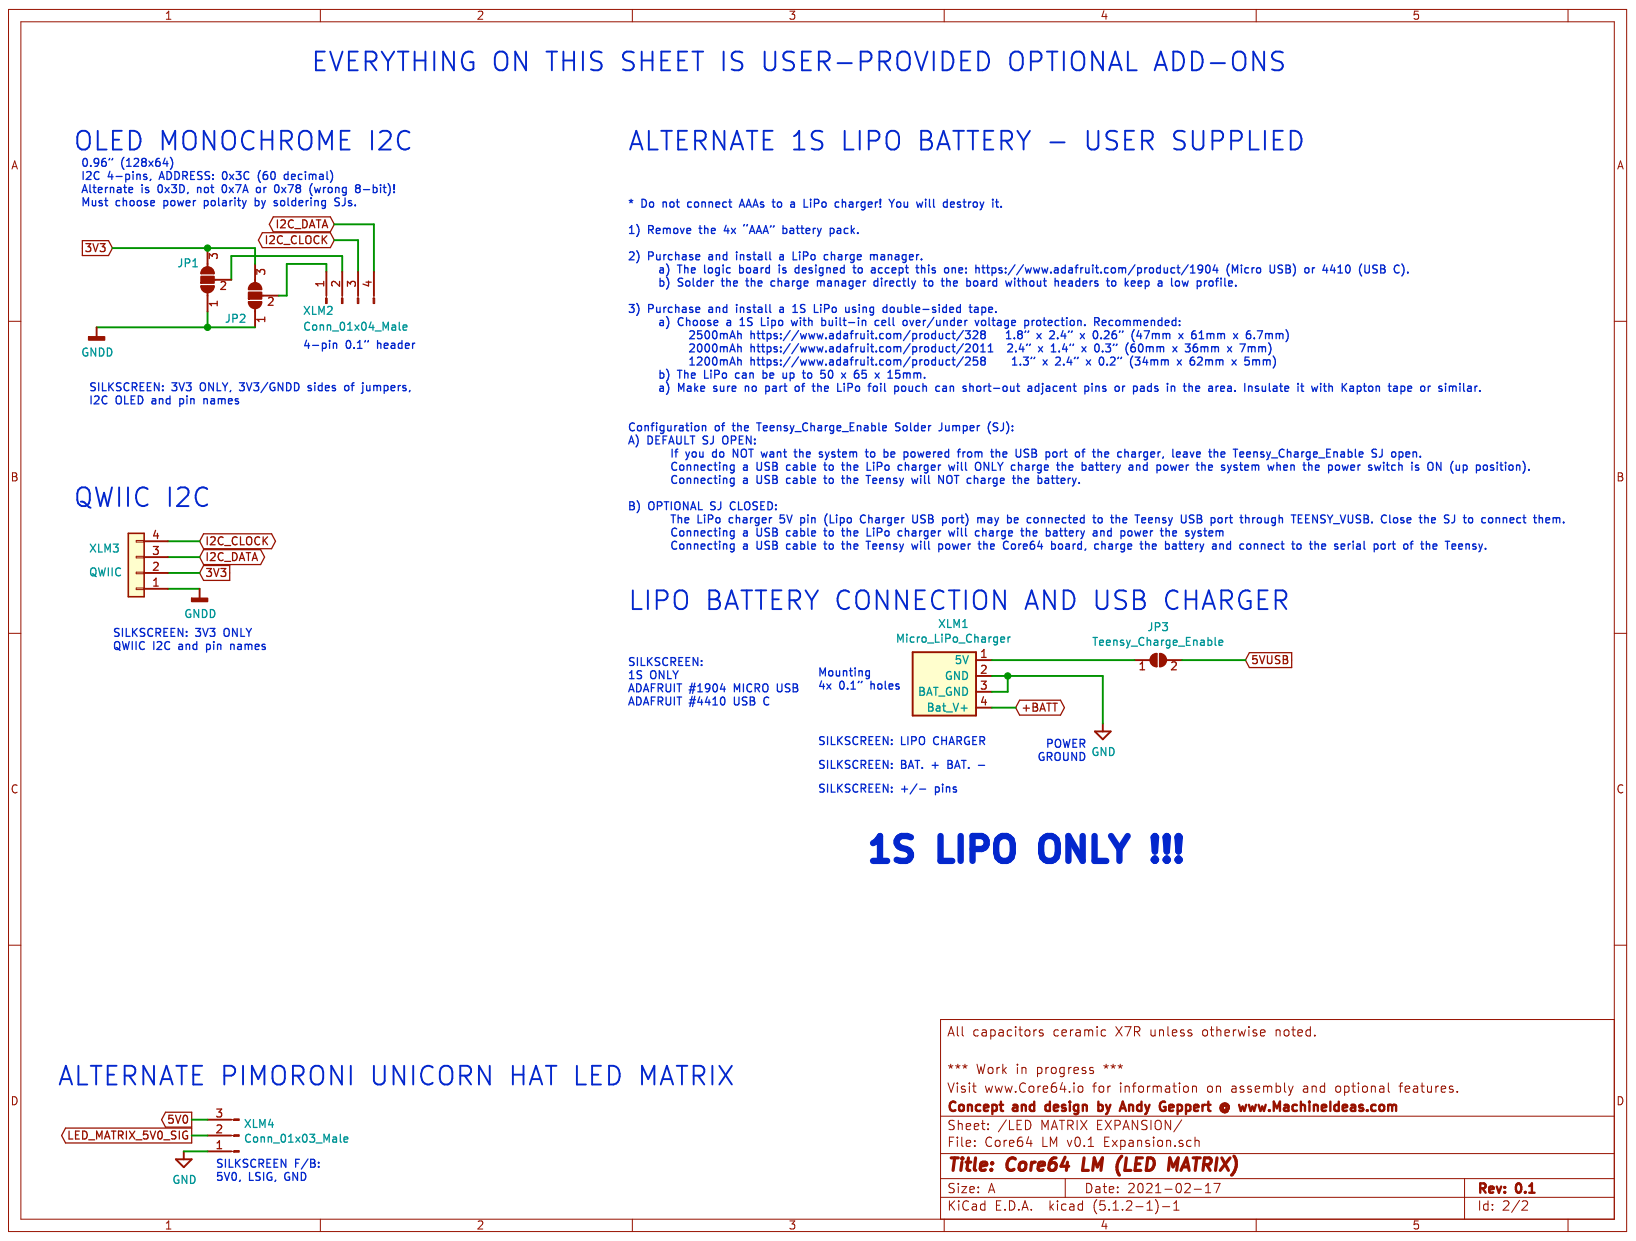
[picture p115: page 2]
