ageppert/Core-64-Interactive-Core-Memory-Badge/Electronic Design/Core64 LB v0.4/Core64 LB v0.4 2020-11-19 As Fabricated Schematic.pdf

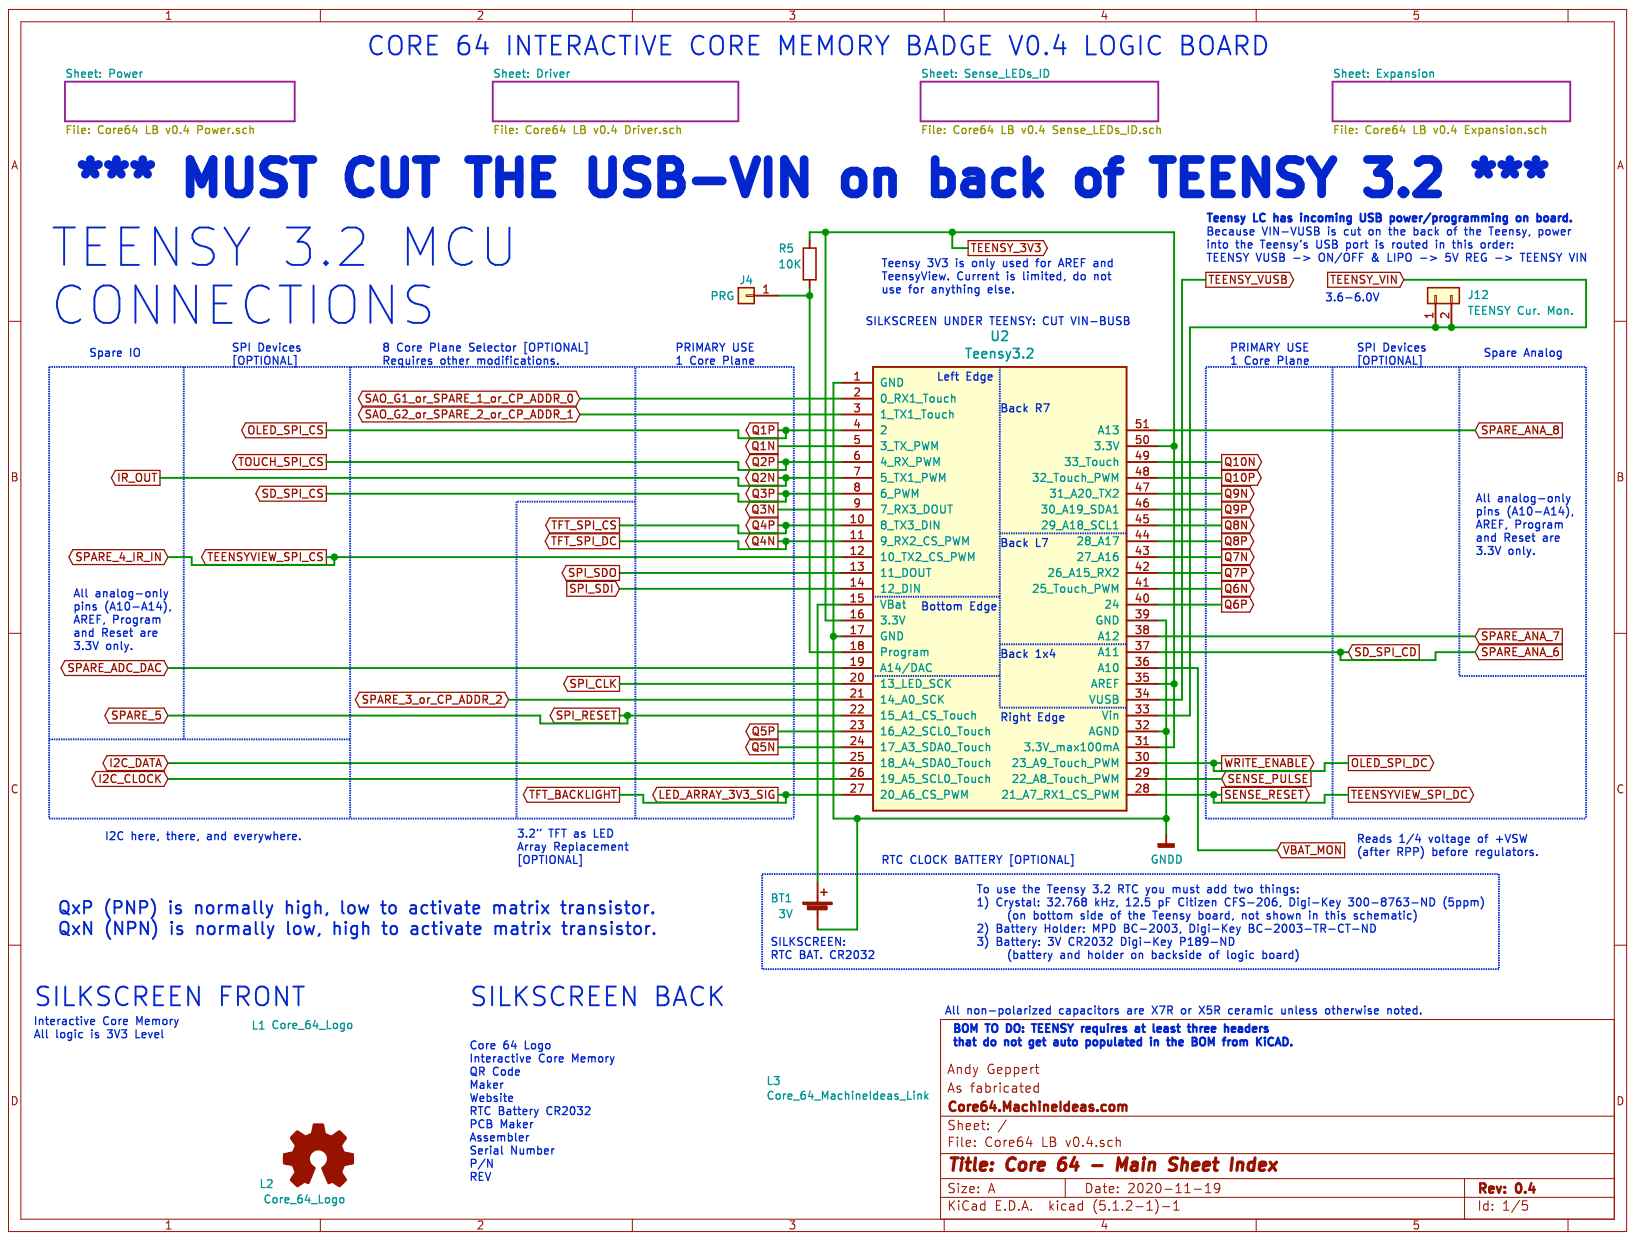
[picture p116: page 1]

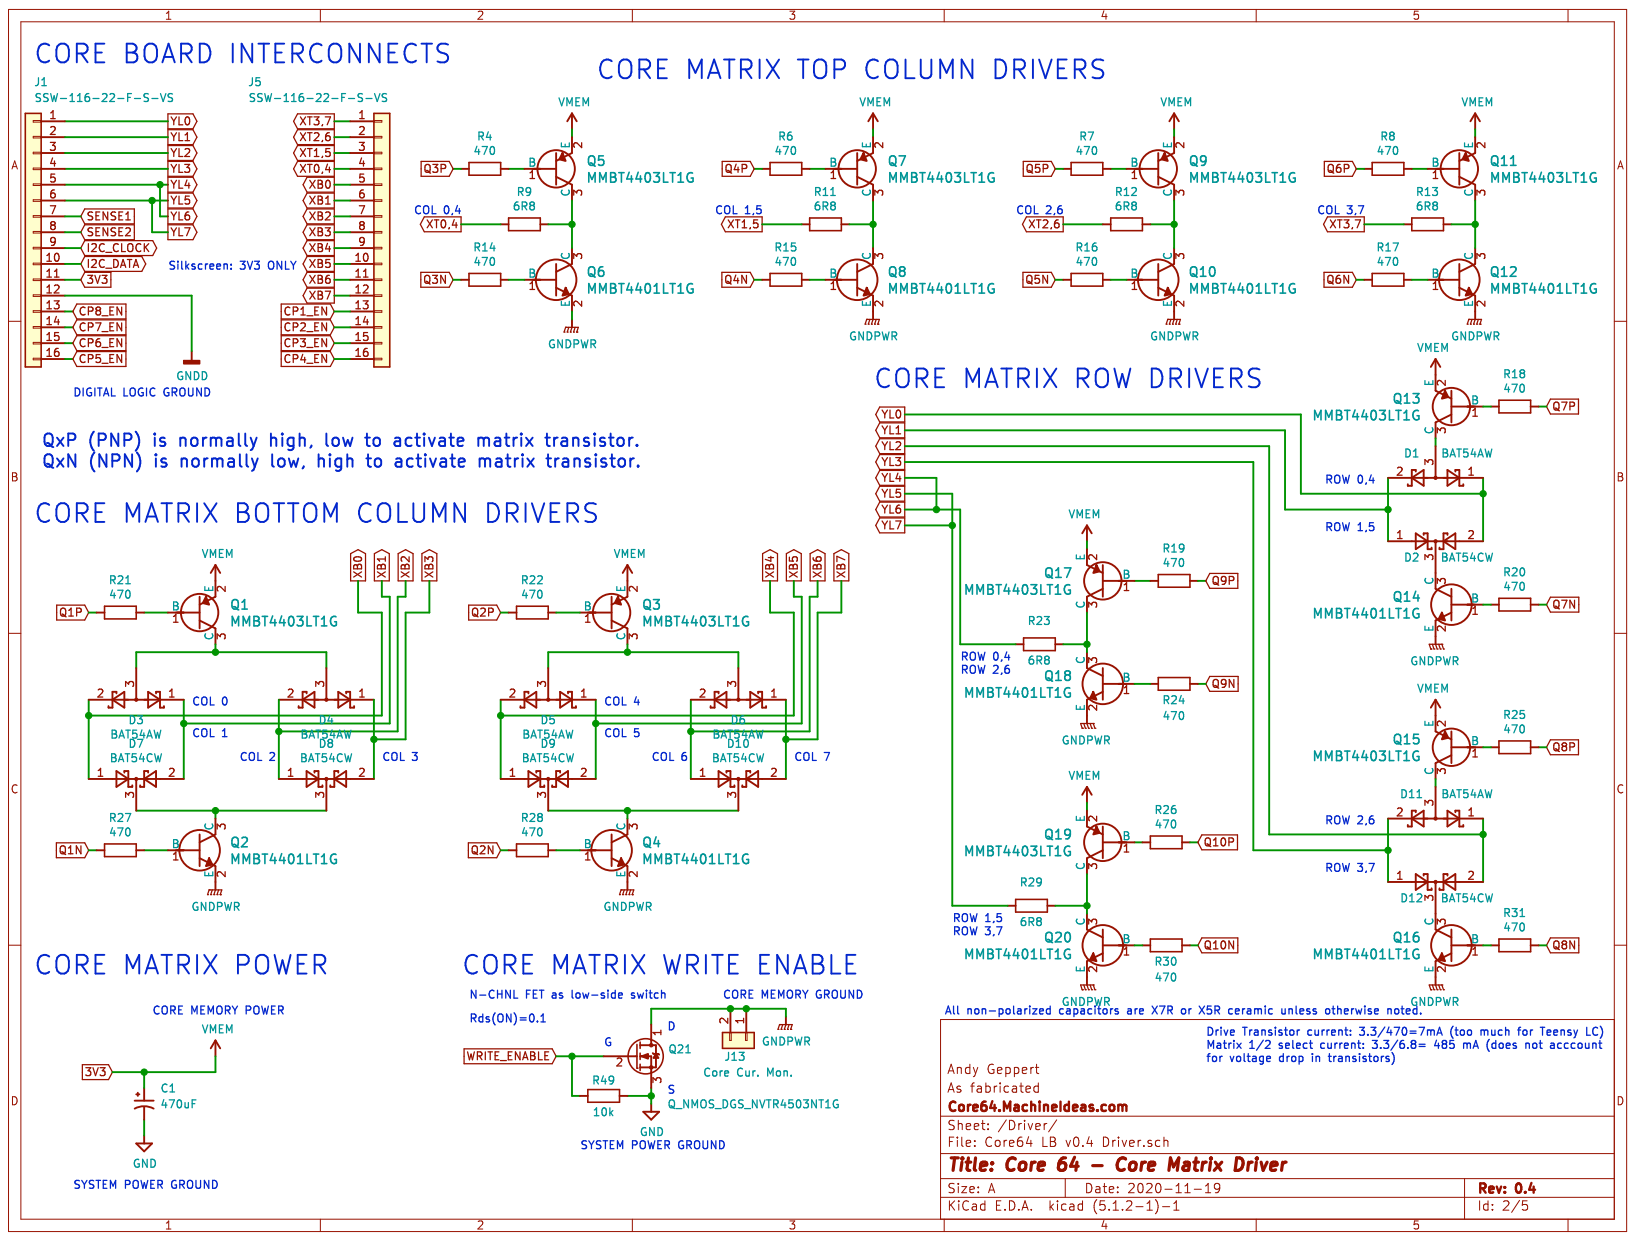
[picture p117: page 2]

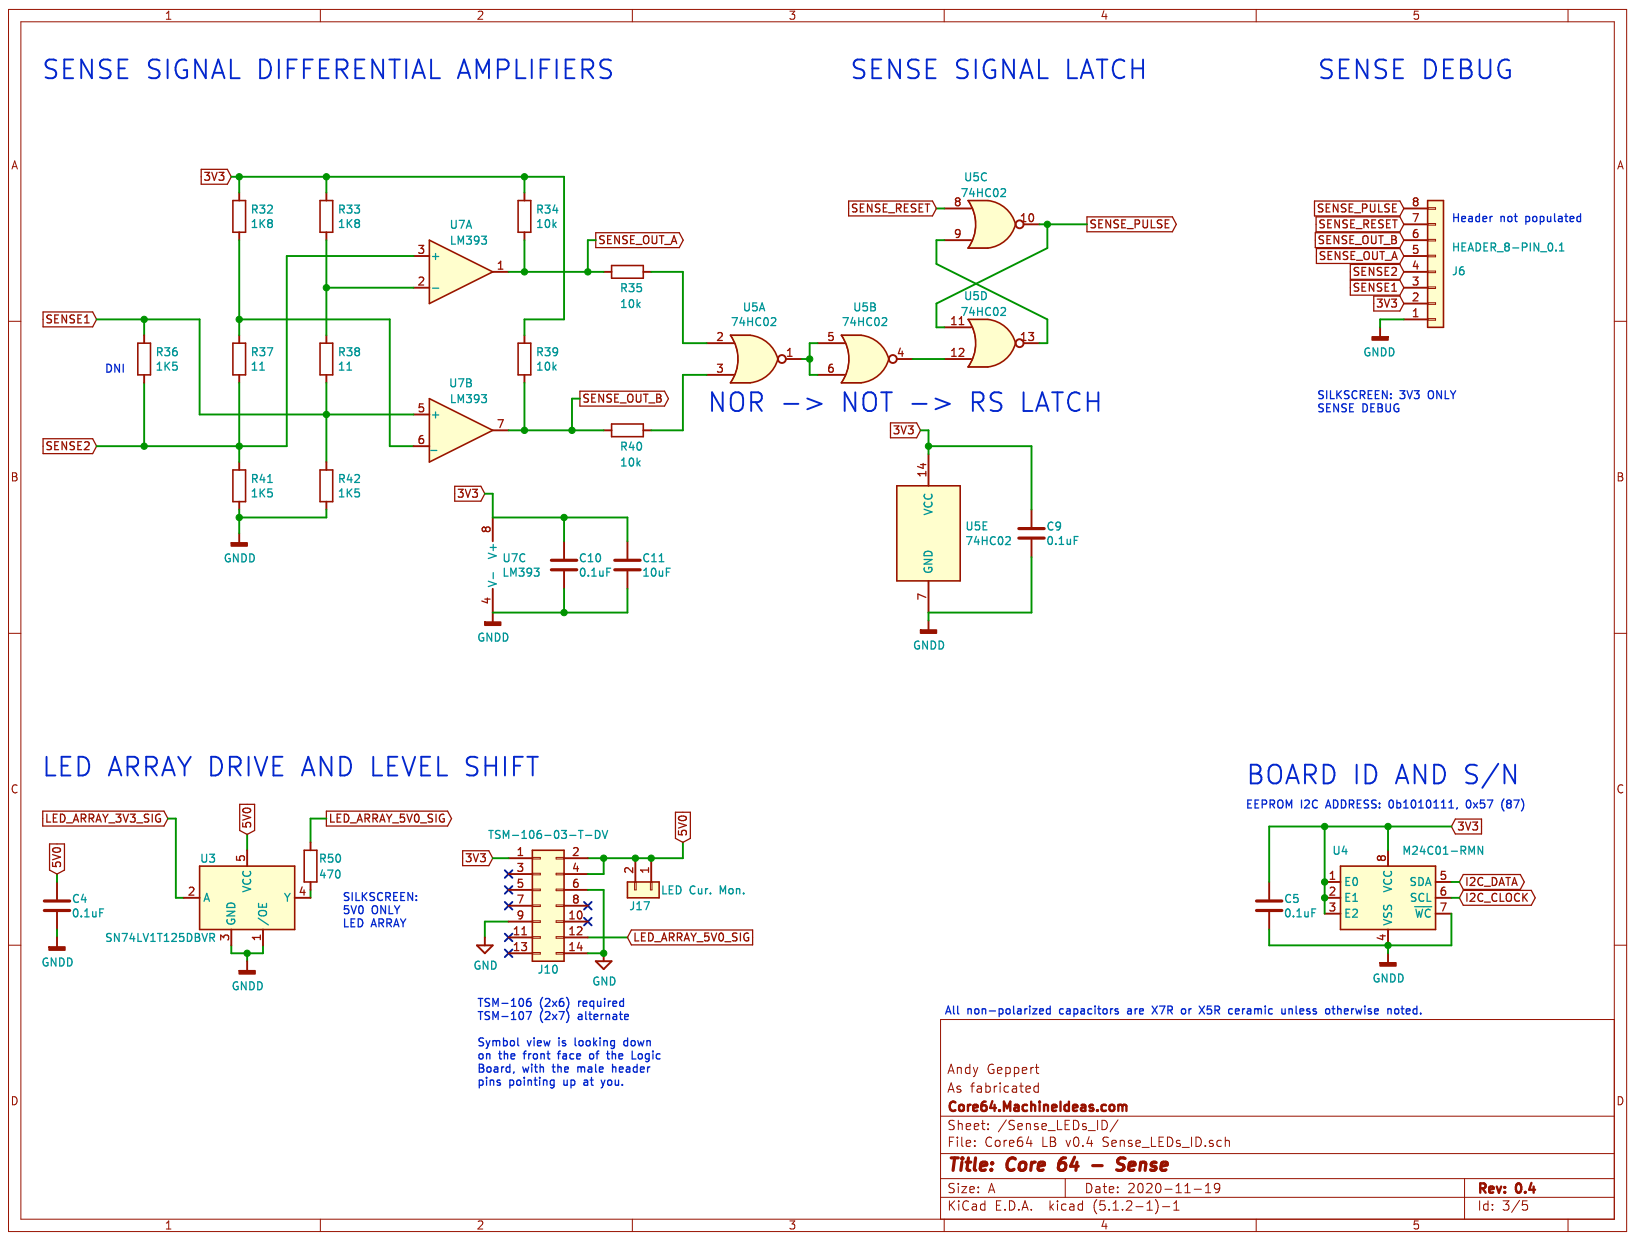
[picture p118: page 3]

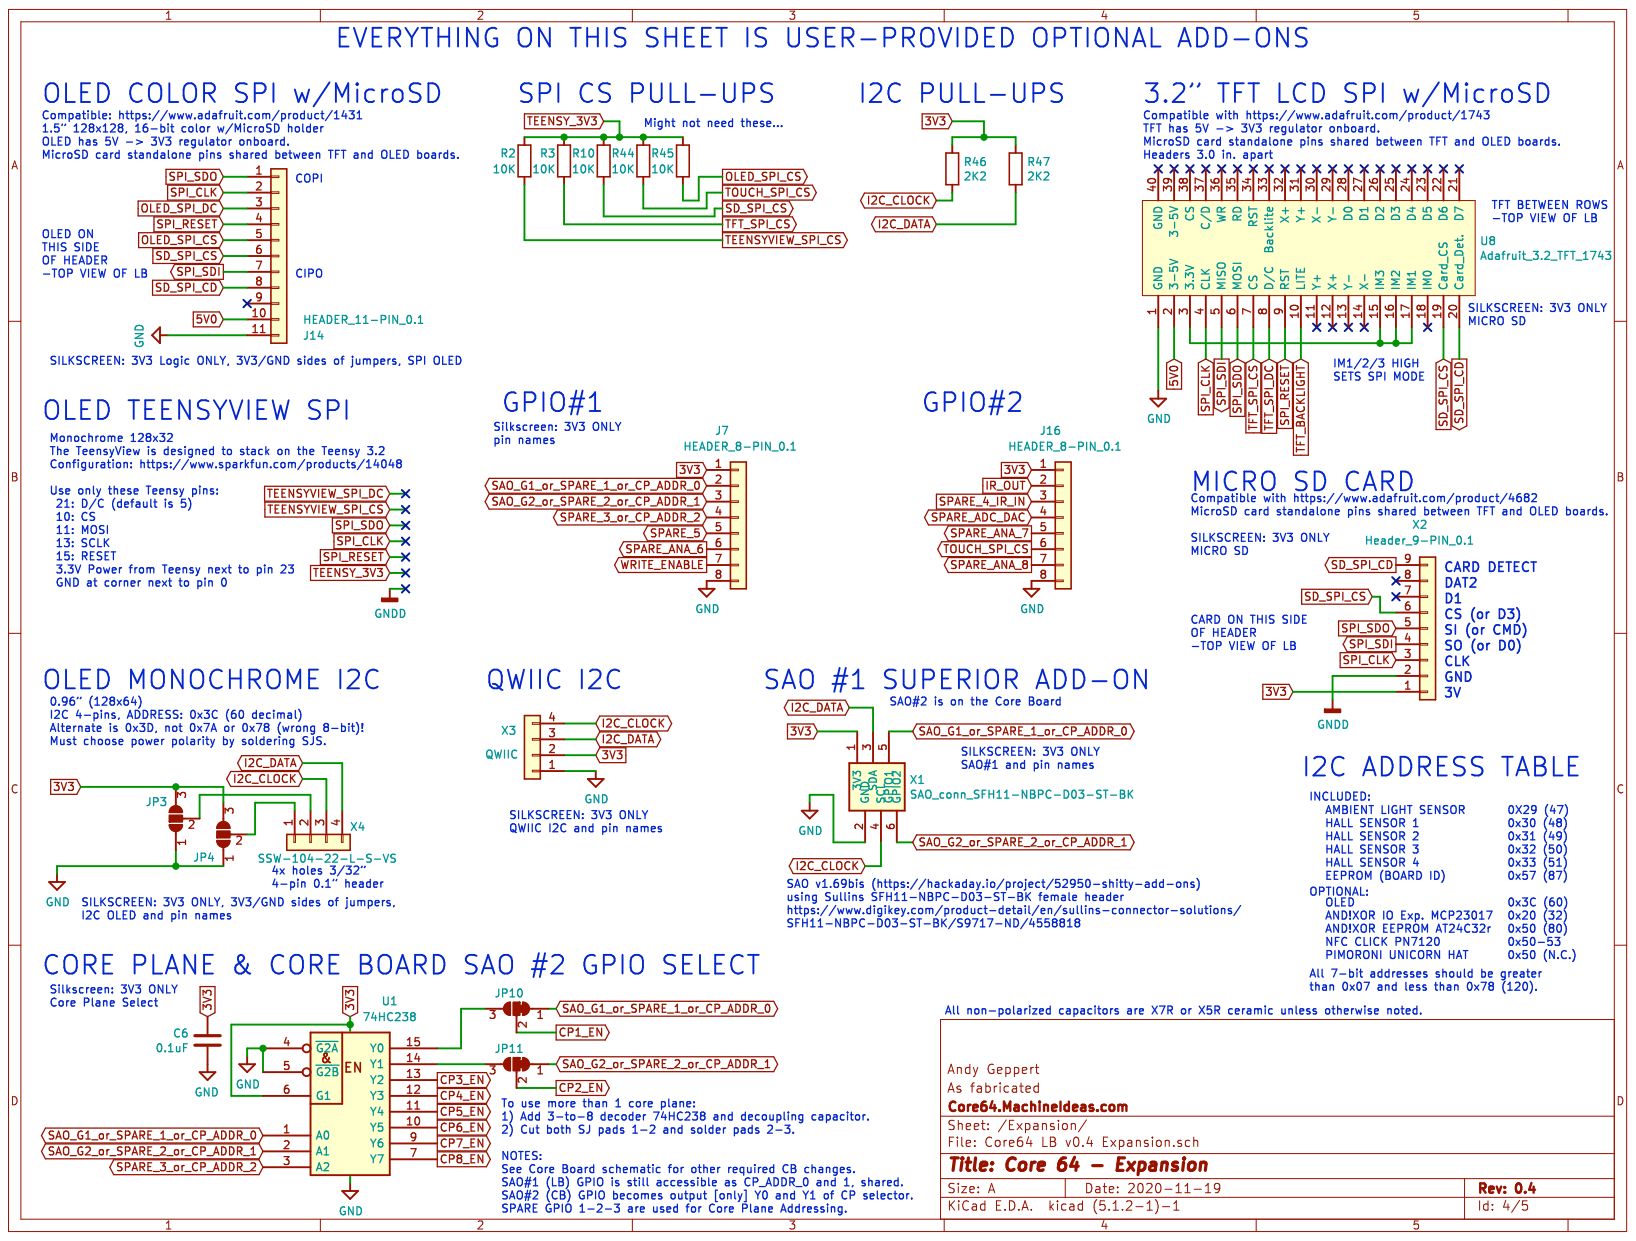
[picture p119: page 4]

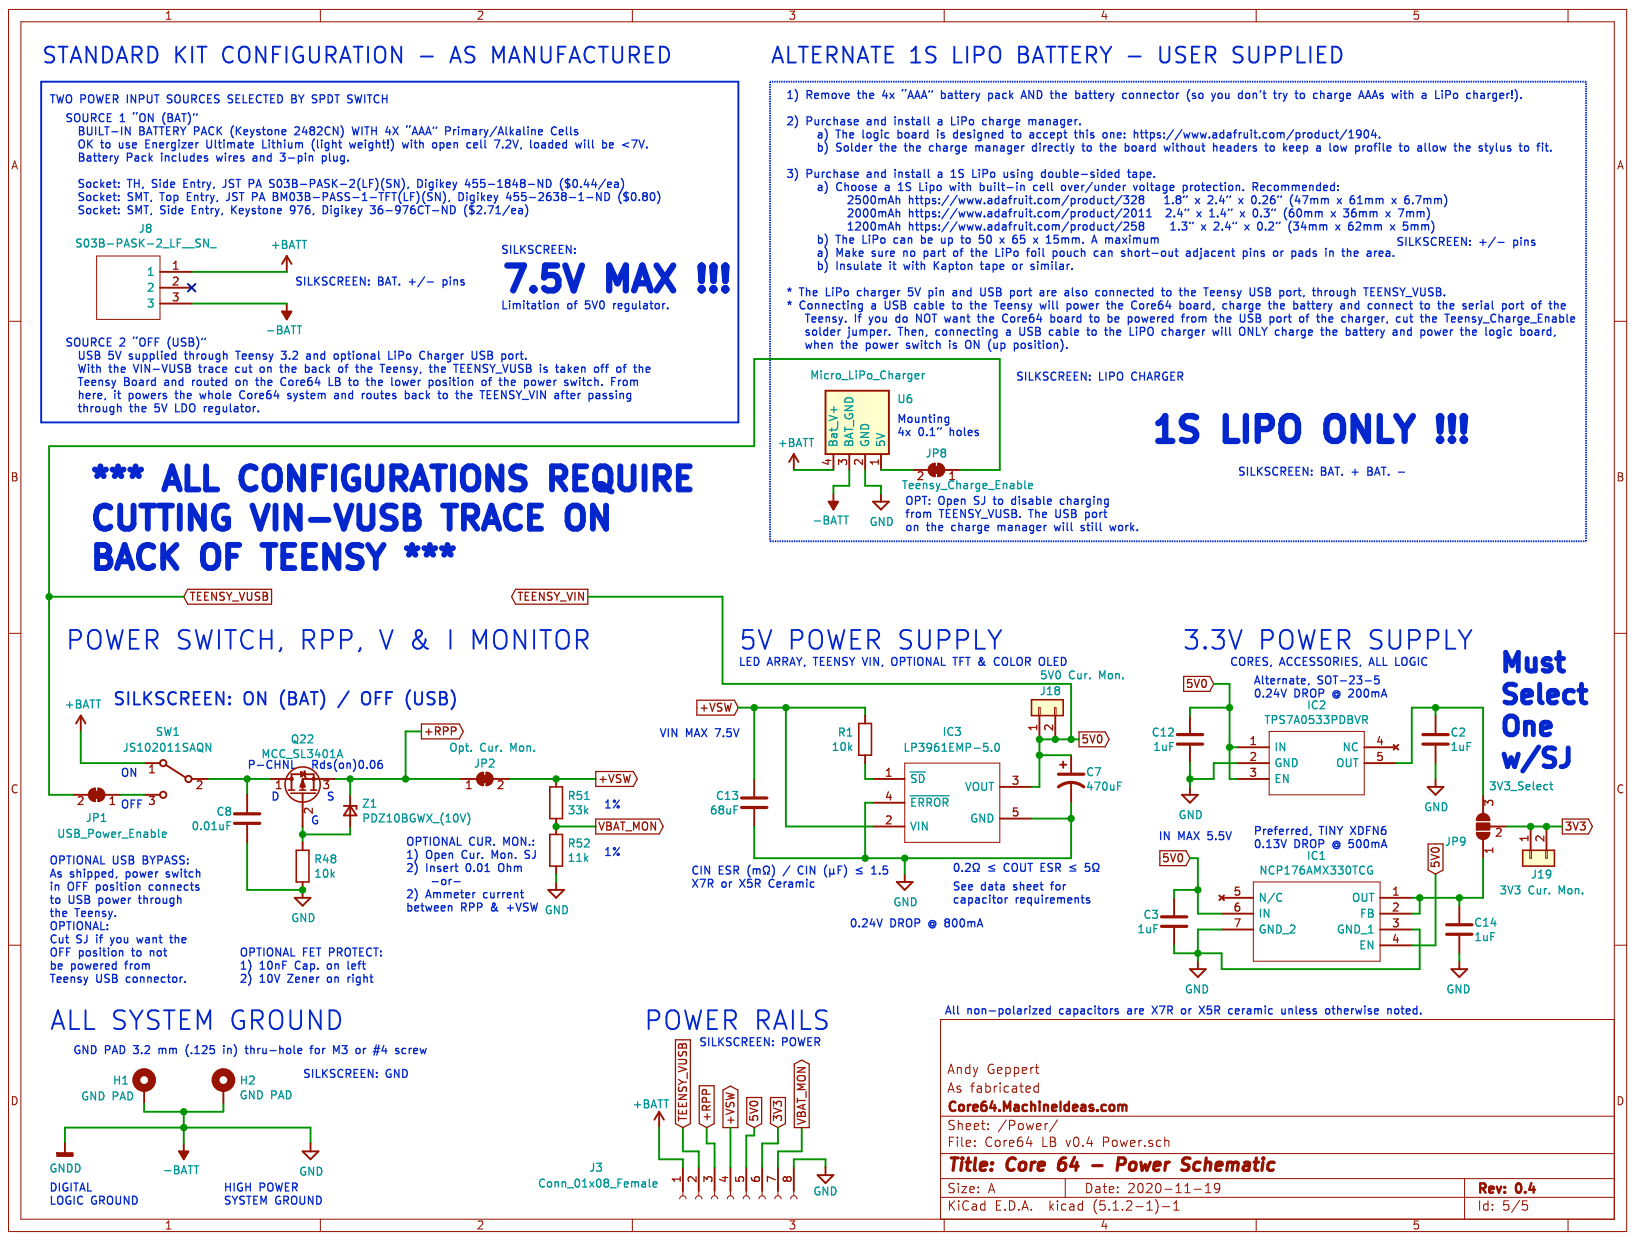
[picture p120: page 5]
