ageppert/Core-64-Interactive-Core-Memory-Badge/Electronic Design/Core64 LB v0.4/PCB Bottom.pdf

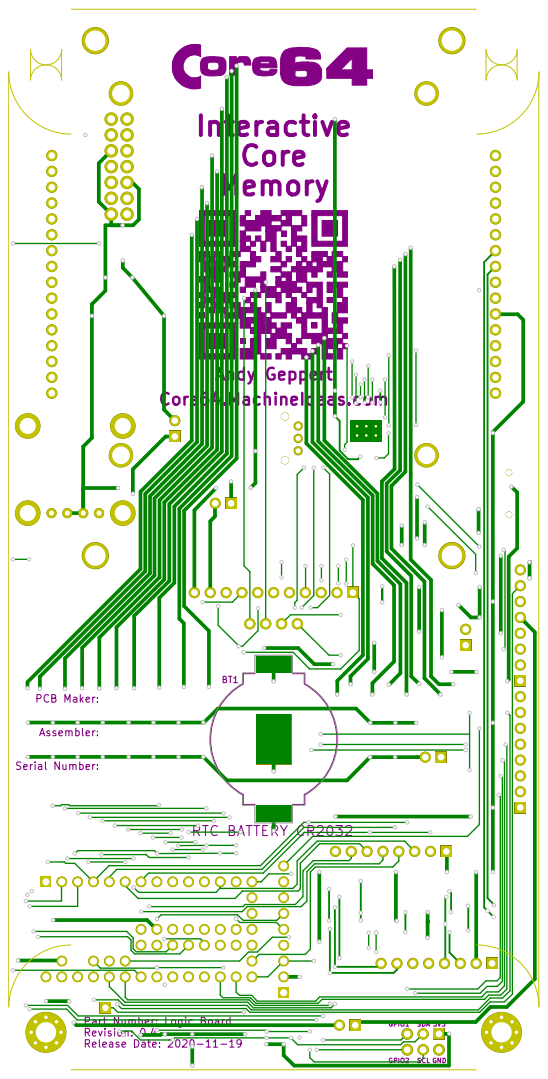
[picture p121: page 1]
