ageppert/Core-64-Interactive-Core-Memory-Badge/Electronic Design/Core64 LB v0.4/PCB Top.pdf

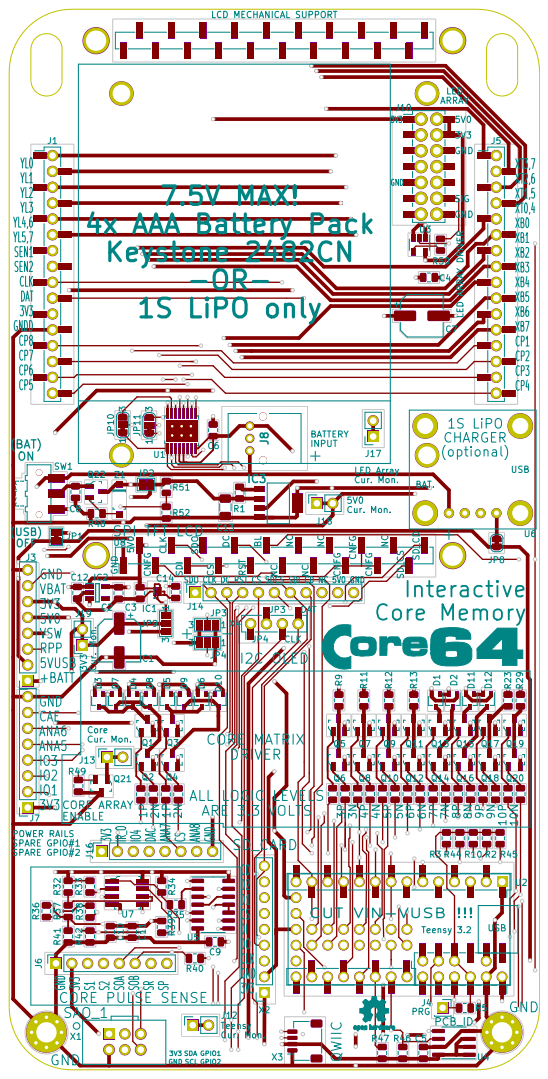
[picture p122: page 1]
