ageppert/Core-64-Interactive-Core-Memory-Badge/Electronic Design/Core64 CB v0.4/Core64 CB V0.4 PCB Front.pdf

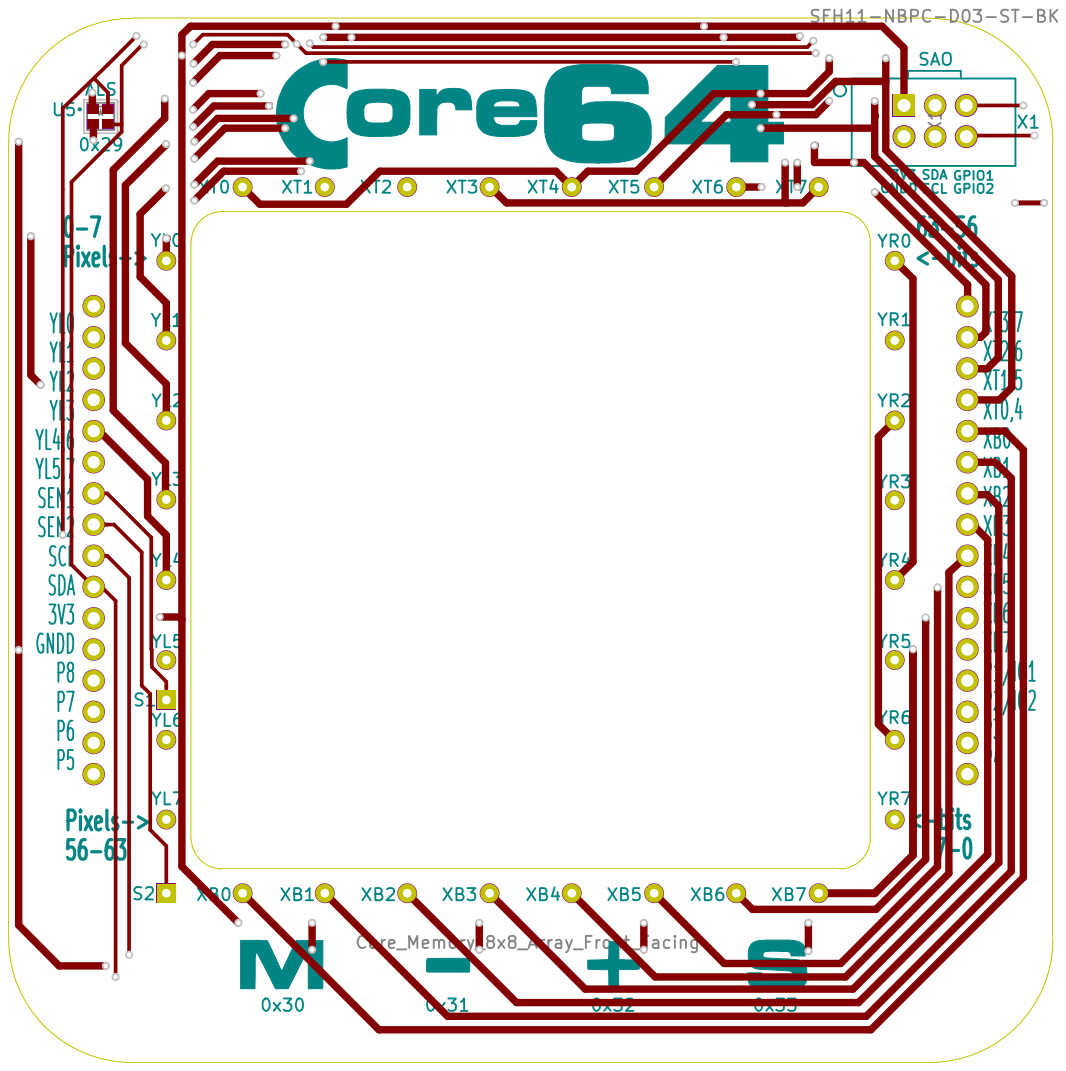
[picture p123: page 1]
