ageppert/Core-64-Interactive-Core-Memory-Badge/Electronic Design/Core64 CB v0.4/Core64 CB v0.4 Schematic.pdf

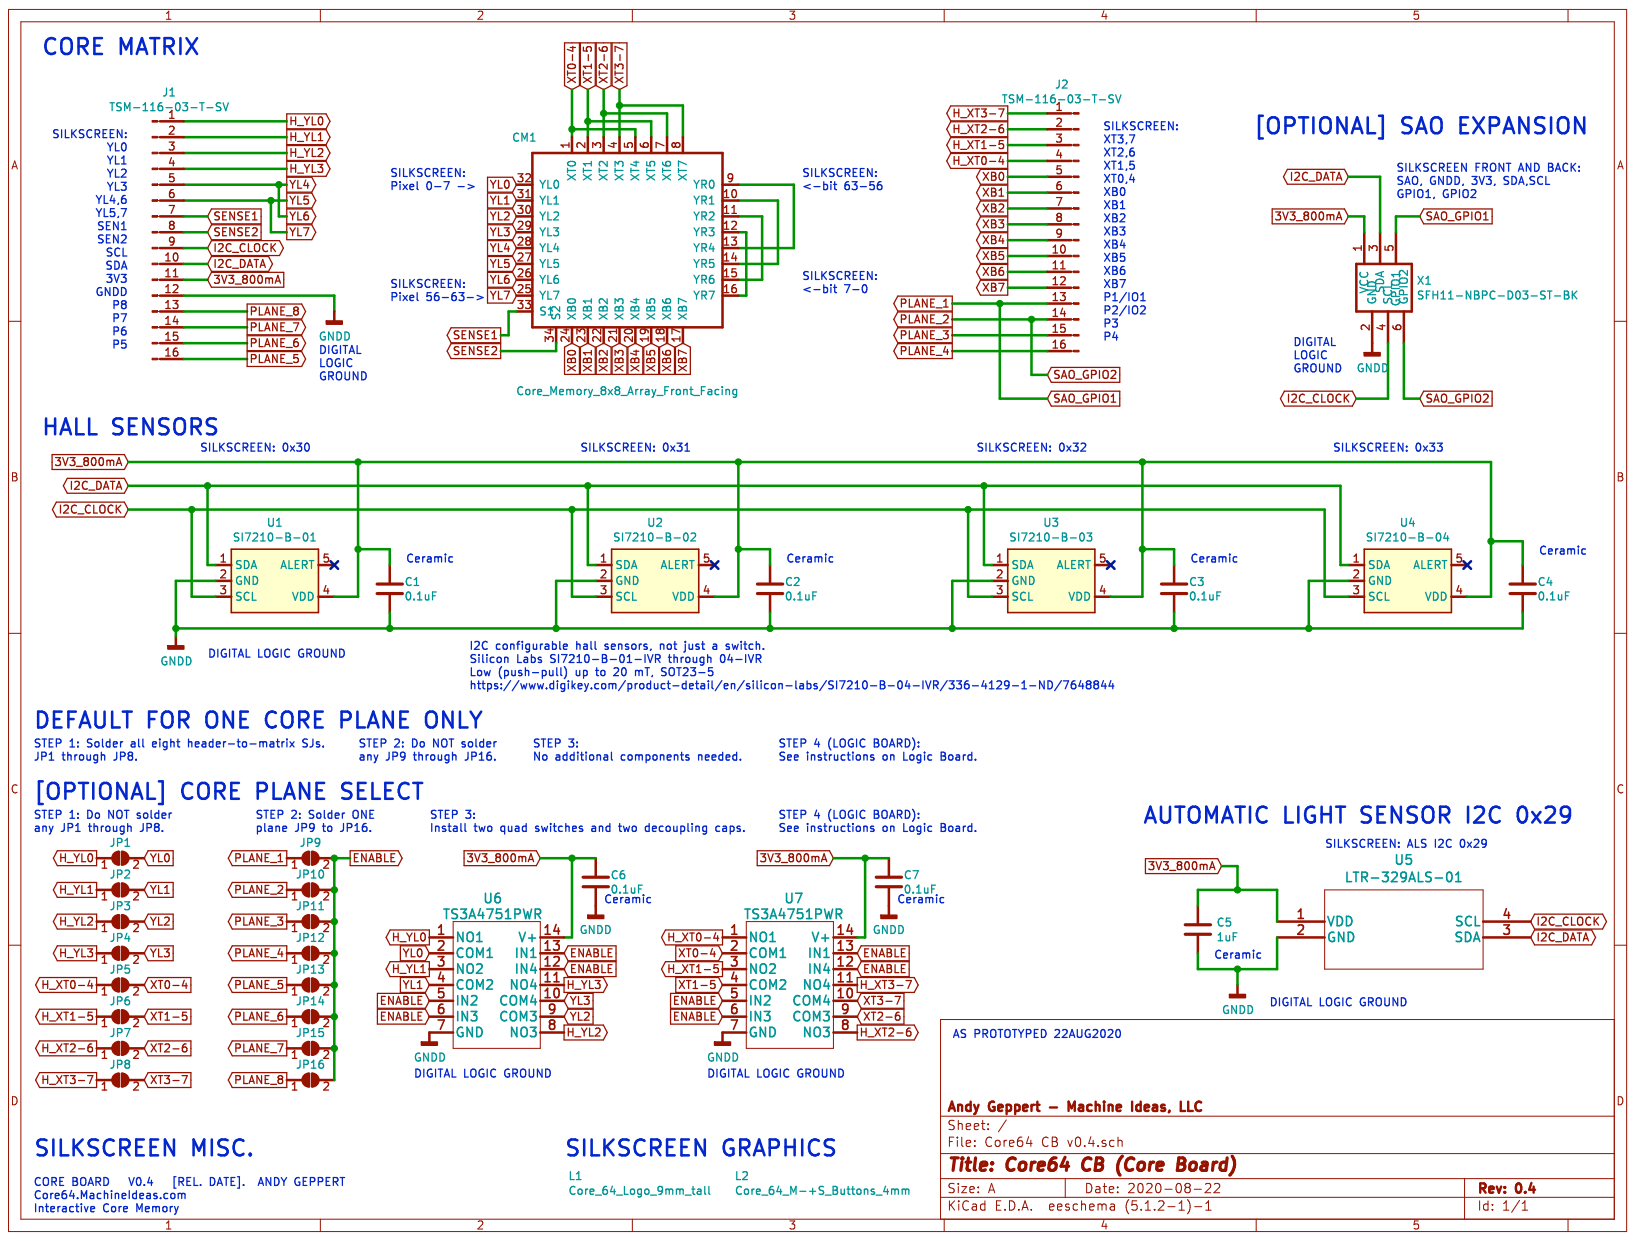
[picture p124: page 1]
