ageppert/Core-64-Interactive-Core-Memory-Badge/Firmware Source Code/Core-64-Interactive-Core-Memory-Badge/CharacterMap.h

/*
PURPOSE:
// Character Map
// Characters could be 4*5 (w*h) to save space or full 8*8.
// A full alphabet table is 26 x 5 x 4 bits = 65 bytes (if stored maximum efficiently)
// Array arranged directly as "I [heart] CORE MEMORY!" = 16 elements, numbered 0 to 15

SETUP:
- none
*/
 
#ifndef CHARACTER_MAP_H
#define CHARACTER_MAP_H

#if (ARDUINO >= 100)
#include <Arduino.h>
#else
#include <WProgram.h>
#endif

#include <stdint.h>

#ifdef __cplusplus
extern "C" {
#endif

// Use program memory for constants
// https://forum.arduino.cc/index.php?topic=45681.0

const static bool character_font_wide[15][8][8] PROGMEM = {   // Character, Row, Column
{
  {0,0,0,0,0,0,0,0}, // space
  {0,0,0,0,0,0,0,0},
  {0,0,0,0,0,0,0,0},
  {0,0,0,0,0,0,0,0},
  {0,0,0,0,0,0,0,0},
  {0,0,0,0,0,0,0,0},
  {0,0,0,0,0,0,0,0},
  {0,1,0,1,0,1,0,1}
},
{
  {0,0,1,1,1,1,0,0}, // I
  {0,0,0,1,1,0,0,0},
  {0,0,0,1,1,0,0,0},
  {0,0,0,1,1,0,0,0},
  {0,0,0,1,1,0,0,0},
  {0,0,0,1,1,0,0,0},
  {0,0,1,1,1,1,0,0},
  {0,0,0,0,0,0,0,0}
},
{
  {0,0,1,1,0,1,1,0}, // heart
  {0,1,1,1,1,1,1,1},
  {0,1,1,1,1,1,1,1},
  {0,1,1,1,1,1,1,1},
  {0,0,1,1,1,1,1,0},
  {0,0,0,1,1,1,0,0},
  {0,0,0,0,1,0,0,0},
  {0,0,0,0,0,0,0,0}
},
{
  {0,0,1,1,1,1,0,0}, // C
  {0,1,1,0,0,1,1,0},
  {0,1,1,0,0,0,0,0},
  {0,1,1,0,0,0,0,0},
  {0,1,1,0,0,0,0,0},
  {0,1,1,0,0,1,1,0},
  {0,0,1,1,1,1,0,0},
  {0,0,0,0,0,0,0,0}
},
{
  {0,0,1,1,1,1,0,0}, // O
  {0,1,1,0,0,1,1,0},
  {0,1,1,0,0,1,1,0},
  {0,1,1,0,0,1,1,0},
  {0,1,1,0,0,1,1,0},
  {0,1,1,0,0,1,1,0},
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
   { 35, 35,  0,  0,  0, 35, 35, 35},
   { 65, 65,  0,  0,  0, 65, 65,  0},
   { 96, 96,  0,  0,  0, 96, 96, 96},
   {  0,160,160,160,160,  0,  0,  0},
   {  0,  0,160,160,160,  0,  0,  0},
   {  0,  0,  0,  0,  0,  0,  0,  0}  }   // C=
};

#ifdef __cplusplus
} // extern "C"
#endif

#endif
