ageppert/Core-64-Interactive-Core-Memory-Badge/Firmware Source Code/Core-64-Interactive-Core-Memory-Badge/Neon_Pixel_HAL.h

/*
PURPOSE: Set-up and update the NeoPixel Style NEON Pixel Array with non-blocking code through abstract memory buffers.
SETUP: 
USAGE: Init, Clear, Write to one of the buffers in monochrome or color mode, update the LED array.
*/
 
#ifndef NEON_PIXEL_HAL_H
#define NEON_PIXEL_HAL_H

#if (ARDUINO >= 100)
#include <Arduino.h>
#else
#include <WProgram.h>
#endif

#include <stdint.h>

//#ifdef __cplusplus
//extern "C" {
//#endif


// The API 
void Neon_Pixel_Array_Init();					// Called once from Setup. Set up the LED array with the driver using chipset, data pin, color order, correction, brightness from FastLED_Config.h, and clear the array.
void Neon_Pixel_Array_Matrix_Mono_Display();	// Update Neon Pixels from Matrix Array.
void Neon_Pixel_Array_Matrix_String_Display();  // Update Neon Pixels from String Array.
void CopyCoreMemoryToMonochromeNeonPixelArrayMemory(); 
void CopyCoreMemoryToMonochromeNeonPixelArrayMemory();
void Neon_Pixel_Array_Binary_Write_Default();
void Neon_Pixel_Array_Binary_To_Matrix_Mono();
void Neon_Pixel_Array_Matrix_Mono_Write(uint8_t y, uint8_t x, bool value);
bool Neon_Pixel_Array_Matrix_Mono_Read(uint8_t y, uint8_t x);
void Neon_Pixel_Array_String_Write(uint8_t bit, bool value);
void Neon_Pixel_Array_Memory_Clear();
/*
	void Neon_Pixel_Array_Memory_Clear(); 		// Clears all of the LED Array memory buffers.
	void Neon_Pixel_Array_Monochrome_Set_Color(uint8_t hue, uint8_t saturation, uint8_t value); // Overide the default monochrome color for next pixel to be written to the any monochrome memory buffer.

	void Neon_Pixel_Array_Test_Count_Binary(); // Test all 64 LEDs. Counting from 0 to 2^64 from bottom up.
	void Neon_Pixel_Array_Test_Pixel_String(); // Test all 64 LEDs. Turns on 1 pixel, sequentially, from left to right, top to bottom using 1D string addressing
	// Tests four functions: clear, monochrome color change, incrementally write one pixel 1d, display 1d buffer
	void Neon_Pixel_Array_Test_Pixel_Matrix_Mono(); // Test all 64 LEDs. Turns on all LEDs in a row/col, sequentially, from upper left to lower right using 2D matrix addressing
	// Tests four functions: clear, monochrome color change, incrementally write one pixel 2d, display 2d buffer
	void Neon_Pixel_Array_Test_Pixel_Matrix_Color(); // Test all 64 LEDs. Using multi-color symbols.
	// Tests four functions: clear, multi-color symbols, , display 2d buffer
	void Neon_Pixel_Array_Test_Rainbow_Demo();	// Full color demo.

	void Neon_Pixel_Array_Binary_Write(uint64_t BinaryValue);
	uint64_t Neon_Pixel_Array_Binary_Read();
	void Neon_Pixel_Array_String_Write(uint8_t bit, bool value);
	void Neon_Pixel_Array_Matrix_Mono_Write(uint8_t y, uint8_t x, bool value);
	bool Neon_Pixel_Array_Matrix_Mono_Read(uint8_t y, uint8_t x);
	void Neon_Pixel_Array_Matrix_Color_Write(uint8_t y, uint8_t x, uint8_t hue);

	void Neon_Pixel_Array_Binary_Display();
	void Neon_Pixel_Array_String_Display();
	void Neon_Pixel_Array_Matrix_Mono_Display();
	void Neon_Pixel_Array_Matrix_Color_Display();

	void Neon_Pixel_Array_Binary_Write_Default(); // Set the Binary memory to it's default value
	void Neon_Pixel_Array_Binary_To_Matrix_Mono(); // convert the contents of the 64 Bit Binary screen memory to 8x8 Matrix Monochrome memory
	void Neon_Pixel_Array_Matrix_Mono_to_Binary(); // convert the contesnt of 8x8 Matrix Monochrome memory to the 64 Bit Binary Screen Memory

	void Neon_Pixel_Array_Auto_Brightness();	// If ambient light sensor is available, use to adjust LED Array brightness
*/

//#ifdef __cplusplus
//} // extern "C"
//#endif

#endif // NEON_PIXEL_HAL_H
