ageppert/Core-64-Interactive-Core-Memory-Badge/Firmware Source Code/Core-64-Interactive-Core-Memory-Badge/Serial_Debug.c

#include <stdint.h>
// #include <stdbool.h>
// #include <HardwareSerial.h>
#if (ARDUINO >= 100)
#include <Arduino.h>
#else
#include <WProgram.h>
#endif

// TO DO: Consider using a <FastSerial.h> library?

void SerialDebugSetup() {
  // Serial.begin(SERIAL_PORT_SPEED);
  // Serial.println();
  // Serial.println("Serial Debug Port Started in Serial_Debug.c");
}

void SerialDebugProcess() {

}
