ageppert/Core-64-Interactive-Core-Memory-Badge/Firmware Source Code/Core-64-Interactive-Core-Memory-Badge/Analog_Input_Test.h

/*
PURPOSE: Test the ANANLOG input pins that are planned for reading battery voltage and/or current with non-blocking code
SETUP:
- Configure in Analog_Input_Test.c
*/
 
#ifndef ANALOG_INPUT_TEST_H
#define ANALOG_INPUT_TEST_H

#if (ARDUINO >= 100)
#include <Arduino.h>
#else
#include <WProgram.h>
#endif

#include <stdint.h>

//#ifdef __cplusplus
//extern "C" {
//#endif
uint16_t GetBatteryVoltagemV();
float 	 GetBatteryVoltageV();
void AnalogSetup();
void AnalogUpdate();

//#ifdef __cplusplus
//} // extern "C"
//#endif

#endif
